LeoWatti99/CANTram-Framework/Doxygen/latex/d3/db6/_c_a_n_tram_framework_8h_source.tex

\doxysection{CANTram\+Framework.\+h}
\hypertarget{_c_a_n_tram_framework_8h_source}{}\label{_c_a_n_tram_framework_8h_source}\index{C:/Users/leowa/Documents/PlatformIO/Projects/CANTramFrameworkUsage/lib/CANTramFramework/include/CANTramFramework.h@{C:/Users/leowa/Documents/PlatformIO/Projects/CANTramFrameworkUsage/lib/CANTramFramework/include/CANTramFramework.h}}

\begin{DoxyCode}{0}
\DoxyCodeLine{00001\ \textcolor{preprocessor}{\#ifndef\ CAN\_TRAM\_FRAMEWORK\_H}}
\DoxyCodeLine{00002\ \textcolor{preprocessor}{\#define\ CAN\_TRAM\_FRAMEWORK\_H}}
\DoxyCodeLine{00003\ }
\DoxyCodeLine{00004\ \textcolor{preprocessor}{\#include\ <\mbox{\hyperlink{_c_a_n_core_8h}{CANCore.h}}>}}
\DoxyCodeLine{00005\ \textcolor{preprocessor}{\#include\ <\mbox{\hyperlink{_c_a_n_tram_core_8h}{CANTramCore.h}}>}}
\DoxyCodeLine{00006\ \textcolor{preprocessor}{\#include\ <\mbox{\hyperlink{_c_a_n_tram_module_8h}{CANTramModule.h}}>}}
\DoxyCodeLine{00007\ \textcolor{preprocessor}{\#include\ <\mbox{\hyperlink{_hardware_resource_8h}{HardwareResource.h}}>}}
\DoxyCodeLine{00008\ \textcolor{preprocessor}{\#include\ <I2CCore.h>}}
\DoxyCodeLine{00009\ \textcolor{preprocessor}{\#include\ <Interface.h>}}
\DoxyCodeLine{00010\ \textcolor{preprocessor}{\#include\ <\mbox{\hyperlink{_output_definition_8h}{OutputDefinition.h}}>}}
\DoxyCodeLine{00011\ \textcolor{preprocessor}{\#include\ <\mbox{\hyperlink{_p_w_m_core_8h}{PWMCore.h}}>}}
\DoxyCodeLine{00012\ \textcolor{preprocessor}{\#include\ <SPIChip.h>}}
\DoxyCodeLine{00013\ \textcolor{preprocessor}{\#include\ <\mbox{\hyperlink{_u_a_r_t_core_8h}{UARTCore.h}}>}}
\DoxyCodeLine{00014\ \textcolor{preprocessor}{\#include\ <ISO1H816G.h>}}
\DoxyCodeLine{00015\ \textcolor{preprocessor}{\#include\ <ISO1I813T.h>}}
\DoxyCodeLine{00016\ \textcolor{preprocessor}{\#include\ <ISO1I813T\_registers.h>}}
\DoxyCodeLine{00017\ \textcolor{preprocessor}{\#include\ <\mbox{\hyperlink{_m_a_x22531_8h}{MAX22531.h}}>}}
\DoxyCodeLine{00018\ \textcolor{preprocessor}{\#include\ <MAX22531\_registers.h>}}
\DoxyCodeLine{00019\ \textcolor{preprocessor}{\#include\ <\mbox{\hyperlink{_e_s_p32___c_a_n_core_8h}{ESP32\_CANCore.h}}>}}
\DoxyCodeLine{00020\ \textcolor{preprocessor}{\#include\ <ESP32\_I2CCore.h>}}
\DoxyCodeLine{00021\ \textcolor{preprocessor}{\#include\ <ESP32\_UART.h>}}
\DoxyCodeLine{00022\ \textcolor{preprocessor}{\#include\ <ESP32PWMCore.h>}}
\DoxyCodeLine{00023\ \textcolor{preprocessor}{\#include\ <AnalogInput.h>}}
\DoxyCodeLine{00024\ \textcolor{preprocessor}{\#include\ <AnalogOutput.h>}}
\DoxyCodeLine{00025\ \textcolor{preprocessor}{\#include\ <\mbox{\hyperlink{_c_a_n_interface_8h}{CANInterface.h}}>}}
\DoxyCodeLine{00026\ \textcolor{preprocessor}{\#include\ <DigitalInput.h>}}
\DoxyCodeLine{00027\ \textcolor{preprocessor}{\#include\ <DigitalOutput.h>}}
\DoxyCodeLine{00028\ \textcolor{preprocessor}{\#include\ <I2CInterface.h>}}
\DoxyCodeLine{00029\ \textcolor{preprocessor}{\#include\ <RelaisInterface.h>}}
\DoxyCodeLine{00030\ \textcolor{preprocessor}{\#include\ <UARTInterface.h>}}
\DoxyCodeLine{00031\ \textcolor{preprocessor}{\#include\ <\mbox{\hyperlink{_debug_8h}{Debug.h}}>}}
\DoxyCodeLine{00032\ \textcolor{preprocessor}{\#include\ <AnalogModuleV1\_0.h>}}
\DoxyCodeLine{00033\ \textcolor{preprocessor}{\#include\ <BusModule.h>}}
\DoxyCodeLine{00034\ \textcolor{preprocessor}{\#include\ <DigitalModuleV1\_0.h>}}
\DoxyCodeLine{00035\ \textcolor{preprocessor}{\#include\ <\mbox{\hyperlink{_main_module_v1__0_8h}{MainModuleV1\_0.h}}>}}
\DoxyCodeLine{00036\ \textcolor{preprocessor}{\#include\ <RelaisModuleV1\_0.h>}}
\DoxyCodeLine{00037\ }
\DoxyCodeLine{00038\ \textcolor{preprocessor}{\#endif}}

\end{DoxyCode}
