LeoWatti99/CANTram-Framework/Doxygen/latex/d3/dc5/_c_a_n_core_8h.tex

\doxysection{C\+:/\+Users/leowa/\+Documents/\+Platform\+IO/\+Projects/\+CANTram\+Framework\+Usage/lib/\+CANTram\+Framework/include/\+CANCore.h File Reference}
\hypertarget{_c_a_n_core_8h}{}\label{_c_a_n_core_8h}\index{C:/Users/leowa/Documents/PlatformIO/Projects/CANTramFrameworkUsage/lib/CANTramFramework/include/CANCore.h@{C:/Users/leowa/Documents/PlatformIO/Projects/CANTramFrameworkUsage/lib/CANTramFramework/include/CANCore.h}}

Declaration of the \doxylink{class_c_a_n_core}{CANCore} class.  

{\ttfamily \#include $<$Arduino.\+h$>$}\newline
{\ttfamily \#include "{}Hardware\+Resource.\+h"{}}\newline
{\ttfamily \#include "{}Debug.\+h"{}}\newline
Include dependency graph for CANCore.\+h\+:
\nopagebreak
\begin{figure}[H]
\begin{center}
\leavevmode
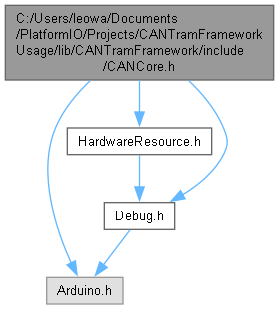
[picture p11: Doxygen/html/d0/d9a/_c_a_n_core_8h__incl.png]

\end{center}
\end{figure}
This graph shows which files directly or indirectly include this file\+:
\nopagebreak
\begin{figure}[H]
\begin{center}
\leavevmode
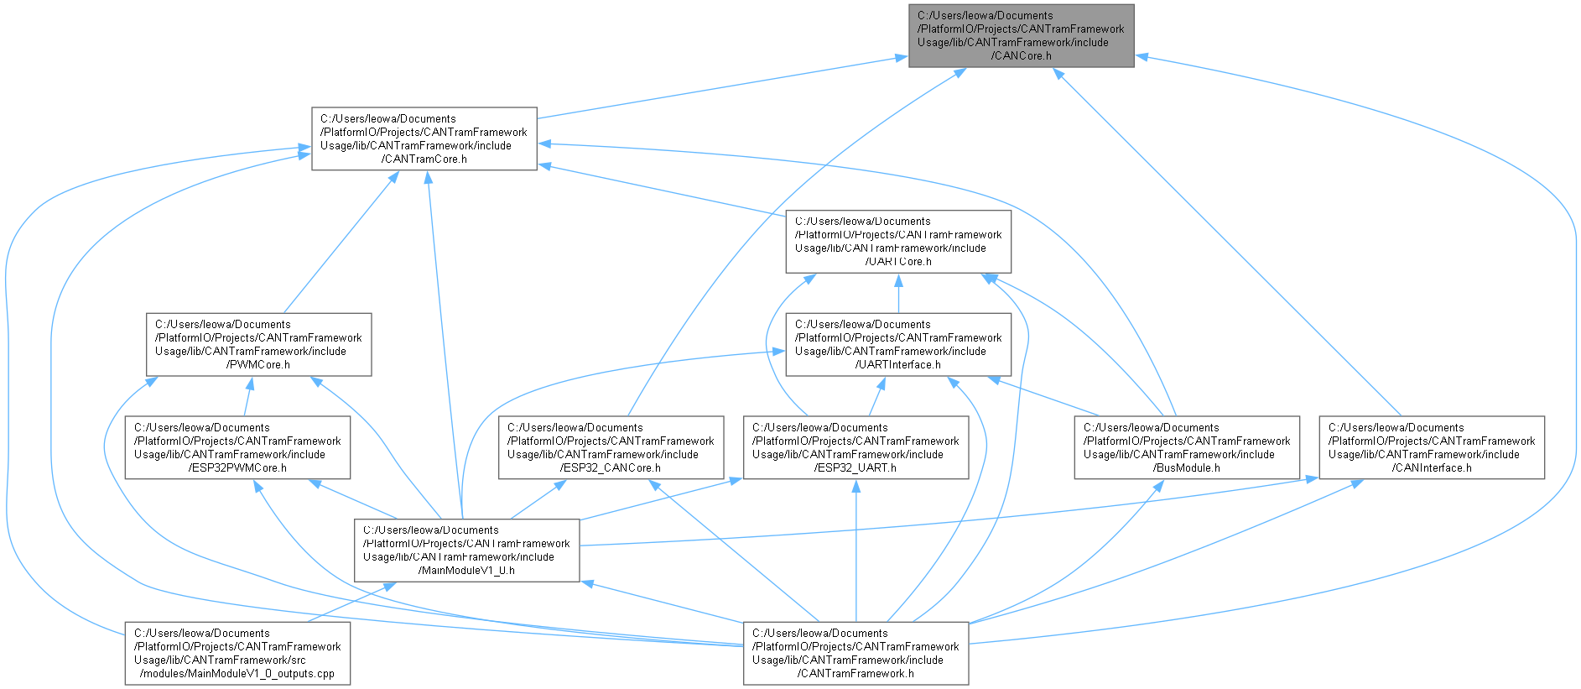
[picture p12: Doxygen/html/d0/ddd/_c_a_n_core_8h__dep__incl.png]

\end{center}
\end{figure}
\doxysubsubsection*{Classes}
\begin{DoxyCompactItemize}
\item 
class \mbox{\hyperlink{class_c_a_n_core}{CANCore}}
\item 
struct \mbox{\hyperlink{struct_c_a_n_core_1_1_c_a_n_message}{CANCore\+::\+CANMessage}}
\end{DoxyCompactItemize}

\doxysubsection{Detailed Description}
Declaration of the \doxylink{class_c_a_n_core}{CANCore} class. 

Defines the \doxylink{class_c_a_n_core}{CANCore} class which provides core functionalities for CAN bus operations in the CANTram system.
