LeoWatti99/CANTram-Framework/Doxygen/latex/d6/d86/_e_s_p32___c_a_n_core_8h.tex

\doxysection{C\+:/\+Users/leowa/\+Documents/\+Platform\+IO/\+Projects/\+CANTram\+Framework\+Usage/lib/\+CANTram\+Framework/include/\+ESP32\+\_\+\+CANCore.h File Reference}
\hypertarget{_e_s_p32___c_a_n_core_8h}{}\label{_e_s_p32___c_a_n_core_8h}\index{C:/Users/leowa/Documents/PlatformIO/Projects/CANTramFrameworkUsage/lib/CANTramFramework/include/ESP32\_CANCore.h@{C:/Users/leowa/Documents/PlatformIO/Projects/CANTramFrameworkUsage/lib/CANTramFramework/include/ESP32\_CANCore.h}}

Declaration of the \doxylink{class_e_s_p32___c_a_n_core}{ESP32\+\_\+\+CANCore} class.  

{\ttfamily \#include "{}CANCore.\+h"{}}\newline
Include dependency graph for ESP32\+\_\+\+CANCore.\+h\+:
\nopagebreak
\begin{figure}[H]
\begin{center}
\leavevmode
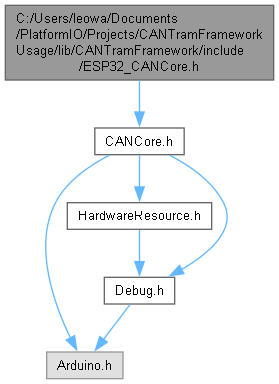
[picture p17: Doxygen/html/d8/d5a/_e_s_p32___c_a_n_core_8h__incl.png]

\end{center}
\end{figure}
This graph shows which files directly or indirectly include this file\+:
\nopagebreak
\begin{figure}[H]
\begin{center}
\leavevmode
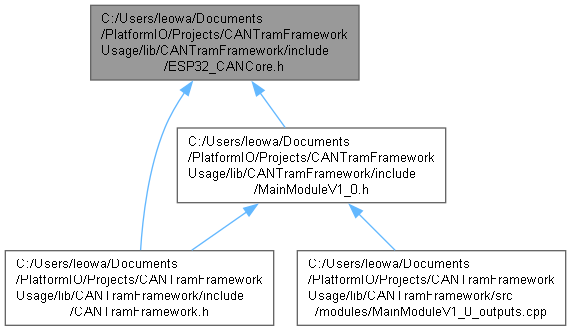
[picture p18: Doxygen/html/d0/d6d/_e_s_p32___c_a_n_core_8h__dep__incl.png]

\end{center}
\end{figure}
\doxysubsubsection*{Classes}
\begin{DoxyCompactItemize}
\item 
class \mbox{\hyperlink{class_e_s_p32___c_a_n_core}{ESP32\+\_\+\+CANCore}}
\end{DoxyCompactItemize}

\doxysubsection{Detailed Description}
Declaration of the \doxylink{class_e_s_p32___c_a_n_core}{ESP32\+\_\+\+CANCore} class. 

Defines the \doxylink{class_e_s_p32___c_a_n_core}{ESP32\+\_\+\+CANCore} class which implements \doxylink{class_c_a_n_core}{CANCore} functionalities for the ESP32 platform using the TWAI driver.
