LeoWatti99/CANTram-Framework/Doxygen/latex/d7/d6e/class_i_s_o1_i813_t.tex

\doxysection{ISO1\+I813T Class Reference}
\hypertarget{class_i_s_o1_i813_t}{}\label{class_i_s_o1_i813_t}\index{ISO1I813T@{ISO1I813T}}

Inheritance diagram for ISO1\+I813T\+:
\nopagebreak
\begin{figure}[H]
\begin{center}
\leavevmode

\end{center}
\end{figure}

Collaboration diagram for ISO1\+I813T\+:
\nopagebreak
\begin{figure}[H]
\begin{center}
\leavevmode

\end{center}
\end{figure}
\doxysubsubsection*{Classes}
\begin{DoxyCompactItemize}
\item 
struct \mbox{\hyperlink{struct_i_s_o1_i813_t_1_1_data}{Data}}
\item 
struct \mbox{\hyperlink{struct_i_s_o1_i813_t_1_1_diag}{Diag}}
\end{DoxyCompactItemize}
\doxysubsubsection*{Public Types}
\begin{DoxyCompactItemize}
\item 
\Hypertarget{class_i_s_o1_i813_t_a42aab5b82c6fc3c49c0b7afa2e7dd207}\label{class_i_s_o1_i813_t_a42aab5b82c6fc3c49c0b7afa2e7dd207} 
enum {\bfseries ISO1\+I813\+T\+\_\+\+Filter} \{ \newline
{\bfseries US\+\_\+50}
, {\bfseries US\+\_\+100}
, {\bfseries US\+\_\+400}
, {\bfseries US\+\_\+800}
, \newline
{\bfseries US\+\_\+1600}
, {\bfseries US\+\_\+3200}
, {\bfseries US\+\_\+10000}
, {\bfseries US\+\_\+20000}
, \newline
{\bfseries FILTER\+\_\+\+OFF}
 \}
\item 
\Hypertarget{class_i_s_o1_i813_t_a82c741cb96c0a4d718da24f12c4746e2}\label{class_i_s_o1_i813_t_a82c741cb96c0a4d718da24f12c4746e2} 
enum {\bfseries ERROR\+\_\+\+CODES} \{ {\bfseries STATUS\+\_\+\+OK} = 0
, {\bfseries INVALID\+\_\+\+CHANNEL} = 10
, {\bfseries INVALID\+\_\+\+FILTER} = 11
, {\bfseries WIRE\+\_\+\+BREAK\+\_\+\+SETTING\+\_\+\+ERROR} = 30
 \}
\end{DoxyCompactItemize}
\doxysubsubsection*{Public Member Functions}
\begin{DoxyCompactItemize}
\item 
\Hypertarget{class_i_s_o1_i813_t_a4baa38cefab23792cde1ddf46cff37d1}\label{class_i_s_o1_i813_t_a4baa38cefab23792cde1ddf46cff37d1} 
{\bfseries ISO1\+I813T} (uint8\+\_\+t cs\+Pin, uint8\+\_\+t sync\+Pin)
\item 
\Hypertarget{class_i_s_o1_i813_t_abe3138513af0bc02e8f47bed0406683e}\label{class_i_s_o1_i813_t_abe3138513af0bc02e8f47bed0406683e} 
void {\bfseries write\+Register} (uint8\+\_\+t address, uint8\+\_\+t data)
\item 
\Hypertarget{class_i_s_o1_i813_t_ab50782d8c2683061052170cc237ac49b}\label{class_i_s_o1_i813_t_ab50782d8c2683061052170cc237ac49b} 
uint8\+\_\+t {\bfseries read\+Register} (uint8\+\_\+t address)
\item 
\Hypertarget{class_i_s_o1_i813_t_af2d28f0eb8b07fd7517ff81d8e09367a}\label{class_i_s_o1_i813_t_af2d28f0eb8b07fd7517ff81d8e09367a} 
void {\bfseries set\+Pins} (uint8\+\_\+t cs\+Pin, uint8\+\_\+t sync\+Pin=-\/1)
\item 
\Hypertarget{class_i_s_o1_i813_t_a23c8c99117d962e3b51f4efae813aec4}\label{class_i_s_o1_i813_t_a23c8c99117d962e3b51f4efae813aec4} 
void {\bfseries begin} ()
\item 
\Hypertarget{class_i_s_o1_i813_t_a7325ff458c752f26bf27cabcd8d4d6ff}\label{class_i_s_o1_i813_t_a7325ff458c752f26bf27cabcd8d4d6ff} 
uint8\+\_\+t {\bfseries get\+Inputs} ()
\item 
\Hypertarget{class_i_s_o1_i813_t_aee537c3332f95e61ade023d4acf195e2}\label{class_i_s_o1_i813_t_aee537c3332f95e61ade023d4acf195e2} 
bool {\bfseries get\+Input} (uint8\+\_\+t input)
\item 
\Hypertarget{class_i_s_o1_i813_t_afcc9b3376d2c442042a8f36f9fd4d59f}\label{class_i_s_o1_i813_t_afcc9b3376d2c442042a8f36f9fd4d59f} 
\mbox{\hyperlink{struct_i_s_o1_i813_t_1_1_data}{Data}} {\bfseries fetch\+Data} ()
\item 
\Hypertarget{class_i_s_o1_i813_t_a2181a4c737b8f0cec97212acc306c83f}\label{class_i_s_o1_i813_t_a2181a4c737b8f0cec97212acc306c83f} 
\mbox{\hyperlink{struct_i_s_o1_i813_t_1_1_diag}{Diag}} {\bfseries fetch\+Diagnose} ()
\item 
\Hypertarget{class_i_s_o1_i813_t_a9680f671fad5368a4dfbb839700f3ed9}\label{class_i_s_o1_i813_t_a9680f671fad5368a4dfbb839700f3ed9} 
uint8\+\_\+t {\bfseries get\+Wire\+Breaks} ()
\item 
\Hypertarget{class_i_s_o1_i813_t_a492202752ef7087ae91dc99e281cd949}\label{class_i_s_o1_i813_t_a492202752ef7087ae91dc99e281cd949} 
bool {\bfseries get\+Wire\+Break} (uint8\+\_\+t wire\+Break)
\item 
\Hypertarget{class_i_s_o1_i813_t_a8fd46c416d5030966d563f9b947dea76}\label{class_i_s_o1_i813_t_a8fd46c416d5030966d563f9b947dea76} 
uint8\+\_\+t {\bfseries set\+Filter} (uint8\+\_\+t channel, ISO1\+I813\+T\+\_\+\+Filter filter)
\item 
\Hypertarget{class_i_s_o1_i813_t_af984ac04ddbef183cb829c80e3815a64}\label{class_i_s_o1_i813_t_af984ac04ddbef183cb829c80e3815a64} 
uint8\+\_\+t {\bfseries set\+Wire\+Break\+Mask} (uint8\+\_\+t channel, bool enable)
\item 
\Hypertarget{class_i_s_o1_i813_t_aa368e087610499e5ae2642f13d96b8a2}\label{class_i_s_o1_i813_t_aa368e087610499e5ae2642f13d96b8a2} 
void {\bfseries freeze} (bool status)
\end{DoxyCompactItemize}
\doxysubsection*{Public Member Functions inherited from \mbox{\hyperlink{class_s_p_i_chip}{SPIChip}}}
\begin{DoxyCompactItemize}
\item 
void {\bfseries activate\+External\+Chip\+Select} ()
\item 
void {\bfseries set\+CSControl\+Callback} (std\+::function$<$ void(bool)$>$ callback)
\item 
void {\bfseries set\+CSPin} (int cs\+Pin)
\end{DoxyCompactItemize}
\doxysubsubsection*{Public Attributes}
\begin{DoxyCompactItemize}
\item 
\Hypertarget{class_i_s_o1_i813_t_a39b30922d58a05b78316fbc46ef48615}\label{class_i_s_o1_i813_t_a39b30922d58a05b78316fbc46ef48615} 
uint8\+\_\+t {\bfseries daisy\+Chain} = 1
\end{DoxyCompactItemize}
\doxysubsubsection*{Additional Inherited Members}
\doxysubsection*{Protected Member Functions inherited from \mbox{\hyperlink{class_s_p_i_chip}{SPIChip}}}
\begin{DoxyCompactItemize}
\item 
{\bfseries SPIChip} (uint8\+\_\+t cs\+Pin)
\item 
void {\bfseries select\+Chip} ()
\item 
void {\bfseries deselect\+Chip} ()
\end{DoxyCompactItemize}
\doxysubsection*{Protected Attributes inherited from \mbox{\hyperlink{class_s_p_i_chip}{SPIChip}}}
\begin{DoxyCompactItemize}
\item 
int {\bfseries \+\_\+cs\+Pin}
\item 
bool {\bfseries use\+External\+Chip\+Select} = false
\item 
std\+::function$<$ void(bool)$>$ {\bfseries cs\+Control} = nullptr
\end{DoxyCompactItemize}

The documentation for this class was generated from the following files\+:\begin{DoxyCompactItemize}
\item 
C\+:/\+Users/leowa/\+Documents/\+Platform\+IO/\+Projects/\+CANTram\+Framework\+Usage/lib/\+CANTram\+Framework/include/ISO1\+I813\+T.\+h\item 
C\+:/\+Users/leowa/\+Documents/\+Platform\+IO/\+Projects/\+CANTram\+Framework\+Usage/lib/\+CANTram\+Framework/src/chips/\+ISO1\+I813\+T/ISO1\+I813\+T.\+cpp\end{DoxyCompactItemize}
