LeoWatti99/CANTram-Framework/Doxygen/latex/d8/d12/_u_a_r_t_core_8h.tex

\doxysection{C\+:/\+Users/leowa/\+Documents/\+Platform\+IO/\+Projects/\+CANTram\+Framework\+Usage/lib/\+CANTram\+Framework/include/\+UARTCore.h File Reference}
\hypertarget{_u_a_r_t_core_8h}{}\label{_u_a_r_t_core_8h}\index{C:/Users/leowa/Documents/PlatformIO/Projects/CANTramFrameworkUsage/lib/CANTramFramework/include/UARTCore.h@{C:/Users/leowa/Documents/PlatformIO/Projects/CANTramFrameworkUsage/lib/CANTramFramework/include/UARTCore.h}}

Abstract base for UART hardware cores and provider interface.  

{\ttfamily \#include "{}CANTram\+Core.\+h"{}}\newline
{\ttfamily \#include "{}Hardware\+Resource.\+h"{}}\newline
Include dependency graph for UARTCore.\+h\+:
\nopagebreak
\begin{figure}[H]
\begin{center}
\leavevmode
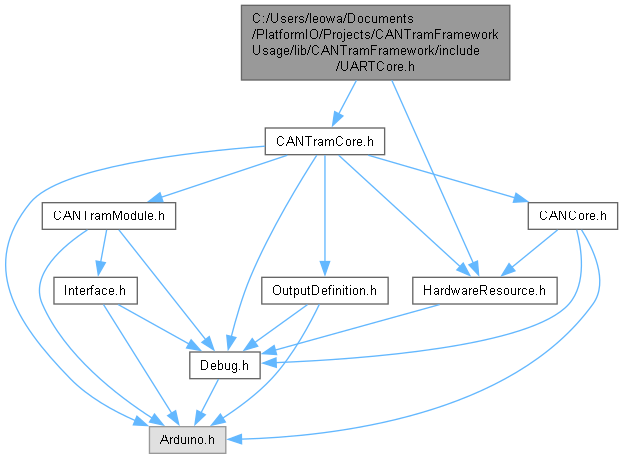
[picture p19: Doxygen/html/d1/db5/_u_a_r_t_core_8h__incl.png]

\end{center}
\end{figure}
This graph shows which files directly or indirectly include this file\+:
\nopagebreak
\begin{figure}[H]
\begin{center}
\leavevmode
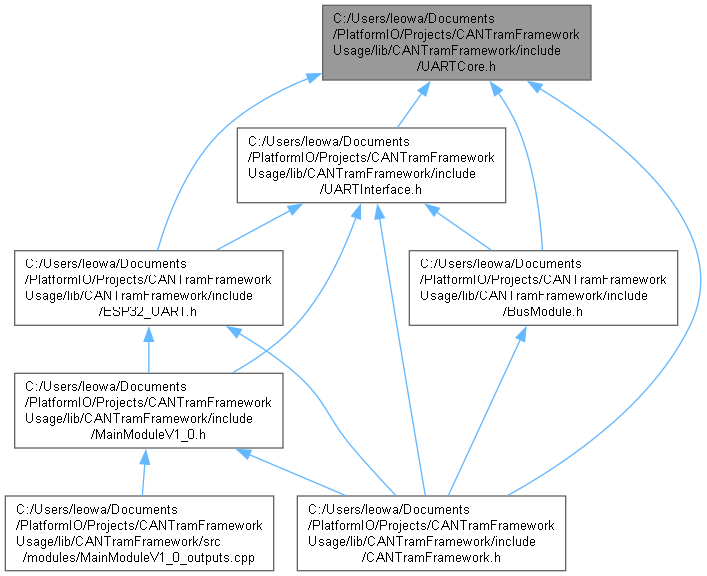
[picture p20: Doxygen/html/d3/d5a/_u_a_r_t_core_8h__dep__incl.png]

\end{center}
\end{figure}
\doxysubsubsection*{Classes}
\begin{DoxyCompactItemize}
\item 
class \mbox{\hyperlink{class_u_a_r_t_core}{UARTCore}}
\begin{DoxyCompactList}\small\item\em Base class for platform-\/specific UART implementations. \end{DoxyCompactList}\item 
class \mbox{\hyperlink{class_u_a_r_t_provider}{UARTProvider}}
\begin{DoxyCompactList}\small\item\em Abstract interface for objects that supply a \doxylink{class_u_a_r_t_core}{UARTCore} instance. \end{DoxyCompactList}\end{DoxyCompactItemize}

\doxysubsection{Detailed Description}
Abstract base for UART hardware cores and provider interface. 

Define the abstract \doxylink{class_u_a_r_t_core}{UARTCore} class which concrete platform implementations must inherit. Provides methods for installation, configuration, pin setup and data IO. Also defines the \doxylink{class_u_a_r_t_provider}{UARTProvider} interface used to obtain \doxylink{class_u_a_r_t_core}{UARTCore} instances.
