LeoWatti99/CANTram-Framework/Doxygen/latex/d8/d9a/class_i_s_o1_h816_g.tex

\doxysection{ISO1\+H816G Class Reference}
\hypertarget{class_i_s_o1_h816_g}{}\label{class_i_s_o1_h816_g}\index{ISO1H816G@{ISO1H816G}}

Inheritance diagram for ISO1\+H816G\+:
\nopagebreak
\begin{figure}[H]
\begin{center}
\leavevmode

\end{center}
\end{figure}

Collaboration diagram for ISO1\+H816G\+:
\nopagebreak
\begin{figure}[H]
\begin{center}
\leavevmode

\end{center}
\end{figure}
\doxysubsubsection*{Public Types}
\begin{DoxyCompactItemize}
\item 
\Hypertarget{class_i_s_o1_h816_g_af6eed698acab2a5f10210b2eef321121}\label{class_i_s_o1_h816_g_af6eed698acab2a5f10210b2eef321121} 
enum {\bfseries ERROR\+\_\+\+CODES} \{ \newline
{\bfseries STATUS\+\_\+\+OK} = 0
, {\bfseries NOT\+\_\+\+INITIALIZED} = 5
, {\bfseries INVALID\+\_\+\+CHANNEL} = 10
, {\bfseries SPI\+\_\+\+FAULT} = 20
, \newline
{\bfseries DISABLE\+\_\+\+PIN\+\_\+\+NOT\+\_\+\+SET} = 30
, {\bfseries DIAG\+\_\+\+PIN\+\_\+\+NOT\+\_\+\+SET} = 40
 \}
\end{DoxyCompactItemize}
\doxysubsubsection*{Public Member Functions}
\begin{DoxyCompactItemize}
\item 
\Hypertarget{class_i_s_o1_h816_g_a287216b98d403aed82645e2dac912a15}\label{class_i_s_o1_h816_g_a287216b98d403aed82645e2dac912a15} 
{\bfseries ISO1\+H816G} (uint8\+\_\+t cs\+Pin, uint8\+\_\+t dis\+Pin, uint8\+\_\+t diag\+Pin)
\item 
\Hypertarget{class_i_s_o1_h816_g_a6be2ce89318f55909b8fb2b3a2eb3ab9}\label{class_i_s_o1_h816_g_a6be2ce89318f55909b8fb2b3a2eb3ab9} 
uint8\+\_\+t {\bfseries begin} ()
\item 
\Hypertarget{class_i_s_o1_h816_g_a6862f2bd9ec8d1830cd48733bd7ebd14}\label{class_i_s_o1_h816_g_a6862f2bd9ec8d1830cd48733bd7ebd14} 
uint8\+\_\+t {\bfseries enable} ()
\item 
\Hypertarget{class_i_s_o1_h816_g_aa518c307897e8098639198e34141f40d}\label{class_i_s_o1_h816_g_aa518c307897e8098639198e34141f40d} 
void {\bfseries disable} ()
\item 
\Hypertarget{class_i_s_o1_h816_g_a803dedb704558920da8fc78956206d85}\label{class_i_s_o1_h816_g_a803dedb704558920da8fc78956206d85} 
bool {\bfseries is\+Enabled} ()
\item 
\Hypertarget{class_i_s_o1_h816_g_a3d545570da0dd21fda6b7d187ccd3b24}\label{class_i_s_o1_h816_g_a3d545570da0dd21fda6b7d187ccd3b24} 
uint8\+\_\+t {\bfseries set\+Outputs} (uint8\+\_\+t outputs)
\item 
\Hypertarget{class_i_s_o1_h816_g_a630682008a651306e4255107a6b2e5fd}\label{class_i_s_o1_h816_g_a630682008a651306e4255107a6b2e5fd} 
uint8\+\_\+t {\bfseries set\+Output} (uint8\+\_\+t output, bool state)
\item 
\Hypertarget{class_i_s_o1_h816_g_ae2383a99d0c07a78625308c2fd7bb1b4}\label{class_i_s_o1_h816_g_ae2383a99d0c07a78625308c2fd7bb1b4} 
uint8\+\_\+t {\bfseries get\+Outputs} ()
\item 
\Hypertarget{class_i_s_o1_h816_g_aa43319850e8a185467ca2f6811e48373}\label{class_i_s_o1_h816_g_aa43319850e8a185467ca2f6811e48373} 
bool {\bfseries get\+Output} (uint8\+\_\+t output)
\item 
\Hypertarget{class_i_s_o1_h816_g_a2dd3c3dd83b7898c980666cba3d495a4}\label{class_i_s_o1_h816_g_a2dd3c3dd83b7898c980666cba3d495a4} 
void {\bfseries set\+SPISettings} (uint32\+\_\+t speed, uint8\+\_\+t bit\+Order, uint8\+\_\+t data\+Mode)
\item 
\Hypertarget{class_i_s_o1_h816_g_aca09498a306a0f11e4bddd8caabd8dc8}\label{class_i_s_o1_h816_g_aca09498a306a0f11e4bddd8caabd8dc8} 
void {\bfseries On\+Fault} (void(\texorpdfstring{$\ast$}{*}callback)(void))
\item 
\Hypertarget{class_i_s_o1_h816_g_a43404bb395036e952a2c7e238e063315}\label{class_i_s_o1_h816_g_a43404bb395036e952a2c7e238e063315} 
void {\bfseries set\+Pins} (uint8\+\_\+t cs\+Pin, uint8\+\_\+t dis\+Pin=-\/1, uint8\+\_\+t diag\+Pin=-\/1)
\end{DoxyCompactItemize}
\doxysubsection*{Public Member Functions inherited from \mbox{\hyperlink{class_s_p_i_chip}{SPIChip}}}
\begin{DoxyCompactItemize}
\item 
void {\bfseries activate\+External\+Chip\+Select} ()
\item 
void {\bfseries set\+CSControl\+Callback} (std\+::function$<$ void(bool)$>$ callback)
\item 
void {\bfseries set\+CSPin} (int cs\+Pin)
\end{DoxyCompactItemize}
\doxysubsubsection*{Additional Inherited Members}
\doxysubsection*{Protected Member Functions inherited from \mbox{\hyperlink{class_s_p_i_chip}{SPIChip}}}
\begin{DoxyCompactItemize}
\item 
{\bfseries SPIChip} (uint8\+\_\+t cs\+Pin)
\item 
void {\bfseries select\+Chip} ()
\item 
void {\bfseries deselect\+Chip} ()
\end{DoxyCompactItemize}
\doxysubsection*{Protected Attributes inherited from \mbox{\hyperlink{class_s_p_i_chip}{SPIChip}}}
\begin{DoxyCompactItemize}
\item 
int {\bfseries \+\_\+cs\+Pin}
\item 
bool {\bfseries use\+External\+Chip\+Select} = false
\item 
std\+::function$<$ void(bool)$>$ {\bfseries cs\+Control} = nullptr
\end{DoxyCompactItemize}

The documentation for this class was generated from the following files\+:\begin{DoxyCompactItemize}
\item 
C\+:/\+Users/leowa/\+Documents/\+Platform\+IO/\+Projects/\+CANTram\+Framework\+Usage/lib/\+CANTram\+Framework/include/ISO1\+H816\+G.\+h\item 
C\+:/\+Users/leowa/\+Documents/\+Platform\+IO/\+Projects/\+CANTram\+Framework\+Usage/lib/\+CANTram\+Framework/src/chips/\+ISO1\+H816\+G/ISO1\+H816\+G.\+cpp\end{DoxyCompactItemize}
