LeoWatti99/CANTram-Framework/Doxygen/latex/d9/d06/class_c_a_n_core.tex

\doxysection{CANCore Class Reference}
\hypertarget{class_c_a_n_core}{}\label{class_c_a_n_core}\index{CANCore@{CANCore}}

Inheritance diagram for CANCore\+:
\nopagebreak
\begin{figure}[H]
\begin{center}
\leavevmode
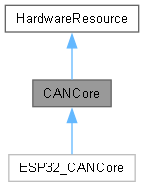
[picture p21: Doxygen/html/d1/d0d/class_c_a_n_core__inherit__graph.png]

\end{center}
\end{figure}

Collaboration diagram for CANCore\+:
\nopagebreak
\begin{figure}[H]
\begin{center}
\leavevmode

\end{center}
\end{figure}
\doxysubsubsection*{Classes}
\begin{DoxyCompactItemize}
\item 
struct \mbox{\hyperlink{struct_c_a_n_core_1_1_c_a_n_message}{CANMessage}}
\end{DoxyCompactItemize}
\doxysubsubsection*{Public Types}
\begin{DoxyCompactItemize}
\item 
\Hypertarget{class_c_a_n_core_a5766804a2230f83a13111a6a9b465e87}\label{class_c_a_n_core_a5766804a2230f83a13111a6a9b465e87} 
enum {\bfseries Baudrate} \{ \newline
{\bfseries BR\+\_\+\+NOT\+\_\+\+SET} = 0
, {\bfseries BR\+\_\+125K} = 125000
, {\bfseries BR\+\_\+250K} = 250000
, {\bfseries BR\+\_\+500K} = 500000
, \newline
{\bfseries BR\+\_\+1M} = 1000000
 \}
\item 
\Hypertarget{class_c_a_n_core_afa2d8dcf4f9255c223f5819e0167cc83}\label{class_c_a_n_core_afa2d8dcf4f9255c223f5819e0167cc83} 
enum {\bfseries Status} \{ {\bfseries STATUS\+\_\+\+OK}
, {\bfseries STATUS\+\_\+\+ERROR\+\_\+\+ACTIVE}
, {\bfseries STATUS\+\_\+\+BUS\+\_\+\+OFF}
, {\bfseries STATUS\+\_\+\+ERROR\+\_\+\+PASSIVE}
 \}
\item 
\Hypertarget{class_c_a_n_core_a78a0c4b32f1455438d9f379c3e659d21}\label{class_c_a_n_core_a78a0c4b32f1455438d9f379c3e659d21} 
enum {\bfseries Filter\+Type} \{ {\bfseries FILTER\+\_\+\+ACCEPT\+\_\+\+ALL}
, {\bfseries FILTER\+\_\+\+MATCH\+\_\+\+ID}
, {\bfseries FILTER\+\_\+\+MASKED}
 \}
\end{DoxyCompactItemize}
\doxysubsection*{Public Types inherited from \mbox{\hyperlink{class_hardware_resource}{Hardware\+Resource}}}
\begin{DoxyCompactItemize}
\item 
enum \mbox{\hyperlink{class_hardware_resource_adead6978be3d7b86c18e3d3e051381e6}{Type}} \{ \newline
\mbox{\hyperlink{class_hardware_resource_adead6978be3d7b86c18e3d3e051381e6ac6f39e4a2dbc764df53048f26209f0a1}{UART}}
, \mbox{\hyperlink{class_hardware_resource_adead6978be3d7b86c18e3d3e051381e6a63a2eead0d2771007afa8c8af281c50d}{SPI}}
, \mbox{\hyperlink{class_hardware_resource_adead6978be3d7b86c18e3d3e051381e6ac77292ec986f613995babba396598dbc}{I2C}}
, \mbox{\hyperlink{class_hardware_resource_adead6978be3d7b86c18e3d3e051381e6ac2fe3e8cc9a9a8fcb39c32be2da214c5}{PWM}}
, \newline
\mbox{\hyperlink{class_hardware_resource_adead6978be3d7b86c18e3d3e051381e6a0ae946256af51077cacc3c0a11575635}{CAN}}
 \}
\begin{DoxyCompactList}\small\item\em Enumeration of hardware resource types. \end{DoxyCompactList}\end{DoxyCompactItemize}
\doxysubsubsection*{Public Member Functions}
\begin{DoxyCompactItemize}
\item 
virtual bool \mbox{\hyperlink{class_c_a_n_core_a26d8d09992a12b0c0f20199dc0e32415}{begin}} ()=0
\item 
virtual bool \mbox{\hyperlink{class_c_a_n_core_a24c2f2e9638aff19ddae3d206e676803}{set\+Baudrate}} (Baudrate baudrate)=0
\item 
virtual bool \mbox{\hyperlink{class_c_a_n_core_ae3b3788f31a71d43bf27116a117a528c}{set\+Pins}} (int8\+\_\+t tx\+Pin, int8\+\_\+t rx\+Pin)=0
\item 
\Hypertarget{class_c_a_n_core_a7a7b37e7eaaee5e9e6445eea8bf2caf9}\label{class_c_a_n_core_a7a7b37e7eaaee5e9e6445eea8bf2caf9} 
virtual bool {\bfseries end} ()=0
\item 
\Hypertarget{class_c_a_n_core_afe4467274cca5fe65f5eb11b5b3e3857}\label{class_c_a_n_core_afe4467274cca5fe65f5eb11b5b3e3857} 
virtual bool {\bfseries send\+Message} (const \mbox{\hyperlink{struct_c_a_n_core_1_1_c_a_n_message}{CANMessage}} \&message)=0
\item 
virtual bool \mbox{\hyperlink{class_c_a_n_core_a615de6f6b06944c4023dc93573bf0c93}{read\+Message}} (\mbox{\hyperlink{struct_c_a_n_core_1_1_c_a_n_message}{CANMessage}} \&message)=0
\item 
virtual uint8\+\_\+t \mbox{\hyperlink{class_c_a_n_core_a0c7c384c24e951410f0ea406f222a889}{available}} ()=0
\item 
\Hypertarget{class_c_a_n_core_a03de55e8a4839a511a65a06f1aeee8b0}\label{class_c_a_n_core_a03de55e8a4839a511a65a06f1aeee8b0} 
virtual bool {\bfseries setup\+Filter} (uint32\+\_\+t id, uint32\+\_\+t mask)=0
\item 
\Hypertarget{class_c_a_n_core_ac71288be80fa6390a5d308fa9a0c5a0f}\label{class_c_a_n_core_ac71288be80fa6390a5d308fa9a0c5a0f} 
Baudrate {\bfseries get\+Baudrate} () const
\item 
\Hypertarget{class_c_a_n_core_a6e3abe29be1ba1a343dc68296787b72e}\label{class_c_a_n_core_a6e3abe29be1ba1a343dc68296787b72e} 
uint8\+\_\+t {\bfseries get\+Tx\+Pin} () const
\item 
\Hypertarget{class_c_a_n_core_a353e8c89313321d1692dcda7fc1bad78}\label{class_c_a_n_core_a353e8c89313321d1692dcda7fc1bad78} 
uint8\+\_\+t {\bfseries get\+Rx\+Pin} () const
\item 
virtual bool \mbox{\hyperlink{class_c_a_n_core_a611efb48b44ea62f1a7b6428671863ca}{reset}} () override
\begin{DoxyCompactList}\small\item\em Reset the hardware resource to a known default state. \end{DoxyCompactList}\end{DoxyCompactItemize}
\doxysubsection*{Public Member Functions inherited from \mbox{\hyperlink{class_hardware_resource}{Hardware\+Resource}}}
\begin{DoxyCompactItemize}
\item 
virtual \mbox{\hyperlink{class_hardware_resource_adead6978be3d7b86c18e3d3e051381e6}{Type}} \mbox{\hyperlink{class_hardware_resource_ad1058e4c12406f756755fad5db55dc77}{get\+Type}} ()=0
\begin{DoxyCompactList}\small\item\em Get the hardware resource type. \end{DoxyCompactList}\item 
bool \mbox{\hyperlink{class_hardware_resource_a26f48b38e5bb1d9bdd47ea2e6de87fdb}{request\+Usage}} ()
\begin{DoxyCompactList}\small\item\em Request a usage slot for this resource. \end{DoxyCompactList}\item 
uint8\+\_\+t \mbox{\hyperlink{class_hardware_resource_a07205354c25627a3bb10ad417e335ff9}{get\+Usages}} ()
\begin{DoxyCompactList}\small\item\em Get the current number of usages of this resource. \end{DoxyCompactList}\item 
bool \mbox{\hyperlink{class_hardware_resource_a569821aa9a34d96ed143488a72e6872b}{is\+Used}} ()
\begin{DoxyCompactList}\small\item\em Check if the resource is currently used. \end{DoxyCompactList}\item 
virtual uint8\+\_\+t \mbox{\hyperlink{class_hardware_resource_a470679cae7880c9ca436755a50f68db4}{get\+Remaining\+Usages}} ()
\begin{DoxyCompactList}\small\item\em Get remaining usage capacity for this resource. \end{DoxyCompactList}\end{DoxyCompactItemize}
\doxysubsubsection*{Protected Attributes}
\begin{DoxyCompactItemize}
\item 
\Hypertarget{class_c_a_n_core_ab745146beb2e090874cd588db806958c}\label{class_c_a_n_core_ab745146beb2e090874cd588db806958c} 
Baudrate {\bfseries \+\_\+baudrate} = BR\+\_\+\+NOT\+\_\+\+SET
\item 
\Hypertarget{class_c_a_n_core_a442ab1c8c57df71c23f4d528ae552cd3}\label{class_c_a_n_core_a442ab1c8c57df71c23f4d528ae552cd3} 
Filter\+Type {\bfseries \+\_\+filter\+Type} = FILTER\+\_\+\+ACCEPT\+\_\+\+ALL
\item 
\Hypertarget{class_c_a_n_core_ac4eba3a674e0020f9984f3fda7f86dcf}\label{class_c_a_n_core_ac4eba3a674e0020f9984f3fda7f86dcf} 
int8\+\_\+t {\bfseries \+\_\+tx\+Pin} = -\/1
\item 
\Hypertarget{class_c_a_n_core_a37aff338c8603e11c0a5f6b14e43cecc}\label{class_c_a_n_core_a37aff338c8603e11c0a5f6b14e43cecc} 
int8\+\_\+t {\bfseries \+\_\+rx\+Pin} = -\/1
\item 
\Hypertarget{class_c_a_n_core_a205154176ea9430d37ca257d826dcef5}\label{class_c_a_n_core_a205154176ea9430d37ca257d826dcef5} 
Status {\bfseries \+\_\+status} = STATUS\+\_\+\+OK
\item 
\Hypertarget{class_c_a_n_core_a77eefc90ada4e08efc0ec6a2f8a688c1}\label{class_c_a_n_core_a77eefc90ada4e08efc0ec6a2f8a688c1} 
bool {\bfseries \+\_\+is\+Initialized} = false
\item 
\Hypertarget{class_c_a_n_core_a230e571fdd8463a3665bfeb00d5aae7f}\label{class_c_a_n_core_a230e571fdd8463a3665bfeb00d5aae7f} 
uint32\+\_\+t {\bfseries \+\_\+filter\+Id} = 0
\item 
\Hypertarget{class_c_a_n_core_ab81d35c60f94ba2dbb5467127e244594}\label{class_c_a_n_core_ab81d35c60f94ba2dbb5467127e244594} 
uint32\+\_\+t {\bfseries \+\_\+filter\+Mask} = 0
\end{DoxyCompactItemize}
\doxysubsection*{Protected Attributes inherited from \mbox{\hyperlink{class_hardware_resource}{Hardware\+Resource}}}
\begin{DoxyCompactItemize}
\item 
uint8\+\_\+t \mbox{\hyperlink{class_hardware_resource_a78845b363f906c0383e91ea912bbddbc}{usages}} =0
\begin{DoxyCompactList}\small\item\em Current usage counter. \end{DoxyCompactList}\end{DoxyCompactItemize}
\doxysubsubsection*{Additional Inherited Members}
\doxysubsection*{Protected Member Functions inherited from \mbox{\hyperlink{class_hardware_resource}{Hardware\+Resource}}}
\begin{DoxyCompactItemize}
\item 
\mbox{\hyperlink{class_hardware_resource_a7ddffb890a743f2df28128d9afd5bfa5}{Hardware\+Resource}} ()=default
\begin{DoxyCompactList}\small\item\em Default constructor. \end{DoxyCompactList}\item 
virtual uint8\+\_\+t \mbox{\hyperlink{class_hardware_resource_a6b7a709561faf5d344b7c3e14bf37558}{get\+Max\+Usages}} ()
\begin{DoxyCompactList}\small\item\em Get the maximum simultaneous usages allowed for this resource. \end{DoxyCompactList}\end{DoxyCompactItemize}

\label{doc-func-members}
\Hypertarget{class_c_a_n_core_doc-func-members}
\doxysubsection{Member Function Documentation}
\Hypertarget{class_c_a_n_core_a0c7c384c24e951410f0ea406f222a889}\index{CANCore@{CANCore}!available@{available}}
\index{available@{available}!CANCore@{CANCore}}
\doxysubsubsection{\texorpdfstring{available()}{available()}}
{\footnotesize\ttfamily \label{class_c_a_n_core_a0c7c384c24e951410f0ea406f222a889} 
virtual uint8\+\_\+t CANCore\+::available (\begin{DoxyParamCaption}{}{}\end{DoxyParamCaption})\hspace{0.3cm}{\ttfamily [pure virtual]}}

Implemented in \mbox{\hyperlink{class_e_s_p32___c_a_n_core_a82b0d9ba535b47648ac951338794509e}{ESP32\+\_\+\+CANCore}}.

\Hypertarget{class_c_a_n_core_a26d8d09992a12b0c0f20199dc0e32415}\index{CANCore@{CANCore}!begin@{begin}}
\index{begin@{begin}!CANCore@{CANCore}}
\doxysubsubsection{\texorpdfstring{begin()}{begin()}}
{\footnotesize\ttfamily \label{class_c_a_n_core_a26d8d09992a12b0c0f20199dc0e32415} 
virtual bool CANCore\+::begin (\begin{DoxyParamCaption}{}{}\end{DoxyParamCaption})\hspace{0.3cm}{\ttfamily [pure virtual]}}

Implemented in \mbox{\hyperlink{class_e_s_p32___c_a_n_core_acf383daa8d43b01883d8008dbbb8fc06}{ESP32\+\_\+\+CANCore}}.

\Hypertarget{class_c_a_n_core_a615de6f6b06944c4023dc93573bf0c93}\index{CANCore@{CANCore}!readMessage@{readMessage}}
\index{readMessage@{readMessage}!CANCore@{CANCore}}
\doxysubsubsection{\texorpdfstring{readMessage()}{readMessage()}}
{\footnotesize\ttfamily \label{class_c_a_n_core_a615de6f6b06944c4023dc93573bf0c93} 
virtual bool CANCore\+::read\+Message (\begin{DoxyParamCaption}\item[{\mbox{\hyperlink{struct_c_a_n_core_1_1_c_a_n_message}{CANMessage}} \&}]{message}{}\end{DoxyParamCaption})\hspace{0.3cm}{\ttfamily [pure virtual]}}

Implemented in \mbox{\hyperlink{class_e_s_p32___c_a_n_core_adbab7ae89e53ad752bc06e789381c4d5}{ESP32\+\_\+\+CANCore}}.

\Hypertarget{class_c_a_n_core_a611efb48b44ea62f1a7b6428671863ca}\index{CANCore@{CANCore}!reset@{reset}}
\index{reset@{reset}!CANCore@{CANCore}}
\doxysubsubsection{\texorpdfstring{reset()}{reset()}}
{\footnotesize\ttfamily \label{class_c_a_n_core_a611efb48b44ea62f1a7b6428671863ca} 
virtual bool CANCore\+::reset (\begin{DoxyParamCaption}{}{}\end{DoxyParamCaption})\hspace{0.3cm}{\ttfamily [inline]}, {\ttfamily [override]}, {\ttfamily [virtual]}}

Reset the hardware resource to a known default state. 

Default implementation clears the usage counter and logs the reset. Derived classes should call the base implementation and perform any additional hardware-\/specific reset steps. \begin{DoxyReturn}{Returns}
true if the reset succeeded, false otherwise. 
\end{DoxyReturn}

Reimplemented from \mbox{\hyperlink{class_hardware_resource_a7372684f2afb5139ef8464194a087649}{Hardware\+Resource}}.

Reimplemented in \mbox{\hyperlink{class_e_s_p32___c_a_n_core_a85a0e3c4965503c96d865bbcc200cd2a}{ESP32\+\_\+\+CANCore}}.

Here is the call graph for this function\+:
\nopagebreak
\begin{figure}[H]
\begin{center}
\leavevmode

\end{center}
\end{figure}
Here is the caller graph for this function\+:
\nopagebreak
\begin{figure}[H]
\begin{center}
\leavevmode

\end{center}
\end{figure}
\Hypertarget{class_c_a_n_core_a24c2f2e9638aff19ddae3d206e676803}\index{CANCore@{CANCore}!setBaudrate@{setBaudrate}}
\index{setBaudrate@{setBaudrate}!CANCore@{CANCore}}
\doxysubsubsection{\texorpdfstring{setBaudrate()}{setBaudrate()}}
{\footnotesize\ttfamily \label{class_c_a_n_core_a24c2f2e9638aff19ddae3d206e676803} 
virtual bool CANCore\+::set\+Baudrate (\begin{DoxyParamCaption}\item[{Baudrate}]{baudrate}{}\end{DoxyParamCaption})\hspace{0.3cm}{\ttfamily [pure virtual]}}

Implemented in \mbox{\hyperlink{class_e_s_p32___c_a_n_core_ad668c0ff123ec46700546e952dad39d5}{ESP32\+\_\+\+CANCore}}.

\Hypertarget{class_c_a_n_core_ae3b3788f31a71d43bf27116a117a528c}\index{CANCore@{CANCore}!setPins@{setPins}}
\index{setPins@{setPins}!CANCore@{CANCore}}
\doxysubsubsection{\texorpdfstring{setPins()}{setPins()}}
{\footnotesize\ttfamily \label{class_c_a_n_core_ae3b3788f31a71d43bf27116a117a528c} 
virtual bool CANCore\+::set\+Pins (\begin{DoxyParamCaption}\item[{int8\+\_\+t}]{tx\+Pin}{, }\item[{int8\+\_\+t}]{rx\+Pin}{}\end{DoxyParamCaption})\hspace{0.3cm}{\ttfamily [pure virtual]}}

Implemented in \mbox{\hyperlink{class_e_s_p32___c_a_n_core_ac11700a4723c67a486fe48ac6d6d66a1}{ESP32\+\_\+\+CANCore}}.

The documentation for this class was generated from the following file\+:\begin{DoxyCompactItemize}
\item 
C\+:/\+Users/leowa/\+Documents/\+Platform\+IO/\+Projects/\+CANTram\+Framework\+Usage/lib/\+CANTram\+Framework/include/\mbox{\hyperlink{_c_a_n_core_8h}{CANCore.\+h}}\end{DoxyCompactItemize}
