LeoWatti99/CANTram-Framework/Doxygen/latex/d9/d4b/class_c_a_n_tram_core.tex

\doxysection{CANTram\+Core Class Reference}
\hypertarget{class_c_a_n_tram_core}{}\label{class_c_a_n_tram_core}\index{CANTramCore@{CANTramCore}}

This static class serves as the core manager for the CANTram modular system. It handles module attachment, GPIO management, hardware resource allocation and cyclic updates of the modules.  

{\ttfamily \#include $<$CANTram\+Core.\+h$>$}

\doxysubsubsection*{Static Public Member Functions}
\begin{DoxyCompactItemize}
\item 
\Hypertarget{class_c_a_n_tram_core_a10c6e60dc0e4cca3ec798a2cbbec5b30}\label{class_c_a_n_tram_core_a10c6e60dc0e4cca3ec798a2cbbec5b30} 
static void {\bfseries set\+Output} (uint8\+\_\+t nr, bool state)
\item 
static bool \mbox{\hyperlink{class_c_a_n_tram_core_ae27c247816847e4df4945bae63f4fadd}{attach\+Module}} (\mbox{\hyperlink{class_c_a_n_tram_module}{CANTram\+Module}} \texorpdfstring{$\ast$}{*}module, int8\+\_\+t index, int8\+\_\+t gpio\+Start)
\begin{DoxyCompactList}\small\item\em Call this function to attach a module to the core. \end{DoxyCompactList}\item 
static bool \mbox{\hyperlink{class_c_a_n_tram_core_aa9da4e441ecc2972d6e565edfa2249f5}{attach\+Module}} (\mbox{\hyperlink{class_c_a_n_tram_module}{CANTram\+Module}} \texorpdfstring{$\ast$}{*}module)
\begin{DoxyCompactList}\small\item\em Call this function to attach a module to next available slot of the core. \end{DoxyCompactList}\item 
\Hypertarget{class_c_a_n_tram_core_aeb91f8e0dc4e7b0301bc09112368079e}\label{class_c_a_n_tram_core_aeb91f8e0dc4e7b0301bc09112368079e} 
static \mbox{\hyperlink{class_c_a_n_tram_module}{CANTram\+Module}} \texorpdfstring{$\ast$}{*} {\bfseries get\+Module} (uint8\+\_\+t index)
\item 
static CANTram\+Core\+Error \mbox{\hyperlink{class_c_a_n_tram_core_a4fe1f36c52a9ff3561351c2390893bc4}{add\+Output\+Definition\+Pointers}} (\mbox{\hyperlink{class_output_definition}{Output\+Definition}} \texorpdfstring{$\ast$}{*}def\mbox{[}$\,$\mbox{]}, uint8\+\_\+t size)
\begin{DoxyCompactList}\small\item\em Call this function to add multiple output definitions to the core. \end{DoxyCompactList}\item 
static CANTram\+Core\+Error \mbox{\hyperlink{class_c_a_n_tram_core_a96f8c5553711f030ffb740a2578e3d5c}{add\+Output\+Definitions}} (\mbox{\hyperlink{class_output_definition}{Output\+Definition}} def\mbox{[}$\,$\mbox{]}, uint8\+\_\+t size)
\begin{DoxyCompactList}\small\item\em Call this function to add multiple output definitions by using their instances to the core. \end{DoxyCompactList}\item 
static CANTram\+Core\+Error \mbox{\hyperlink{class_c_a_n_tram_core_a3bd45401c1ff106db1a07cd6a35bc8b4}{add\+Output\+Definition}} (\mbox{\hyperlink{class_output_definition}{Output\+Definition}} \texorpdfstring{$\ast$}{*}def, uint8\+\_\+t index, bool overwrite=true)
\begin{DoxyCompactList}\small\item\em Call this function to add a single output definition to the core. \end{DoxyCompactList}\item 
static CANTram\+Core\+Error \mbox{\hyperlink{class_c_a_n_tram_core_a0de4045f26bdf25e2eeb3b0b5f34c203}{add\+Output\+Definition}} (\mbox{\hyperlink{class_output_definition}{Output\+Definition}} \texorpdfstring{$\ast$}{*}def)
\begin{DoxyCompactList}\small\item\em Call this function to add a single output definition to the core. \end{DoxyCompactList}\item 
static \mbox{\hyperlink{class_output_definition}{Output\+Definition}} \texorpdfstring{$\ast$}{*} \mbox{\hyperlink{class_c_a_n_tram_core_a327fbf9847ec97e69a1dcfa554650a8d}{get\+Output\+Definition}} (uint8\+\_\+t index)
\begin{DoxyCompactList}\small\item\em Call this function to retrieve a specific output definition without affecting the used count. \end{DoxyCompactList}\item 
static \mbox{\hyperlink{class_output_definition}{Output\+Definition}} \texorpdfstring{$\ast$}{*} \mbox{\hyperlink{class_c_a_n_tram_core_a671c48002cdb950965c9a00395baf0d5}{use\+Output\+Definition}} (uint8\+\_\+t index)
\begin{DoxyCompactList}\small\item\em Call this function to retrieve a specific output definition and raise the count of used output definitions. \end{DoxyCompactList}\item 
static bool \mbox{\hyperlink{class_c_a_n_tram_core_a4c8bf1d786691f0b81228738d8e700d2}{reset}} ()
\begin{DoxyCompactList}\small\item\em Call this function to reset the CANTram core and all attached modules. \end{DoxyCompactList}\item 
static bool \mbox{\hyperlink{class_c_a_n_tram_core_a7ea7863ef4164f0bedf74af378528105}{initialize}} ()
\begin{DoxyCompactList}\small\item\em Call this function to initialize the CANTram core and therefore the controller. \end{DoxyCompactList}\item 
static bool \mbox{\hyperlink{class_c_a_n_tram_core_a75d1f964d2ed65cca8f3eab0dc6bf878}{attach\+Hardware\+Resource}} (\mbox{\hyperlink{class_hardware_resource}{Hardware\+Resource}} \texorpdfstring{$\ast$}{*}resource)
\begin{DoxyCompactList}\small\item\em Call this function to attach a hardware resource to the core. E.\+g., I2C, SPI, UART, PWM. \end{DoxyCompactList}\item 
\Hypertarget{class_c_a_n_tram_core_a29b4c3dd06506fe082473b04acebd977}\label{class_c_a_n_tram_core_a29b4c3dd06506fe082473b04acebd977} 
static \mbox{\hyperlink{class_hardware_resource}{Hardware\+Resource}} \texorpdfstring{$\ast$}{*} {\bfseries use\+Hardware\+Resource} (\mbox{\hyperlink{class_hardware_resource_adead6978be3d7b86c18e3d3e051381e6}{Hardware\+Resource\+::\+Type}} type)
\item 
\Hypertarget{class_c_a_n_tram_core_a6f061feff4408c587e15324add3f4680}\label{class_c_a_n_tram_core_a6f061feff4408c587e15324add3f4680} 
static uint8\+\_\+t {\bfseries get\+Used\+GPIOs} ()
\item 
\Hypertarget{class_c_a_n_tram_core_a61a2dcf82ad609781c749ce7763297a8}\label{class_c_a_n_tram_core_a61a2dcf82ad609781c749ce7763297a8} 
static uint8\+\_\+t {\bfseries get\+Provided\+GPIOs} ()
\item 
\Hypertarget{class_c_a_n_tram_core_ac33ef5f9df997ac61dae042eb2ea7761}\label{class_c_a_n_tram_core_ac33ef5f9df997ac61dae042eb2ea7761} 
static bool {\bfseries add\+Interface} (\mbox{\hyperlink{class_interface}{Interface}} \texorpdfstring{$\ast$}{*}interface)
\item 
\Hypertarget{class_c_a_n_tram_core_a8cd9bf54061e7a81ab81986c8dfb1da5}\label{class_c_a_n_tram_core_a8cd9bf54061e7a81ab81986c8dfb1da5} 
static bool {\bfseries add\+Interfaces} (\mbox{\hyperlink{class_interface}{Interface}} \texorpdfstring{$\ast$}{*}interface\+Array\mbox{[}$\,$\mbox{]}, uint8\+\_\+t size)
\item 
static uint8\+\_\+t \mbox{\hyperlink{class_c_a_n_tram_core_ad90c889bd94797175e8cd9d4079c8b2e}{loop}} ()
\begin{DoxyCompactList}\small\item\em Call this function periodically to allow modules to perform cyclic tasks. \end{DoxyCompactList}\item 
\Hypertarget{class_c_a_n_tram_core_a15af492dc75dd96611a6a7b218cf8023}\label{class_c_a_n_tram_core_a15af492dc75dd96611a6a7b218cf8023} 
static void {\bfseries summary\+Report} ()
\end{DoxyCompactItemize}
\doxysubsubsection*{Static Public Attributes}
\begin{DoxyCompactItemize}
\item 
\Hypertarget{class_c_a_n_tram_core_a8ec4aa314763c77e2be73e2447056269}\label{class_c_a_n_tram_core_a8ec4aa314763c77e2be73e2447056269} 
static CANCore\+::\+Baudrate {\bfseries DEFAULT\+\_\+\+CAN\+\_\+\+BAUDRATE} = CANCore\+::\+BR\+\_\+500K
\end{DoxyCompactItemize}

\doxysubsection{Detailed Description}
This static class serves as the core manager for the CANTram modular system. It handles module attachment, GPIO management, hardware resource allocation and cyclic updates of the modules. 

\label{doc-func-members}
\Hypertarget{class_c_a_n_tram_core_doc-func-members}
\doxysubsection{Member Function Documentation}
\Hypertarget{class_c_a_n_tram_core_a0de4045f26bdf25e2eeb3b0b5f34c203}\index{CANTramCore@{CANTramCore}!addOutputDefinition@{addOutputDefinition}}
\index{addOutputDefinition@{addOutputDefinition}!CANTramCore@{CANTramCore}}
\doxysubsubsection{\texorpdfstring{addOutputDefinition()}{addOutputDefinition()}\hspace{0.1cm}{\footnotesize\ttfamily [1/2]}}
{\footnotesize\ttfamily \label{class_c_a_n_tram_core_a0de4045f26bdf25e2eeb3b0b5f34c203} 
CANTram\+Core\+Error CANTram\+Core\+::add\+Output\+Definition (\begin{DoxyParamCaption}\item[{\mbox{\hyperlink{class_output_definition}{Output\+Definition}} \texorpdfstring{$\ast$}{*}}]{def}{}\end{DoxyParamCaption})\hspace{0.3cm}{\ttfamily [static]}}

Call this function to add a single output definition to the core. 

This function searches for the first available slot in the output definition table and adds the provided definition there. If no slots are available, it returns an error.

\begin{DoxyParams}{Parameters}
{\em def} & Pointer to the output definition to add \\
\hline
\end{DoxyParams}
\begin{DoxyReturn}{Returns}
CANTram\+Core\+Error Error code indicating success or failure 
\end{DoxyReturn}
Here is the call graph for this function\+:
\nopagebreak
\begin{figure}[H]
\begin{center}
\leavevmode

\end{center}
\end{figure}
\Hypertarget{class_c_a_n_tram_core_a3bd45401c1ff106db1a07cd6a35bc8b4}\index{CANTramCore@{CANTramCore}!addOutputDefinition@{addOutputDefinition}}
\index{addOutputDefinition@{addOutputDefinition}!CANTramCore@{CANTramCore}}
\doxysubsubsection{\texorpdfstring{addOutputDefinition()}{addOutputDefinition()}\hspace{0.1cm}{\footnotesize\ttfamily [2/2]}}
{\footnotesize\ttfamily \label{class_c_a_n_tram_core_a3bd45401c1ff106db1a07cd6a35bc8b4} 
CANTram\+Core\+Error CANTram\+Core\+::add\+Output\+Definition (\begin{DoxyParamCaption}\item[{\mbox{\hyperlink{class_output_definition}{Output\+Definition}} \texorpdfstring{$\ast$}{*}}]{def}{, }\item[{uint8\+\_\+t}]{index}{, }\item[{bool}]{overwrite}{ = {\ttfamily true}}\end{DoxyParamCaption})\hspace{0.3cm}{\ttfamily [static]}}

Call this function to add a single output definition to the core. 

\begin{DoxyParams}{Parameters}
{\em def} & Pointer to the output definition to add \\
\hline
{\em index} & Index at which to add the output definition \\
\hline
{\em overwrite} & Flag indicating whether to overwrite an existing definition \\
\hline
\end{DoxyParams}
\begin{DoxyReturn}{Returns}
CANTram\+Core\+Error Error code indicating success or failure 
\end{DoxyReturn}
Here is the call graph for this function\+:
\nopagebreak
\begin{figure}[H]
\begin{center}
\leavevmode

\end{center}
\end{figure}
Here is the caller graph for this function\+:
\nopagebreak
\begin{figure}[H]
\begin{center}
\leavevmode

\end{center}
\end{figure}
\Hypertarget{class_c_a_n_tram_core_a4fe1f36c52a9ff3561351c2390893bc4}\index{CANTramCore@{CANTramCore}!addOutputDefinitionPointers@{addOutputDefinitionPointers}}
\index{addOutputDefinitionPointers@{addOutputDefinitionPointers}!CANTramCore@{CANTramCore}}
\doxysubsubsection{\texorpdfstring{addOutputDefinitionPointers()}{addOutputDefinitionPointers()}}
{\footnotesize\ttfamily \label{class_c_a_n_tram_core_a4fe1f36c52a9ff3561351c2390893bc4} 
CANTram\+Core\+Error CANTram\+Core\+::add\+Output\+Definition\+Pointers (\begin{DoxyParamCaption}\item[{\mbox{\hyperlink{class_output_definition}{Output\+Definition}} \texorpdfstring{$\ast$}{*}}]{def}{\mbox{[}$\,$\mbox{]}, }\item[{uint8\+\_\+t}]{size}{}\end{DoxyParamCaption})\hspace{0.3cm}{\ttfamily [static]}}

Call this function to add multiple output definitions to the core. 

\begin{DoxyParams}{Parameters}
{\em def} & Pointer to the array of output definition pointers \\
\hline
{\em size} & Number of output definitions to add \\
\hline
\end{DoxyParams}
\begin{DoxyReturn}{Returns}
CANTram\+Core\+Error Error code indicating success or failure 
\end{DoxyReturn}
Here is the call graph for this function\+:
\nopagebreak
\begin{figure}[H]
\begin{center}
\leavevmode

\end{center}
\end{figure}
\Hypertarget{class_c_a_n_tram_core_a96f8c5553711f030ffb740a2578e3d5c}\index{CANTramCore@{CANTramCore}!addOutputDefinitions@{addOutputDefinitions}}
\index{addOutputDefinitions@{addOutputDefinitions}!CANTramCore@{CANTramCore}}
\doxysubsubsection{\texorpdfstring{addOutputDefinitions()}{addOutputDefinitions()}}
{\footnotesize\ttfamily \label{class_c_a_n_tram_core_a96f8c5553711f030ffb740a2578e3d5c} 
CANTram\+Core\+Error CANTram\+Core\+::add\+Output\+Definitions (\begin{DoxyParamCaption}\item[{\mbox{\hyperlink{class_output_definition}{Output\+Definition}}}]{def}{\mbox{[}$\,$\mbox{]}, }\item[{uint8\+\_\+t}]{size}{}\end{DoxyParamCaption})\hspace{0.3cm}{\ttfamily [static]}}

Call this function to add multiple output definitions by using their instances to the core. 

\begin{DoxyParams}{Parameters}
{\em def} & Pointer to the array of output definitions \\
\hline
{\em size} & Number of output definitions to add \\
\hline
\end{DoxyParams}
\begin{DoxyReturn}{Returns}
CANTram\+Core\+Error Error code indicating success or failure 
\end{DoxyReturn}
Here is the call graph for this function\+:
\nopagebreak
\begin{figure}[H]
\begin{center}
\leavevmode

\end{center}
\end{figure}
Here is the caller graph for this function\+:
\nopagebreak
\begin{figure}[H]
\begin{center}
\leavevmode

\end{center}
\end{figure}
\Hypertarget{class_c_a_n_tram_core_a75d1f964d2ed65cca8f3eab0dc6bf878}\index{CANTramCore@{CANTramCore}!attachHardwareResource@{attachHardwareResource}}
\index{attachHardwareResource@{attachHardwareResource}!CANTramCore@{CANTramCore}}
\doxysubsubsection{\texorpdfstring{attachHardwareResource()}{attachHardwareResource()}}
{\footnotesize\ttfamily \label{class_c_a_n_tram_core_a75d1f964d2ed65cca8f3eab0dc6bf878} 
bool CANTram\+Core\+::attach\+Hardware\+Resource (\begin{DoxyParamCaption}\item[{\mbox{\hyperlink{class_hardware_resource}{Hardware\+Resource}} \texorpdfstring{$\ast$}{*}}]{resource}{}\end{DoxyParamCaption})\hspace{0.3cm}{\ttfamily [static]}}

Call this function to attach a hardware resource to the core. E.\+g., I2C, SPI, UART, PWM. 

\begin{DoxyParams}{Parameters}
{\em resource} & Pointer to the hardware resource to attach \\
\hline
\end{DoxyParams}
\begin{DoxyReturn}{Returns}
true if the resource was attached successfully, false otherwise 
\end{DoxyReturn}
Here is the call graph for this function\+:
\nopagebreak
\begin{figure}[H]
\begin{center}
\leavevmode

\end{center}
\end{figure}
Here is the caller graph for this function\+:
\nopagebreak
\begin{figure}[H]
\begin{center}
\leavevmode

\end{center}
\end{figure}
\Hypertarget{class_c_a_n_tram_core_aa9da4e441ecc2972d6e565edfa2249f5}\index{CANTramCore@{CANTramCore}!attachModule@{attachModule}}
\index{attachModule@{attachModule}!CANTramCore@{CANTramCore}}
\doxysubsubsection{\texorpdfstring{attachModule()}{attachModule()}\hspace{0.1cm}{\footnotesize\ttfamily [1/2]}}
{\footnotesize\ttfamily \label{class_c_a_n_tram_core_aa9da4e441ecc2972d6e565edfa2249f5} 
bool CANTram\+Core\+::attach\+Module (\begin{DoxyParamCaption}\item[{\mbox{\hyperlink{class_c_a_n_tram_module}{CANTram\+Module}} \texorpdfstring{$\ast$}{*}}]{module}{}\end{DoxyParamCaption})\hspace{0.3cm}{\ttfamily [static]}}

Call this function to attach a module to next available slot of the core. 

\begin{DoxyParams}{Parameters}
{\em module} & Pointer to the module to be attached \\
\hline
\end{DoxyParams}
\begin{DoxyReturn}{Returns}
true if the module was successfully attached, false otherwise 
\end{DoxyReturn}
Here is the call graph for this function\+:
\nopagebreak
\begin{figure}[H]
\begin{center}
\leavevmode

\end{center}
\end{figure}
\Hypertarget{class_c_a_n_tram_core_ae27c247816847e4df4945bae63f4fadd}\index{CANTramCore@{CANTramCore}!attachModule@{attachModule}}
\index{attachModule@{attachModule}!CANTramCore@{CANTramCore}}
\doxysubsubsection{\texorpdfstring{attachModule()}{attachModule()}\hspace{0.1cm}{\footnotesize\ttfamily [2/2]}}
{\footnotesize\ttfamily \label{class_c_a_n_tram_core_ae27c247816847e4df4945bae63f4fadd} 
bool CANTram\+Core\+::attach\+Module (\begin{DoxyParamCaption}\item[{\mbox{\hyperlink{class_c_a_n_tram_module}{CANTram\+Module}} \texorpdfstring{$\ast$}{*}}]{module}{, }\item[{int8\+\_\+t}]{index}{, }\item[{int8\+\_\+t}]{gpio\+Start}{}\end{DoxyParamCaption})\hspace{0.3cm}{\ttfamily [static]}}

Call this function to attach a module to the core. 

This function registers the module, assigns it a slot and GPIO start index, and registers its interfaces and hardware resources with the core. It also checks for maximum module limits and GPIO usage.

\begin{DoxyParams}{Parameters}
{\em module} & Pointer to the module to be attached \\
\hline
{\em index} & \mbox{[}Optional\mbox{]} Slot index for the module \\
\hline
{\em gpio\+Start} & \mbox{[}Optional\mbox{]} GPIO start index for the module \\
\hline
\end{DoxyParams}
\begin{DoxyReturn}{Returns}
true if the module was successfully attached, false otherwise 
\end{DoxyReturn}
Here is the call graph for this function\+:
\nopagebreak
\begin{figure}[H]
\begin{center}
\leavevmode
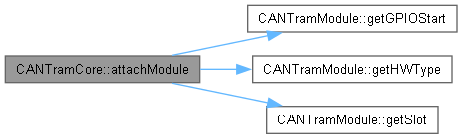
[picture p22: Doxygen/html/d9/d4b/class_c_a_n_tram_core_ae27c247816847e4df4945bae63f4fadd_cgraph.png]

\end{center}
\end{figure}
Here is the caller graph for this function\+:
\nopagebreak
\begin{figure}[H]
\begin{center}
\leavevmode

\end{center}
\end{figure}
\Hypertarget{class_c_a_n_tram_core_a327fbf9847ec97e69a1dcfa554650a8d}\index{CANTramCore@{CANTramCore}!getOutputDefinition@{getOutputDefinition}}
\index{getOutputDefinition@{getOutputDefinition}!CANTramCore@{CANTramCore}}
\doxysubsubsection{\texorpdfstring{getOutputDefinition()}{getOutputDefinition()}}
{\footnotesize\ttfamily \label{class_c_a_n_tram_core_a327fbf9847ec97e69a1dcfa554650a8d} 
\mbox{\hyperlink{class_output_definition}{Output\+Definition}} \texorpdfstring{$\ast$}{*} CANTram\+Core\+::get\+Output\+Definition (\begin{DoxyParamCaption}\item[{uint8\+\_\+t}]{nr}{}\end{DoxyParamCaption})\hspace{0.3cm}{\ttfamily [static]}}

Call this function to retrieve a specific output definition without affecting the used count. 

This function returns a pointer to the output definition at the specified index. If the index is out of bounds or if no definition exists at that index, it returns nullptr and logs an error. Use this command, if you just need information about this output definition but don\textquotesingle{}t want to asign a function to it. 
\begin{DoxyParams}{Parameters}
{\em nr} & Index of the output definition to retrieve \\
\hline
\end{DoxyParams}
\begin{DoxyReturn}{Returns}
Pointer to the requested output definition, or nullptr if not found 
\end{DoxyReturn}
Here is the caller graph for this function\+:
\nopagebreak
\begin{figure}[H]
\begin{center}
\leavevmode
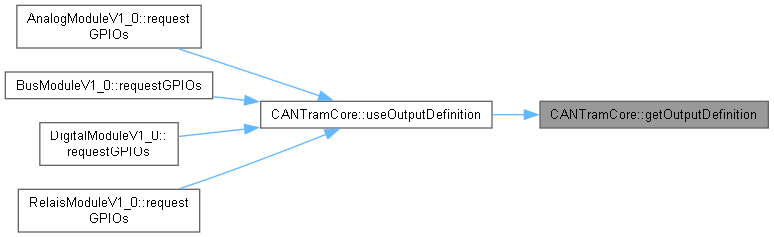
[picture p23: Doxygen/html/d9/d4b/class_c_a_n_tram_core_a327fbf9847ec97e69a1dcfa554650a8d_icgraph.png]

\end{center}
\end{figure}
\Hypertarget{class_c_a_n_tram_core_a7ea7863ef4164f0bedf74af378528105}\index{CANTramCore@{CANTramCore}!initialize@{initialize}}
\index{initialize@{initialize}!CANTramCore@{CANTramCore}}
\doxysubsubsection{\texorpdfstring{initialize()}{initialize()}}
{\footnotesize\ttfamily \label{class_c_a_n_tram_core_a7ea7863ef4164f0bedf74af378528105} 
bool CANTram\+Core\+::initialize (\begin{DoxyParamCaption}{}{}\end{DoxyParamCaption})\hspace{0.3cm}{\ttfamily [static]}}

Call this function to initialize the CANTram core and therefore the controller. 

This function initializes all attached modules and sets initial GPIO values as defined in their output definitions. It should be called after all modules have been attached and configured.

\begin{DoxyReturn}{Returns}
true if initialization was successful, false otherwise 
\end{DoxyReturn}
Here is the call graph for this function\+:
\nopagebreak
\begin{figure}[H]
\begin{center}
\leavevmode

\end{center}
\end{figure}
\Hypertarget{class_c_a_n_tram_core_ad90c889bd94797175e8cd9d4079c8b2e}\index{CANTramCore@{CANTramCore}!loop@{loop}}
\index{loop@{loop}!CANTramCore@{CANTramCore}}
\doxysubsubsection{\texorpdfstring{loop()}{loop()}}
{\footnotesize\ttfamily \label{class_c_a_n_tram_core_ad90c889bd94797175e8cd9d4079c8b2e} 
uint8\+\_\+t CANTram\+Core\+::loop (\begin{DoxyParamCaption}{}{}\end{DoxyParamCaption})\hspace{0.3cm}{\ttfamily [static]}}

Call this function periodically to allow modules to perform cyclic tasks. 

This function iterates through all attached modules and calls their cycle method. It is typically called in the main loop of the program.

\begin{DoxyReturn}{Returns}
uint8\+\_\+t Status code (0 for success) 
\end{DoxyReturn}
\Hypertarget{class_c_a_n_tram_core_a4c8bf1d786691f0b81228738d8e700d2}\index{CANTramCore@{CANTramCore}!reset@{reset}}
\index{reset@{reset}!CANTramCore@{CANTramCore}}
\doxysubsubsection{\texorpdfstring{reset()}{reset()}}
{\footnotesize\ttfamily \label{class_c_a_n_tram_core_a4c8bf1d786691f0b81228738d8e700d2} 
bool CANTram\+Core\+::reset (\begin{DoxyParamCaption}{}{}\end{DoxyParamCaption})\hspace{0.3cm}{\ttfamily [static]}}

Call this function to reset the CANTram core and all attached modules. 

This function performs a complete reset of all CANTram related functions. It resets the internal state of the core, clears the module and hardware resource lists, and resets all attached modules and hardware resources. It should be called to reinitialize the core to a clean state. Normally this function should only be used during testing, but not in production code.

\begin{DoxyReturn}{Returns}
true if the reset was successful, false otherwise 
\end{DoxyReturn}
\Hypertarget{class_c_a_n_tram_core_a671c48002cdb950965c9a00395baf0d5}\index{CANTramCore@{CANTramCore}!useOutputDefinition@{useOutputDefinition}}
\index{useOutputDefinition@{useOutputDefinition}!CANTramCore@{CANTramCore}}
\doxysubsubsection{\texorpdfstring{useOutputDefinition()}{useOutputDefinition()}}
{\footnotesize\ttfamily \label{class_c_a_n_tram_core_a671c48002cdb950965c9a00395baf0d5} 
\mbox{\hyperlink{class_output_definition}{Output\+Definition}} \texorpdfstring{$\ast$}{*} CANTram\+Core\+::use\+Output\+Definition (\begin{DoxyParamCaption}\item[{uint8\+\_\+t}]{nr}{}\end{DoxyParamCaption})\hspace{0.3cm}{\ttfamily [static]}}

Call this function to retrieve a specific output definition and raise the count of used output definitions. 

Use get\+Output\+Definition(...) instead, if you don\textquotesingle{}t want to assign the output to any module. 
\begin{DoxyParams}{Parameters}
{\em nr} & Index of the output definition to retrieve \\
\hline
\end{DoxyParams}
\begin{DoxyReturn}{Returns}
Pointer to the requested output definition, or nullptr if not found 
\end{DoxyReturn}
Here is the call graph for this function\+:
\nopagebreak
\begin{figure}[H]
\begin{center}
\leavevmode

\end{center}
\end{figure}
Here is the caller graph for this function\+:
\nopagebreak
\begin{figure}[H]
\begin{center}
\leavevmode
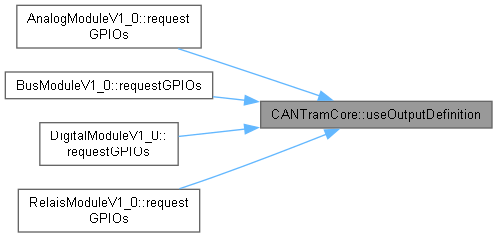
[picture p24: Doxygen/html/d9/d4b/class_c_a_n_tram_core_a671c48002cdb950965c9a00395baf0d5_icgraph.png]

\end{center}
\end{figure}

The documentation for this class was generated from the following files\+:\begin{DoxyCompactItemize}
\item 
C\+:/\+Users/leowa/\+Documents/\+Platform\+IO/\+Projects/\+CANTram\+Framework\+Usage/lib/\+CANTram\+Framework/include/\mbox{\hyperlink{_c_a_n_tram_core_8h}{CANTram\+Core.\+h}}\item 
C\+:/\+Users/leowa/\+Documents/\+Platform\+IO/\+Projects/\+CANTram\+Framework\+Usage/lib/\+CANTram\+Framework/src/abstract/CANTram\+Core.\+cpp\end{DoxyCompactItemize}
