LeoWatti99/CANTram-Framework/Doxygen/latex/d9/d70/struct_i_s_o1_i813_t_1_1_data.tex

\doxysection{ISO1\+I813T\+::Data Struct Reference}
\hypertarget{struct_i_s_o1_i813_t_1_1_data}{}\label{struct_i_s_o1_i813_t_1_1_data}\index{ISO1I813T::Data@{ISO1I813T::Data}}
\doxysubsubsection*{Public Attributes}
\begin{DoxyCompactItemize}
\item 
\Hypertarget{struct_i_s_o1_i813_t_1_1_data_addebb06f6d49208c3a1a735ad3fe7ab6}\label{struct_i_s_o1_i813_t_1_1_data_addebb06f6d49208c3a1a735ad3fe7ab6} 
uint8\+\_\+t {\bfseries inputs}\+: 8
\item 
\Hypertarget{struct_i_s_o1_i813_t_1_1_data_af799e90a21844f919d43dd854ed55de5}\label{struct_i_s_o1_i813_t_1_1_data_af799e90a21844f919d43dd854ed55de5} 
uint8\+\_\+t {\bfseries wire\+Breaks}\+: 8
\end{DoxyCompactItemize}

The documentation for this struct was generated from the following file\+:\begin{DoxyCompactItemize}
\item 
C\+:/\+Users/leowa/\+Documents/\+Platform\+IO/\+Projects/\+CANTram\+Framework\+Usage/lib/\+CANTram\+Framework/include/ISO1\+I813\+T.\+h\end{DoxyCompactItemize}
