LeoWatti99/CANTram-Framework/Doxygen/latex/d9/db1/_main_module_v1__0_8h.tex

\doxysection{C\+:/\+Users/leowa/\+Documents/\+Platform\+IO/\+Projects/\+CANTram\+Framework\+Usage/lib/\+CANTram\+Framework/include/\+Main\+Module\+V1\+\_\+0.h File Reference}
\hypertarget{_main_module_v1__0_8h}{}\label{_main_module_v1__0_8h}\index{C:/Users/leowa/Documents/PlatformIO/Projects/CANTramFrameworkUsage/lib/CANTramFramework/include/MainModuleV1\_0.h@{C:/Users/leowa/Documents/PlatformIO/Projects/CANTramFrameworkUsage/lib/CANTramFramework/include/MainModuleV1\_0.h}}
{\ttfamily \#include $<$Arduino.\+h$>$}\newline
{\ttfamily \#include "{}CANTram\+Module.\+h"{}}\newline
{\ttfamily \#include "{}CANTram\+Core.\+h"{}}\newline
{\ttfamily \#include $<$PWMCore.\+h$>$}\newline
{\ttfamily \#include "{}ESP32\+PWMCore.\+h"{}}\newline
{\ttfamily \#include "{}Output\+Definition.\+h"{}}\newline
{\ttfamily \#include "{}Debug.\+h"{}}\newline
{\ttfamily \#include "{}ESP32\+\_\+\+UART.\+h"{}}\newline
{\ttfamily \#include "{}UARTInterface.\+h"{}}\newline
{\ttfamily \#include "{}Hardware\+Resource.\+h"{}}\newline
{\ttfamily \#include "{}driver/adc.\+h"{}}\newline
{\ttfamily \#include "{}soc/adc\+\_\+channel.\+h"{}}\newline
{\ttfamily \#include "{}esp\+\_\+adc\+\_\+cal.\+h"{}}\newline
{\ttfamily \#include "{}Adafruit\+\_\+\+MCP23\+X17.\+h"{}}\newline
{\ttfamily \#include "{}ESP32\+\_\+\+CANCore.\+h"{}}\newline
{\ttfamily \#include "{}CANInterface.\+h"{}}\newline
{\ttfamily \#include "{}ESP32\+\_\+\+I2\+CCore.\+h"{}}\newline
Include dependency graph for Main\+Module\+V1\+\_\+0.\+h\+:
\nopagebreak
\begin{figure}[H]
\begin{center}
\leavevmode
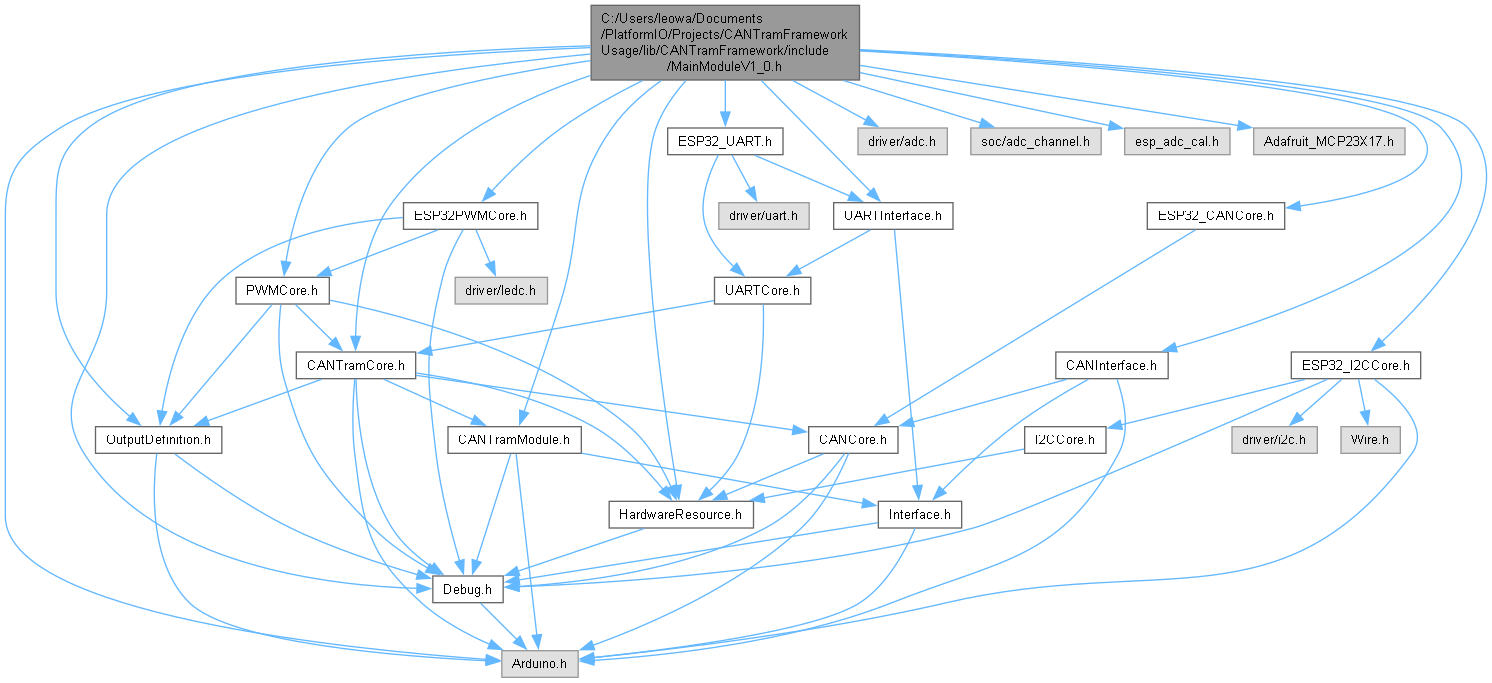
[picture p25: Doxygen/html/d7/d77/_main_module_v1__0_8h__incl.png]

\end{center}
\end{figure}
This graph shows which files directly or indirectly include this file\+:
\nopagebreak
\begin{figure}[H]
\begin{center}
\leavevmode
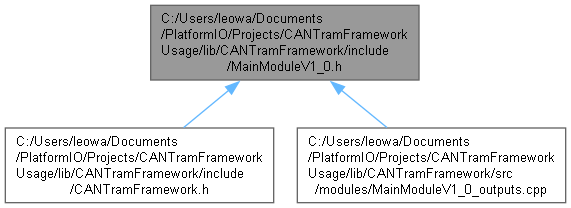
[picture p26: Doxygen/html/dd/dee/_main_module_v1__0_8h__dep__incl.png]

\end{center}
\end{figure}
\doxysubsubsection*{Classes}
\begin{DoxyCompactItemize}
\item 
class \mbox{\hyperlink{class_main_module_v1__0}{Main\+Module\+V1\+\_\+0}}
\end{DoxyCompactItemize}

\doxysubsection{Detailed Description}
\begin{DoxyAuthor}{Author}
your name 
\end{DoxyAuthor}
\begin{DoxyVersion}{Version}
0.\+1 
\end{DoxyVersion}
\begin{DoxyDate}{Date}
2025-\/10-\/09
\end{DoxyDate}
\begin{DoxyCopyright}{Copyright}
Copyright (c) 2025 
\end{DoxyCopyright}
