LeoWatti99/CANTram-Framework/Doxygen/latex/db/dc2/class_output_definition.tex

\doxysection{Output\+Definition Class Reference}
\hypertarget{class_output_definition}{}\label{class_output_definition}\index{OutputDefinition@{OutputDefinition}}

Describes an available output (GPIO or shift register bit).  

{\ttfamily \#include $<$Output\+Definition.\+h$>$}

Collaboration diagram for Output\+Definition\+:
\nopagebreak
\begin{figure}[H]
\begin{center}
\leavevmode
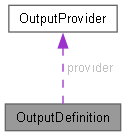
[picture p28: Doxygen/html/dc/dd5/class_output_definition__coll__graph.png]

\end{center}
\end{figure}
\doxysubsubsection*{Public Types}
\begin{DoxyCompactItemize}
\item 
\Hypertarget{class_output_definition_abc71b0eb9167e450639768daf234a764}\label{class_output_definition_abc71b0eb9167e450639768daf234a764} 
enum {\bfseries Configuration\+Mode} \{ \newline
{\bfseries MODE\+\_\+\+INPUT}
, {\bfseries MODE\+\_\+\+OUTPUT}
, {\bfseries MODE\+\_\+\+PWM}
, {\bfseries MODE\+\_\+\+INPUT\+\_\+\+PULLUP}
, \newline
{\bfseries MODE\+\_\+\+NONE}
 \}
\end{DoxyCompactItemize}
\doxysubsubsection*{Public Member Functions}
\begin{DoxyCompactItemize}
\item 
\mbox{\hyperlink{class_output_definition_ae4dfe2a4713871cfa51c8acfbf3d8806}{Output\+Definition}} (bool is\+Shift, uint8\+\_\+t pin\+Or\+Bit, bool adc, bool pwm, bool input\+Only, \mbox{\hyperlink{class_output_provider}{Output\+Provider}} \texorpdfstring{$\ast$}{*}provider)
\begin{DoxyCompactList}\small\item\em Construct a new \doxylink{class_output_definition}{Output\+Definition} instance. \end{DoxyCompactList}\item 
\Hypertarget{class_output_definition_a39ab90093f68518e4e6a72319dedd9b6}\label{class_output_definition_a39ab90093f68518e4e6a72319dedd9b6} 
const String {\bfseries Configuration\+Mode\+To\+String} (Configuration\+Mode mode)
\item 
String \mbox{\hyperlink{class_output_definition_a64751373cfe44aba6a60b2a2ad276710}{to\+String}} ()
\begin{DoxyCompactList}\small\item\em Create a human-\/readable string describing the \doxylink{class_output_definition}{Output\+Definition}. \end{DoxyCompactList}\end{DoxyCompactItemize}
\doxysubsubsection*{Public Attributes}
\begin{DoxyCompactItemize}
\item 
\Hypertarget{class_output_definition_a02cafd65fa7808e120ab1d1d88c5bc2e}\label{class_output_definition_a02cafd65fa7808e120ab1d1d88c5bc2e} 
const bool {\bfseries is\+Shift}
\item 
\Hypertarget{class_output_definition_a578f0b9e3d570129cf2180b0ab1c5bc5}\label{class_output_definition_a578f0b9e3d570129cf2180b0ab1c5bc5} 
const uint8\+\_\+t {\bfseries pin\+Or\+Bit}
\item 
\Hypertarget{class_output_definition_a739737e8f6bd5ca7b5d5366241e9fd80}\label{class_output_definition_a739737e8f6bd5ca7b5d5366241e9fd80} 
const bool {\bfseries adc}
\item 
\Hypertarget{class_output_definition_a4779b8ab3ef79fdbab3b4f2e978166d3}\label{class_output_definition_a4779b8ab3ef79fdbab3b4f2e978166d3} 
const bool {\bfseries pwm}
\item 
\Hypertarget{class_output_definition_a62c6e032bcfe1dbce458941fa566860b}\label{class_output_definition_a62c6e032bcfe1dbce458941fa566860b} 
const bool {\bfseries input\+Only}
\item 
\Hypertarget{class_output_definition_a6a164ff445c309f77b0aeb5986ce113f}\label{class_output_definition_a6a164ff445c309f77b0aeb5986ce113f} 
Configuration\+Mode {\bfseries mode} = MODE\+\_\+\+NONE
\item 
\Hypertarget{class_output_definition_a62303dbf019c726fbc051d8268757d4f}\label{class_output_definition_a62303dbf019c726fbc051d8268757d4f} 
\mbox{\hyperlink{class_output_provider}{Output\+Provider}} \texorpdfstring{$\ast$}{*} {\bfseries provider}
\item 
\Hypertarget{class_output_definition_ac3561e68505919b765e3c08392984ffe}\label{class_output_definition_ac3561e68505919b765e3c08392984ffe} 
bool {\bfseries initial\+Value} = LOW
\end{DoxyCompactItemize}

\doxysubsection{Detailed Description}
Describes an available output (GPIO or shift register bit). 

Holds metadata about an output such as whether it is on a shift register, the pin/bit identifier, and capabilities (ADC, PWM, input-\/only). Also stores a pointer to the \doxylink{class_output_provider}{Output\+Provider} responsible for configuring/controlling the physical output. 

\label{doc-constructors}
\Hypertarget{class_output_definition_doc-constructors}
\doxysubsection{Constructor \& Destructor Documentation}
\Hypertarget{class_output_definition_ae4dfe2a4713871cfa51c8acfbf3d8806}\index{OutputDefinition@{OutputDefinition}!OutputDefinition@{OutputDefinition}}
\index{OutputDefinition@{OutputDefinition}!OutputDefinition@{OutputDefinition}}
\doxysubsubsection{\texorpdfstring{OutputDefinition()}{OutputDefinition()}}
{\footnotesize\ttfamily \label{class_output_definition_ae4dfe2a4713871cfa51c8acfbf3d8806} 
Output\+Definition\+::\+Output\+Definition (\begin{DoxyParamCaption}\item[{bool}]{is\+Shift}{, }\item[{uint8\+\_\+t}]{pin\+Or\+Bit}{, }\item[{bool}]{adc}{, }\item[{bool}]{pwm}{, }\item[{bool}]{input\+Only}{, }\item[{\mbox{\hyperlink{class_output_provider}{Output\+Provider}} \texorpdfstring{$\ast$}{*}}]{provider}{}\end{DoxyParamCaption})\hspace{0.3cm}{\ttfamily [inline]}}

Construct a new \doxylink{class_output_definition}{Output\+Definition} instance. 

Initializes the definition fields describing the output and records the provider responsible for manipulating the physical pin/bit. 
\begin{DoxyParams}{Parameters}
{\em is\+Shift} & True if the output is implemented on a shift register rather than a MCU pin. \\
\hline
{\em pin\+Or\+Bit} & Pin number or bit index identifying the physical output. \\
\hline
{\em adc} & True if the output supports ADC (analog input) functionality. \\
\hline
{\em pwm} & True if the output supports PWM output. \\
\hline
{\em input\+Only} & True if the output is input-\/only (no output capability). \\
\hline
{\em provider} & Pointer to the \doxylink{class_output_provider}{Output\+Provider} that controls this output. \\
\hline
\end{DoxyParams}

\label{doc-func-members}
\Hypertarget{class_output_definition_doc-func-members}
\doxysubsection{Member Function Documentation}
\Hypertarget{class_output_definition_a64751373cfe44aba6a60b2a2ad276710}\index{OutputDefinition@{OutputDefinition}!toString@{toString}}
\index{toString@{toString}!OutputDefinition@{OutputDefinition}}
\doxysubsubsection{\texorpdfstring{toString()}{toString()}}
{\footnotesize\ttfamily \label{class_output_definition_a64751373cfe44aba6a60b2a2ad276710} 
String Output\+Definition\+::to\+String (\begin{DoxyParamCaption}{}{}\end{DoxyParamCaption})\hspace{0.3cm}{\ttfamily [inline]}}

Create a human-\/readable string describing the \doxylink{class_output_definition}{Output\+Definition}. 

Produces a textual representation suitable for logging that includes the is\+Shift flag, pin/bit identifier and capability flags. \begin{DoxyReturn}{Returns}
String A formatted description of this \doxylink{class_output_definition}{Output\+Definition}. 
\end{DoxyReturn}
Here is the caller graph for this function\+:
\nopagebreak
\begin{figure}[H]
\begin{center}
\leavevmode
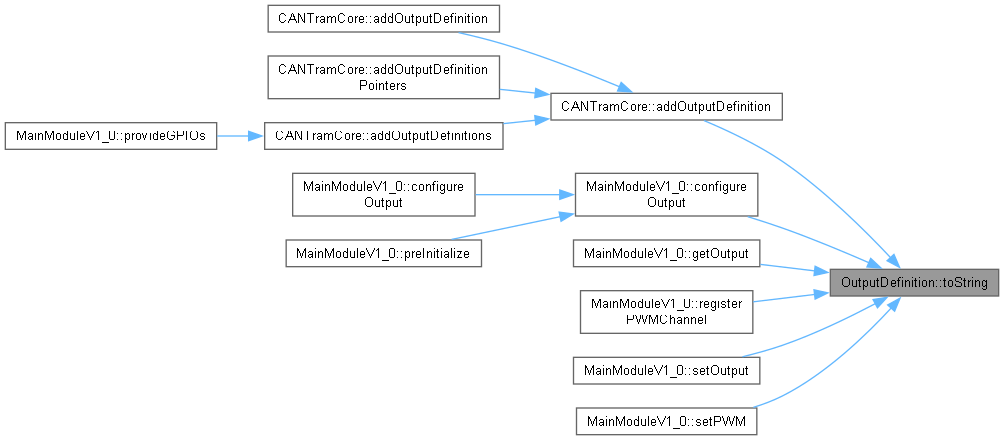
[picture p29: Doxygen/html/db/dc2/class_output_definition_a64751373cfe44aba6a60b2a2ad276710_icgraph.png]

\end{center}
\end{figure}

The documentation for this class was generated from the following file\+:\begin{DoxyCompactItemize}
\item 
C\+:/\+Users/leowa/\+Documents/\+Platform\+IO/\+Projects/\+CANTram\+Framework\+Usage/lib/\+CANTram\+Framework/include/\mbox{\hyperlink{_output_definition_8h}{Output\+Definition.\+h}}\end{DoxyCompactItemize}
