LeoWatti99/CANTram-Framework/Doxygen/latex/db/dc9/_output_definition_8h.tex

\doxysection{C\+:/\+Users/leowa/\+Documents/\+Platform\+IO/\+Projects/\+CANTram\+Framework\+Usage/lib/\+CANTram\+Framework/include/\+Output\+Definition.h File Reference}
\hypertarget{_output_definition_8h}{}\label{_output_definition_8h}\index{C:/Users/leowa/Documents/PlatformIO/Projects/CANTramFrameworkUsage/lib/CANTramFramework/include/OutputDefinition.h@{C:/Users/leowa/Documents/PlatformIO/Projects/CANTramFrameworkUsage/lib/CANTramFramework/include/OutputDefinition.h}}

Definitions for GPIO/output descriptors and provider interfaces.  

{\ttfamily \#include $<$Arduino.\+h$>$}\newline
{\ttfamily \#include "{}Debug.\+h"{}}\newline
Include dependency graph for Output\+Definition.\+h\+:
\nopagebreak
\begin{figure}[H]
\begin{center}
\leavevmode
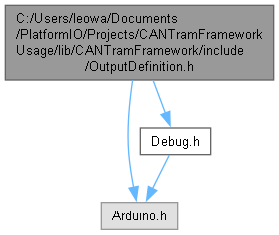
[picture p30: Doxygen/html/d6/d0e/_output_definition_8h__incl.png]

\end{center}
\end{figure}
This graph shows which files directly or indirectly include this file\+:
\nopagebreak
\begin{figure}[H]
\begin{center}
\leavevmode
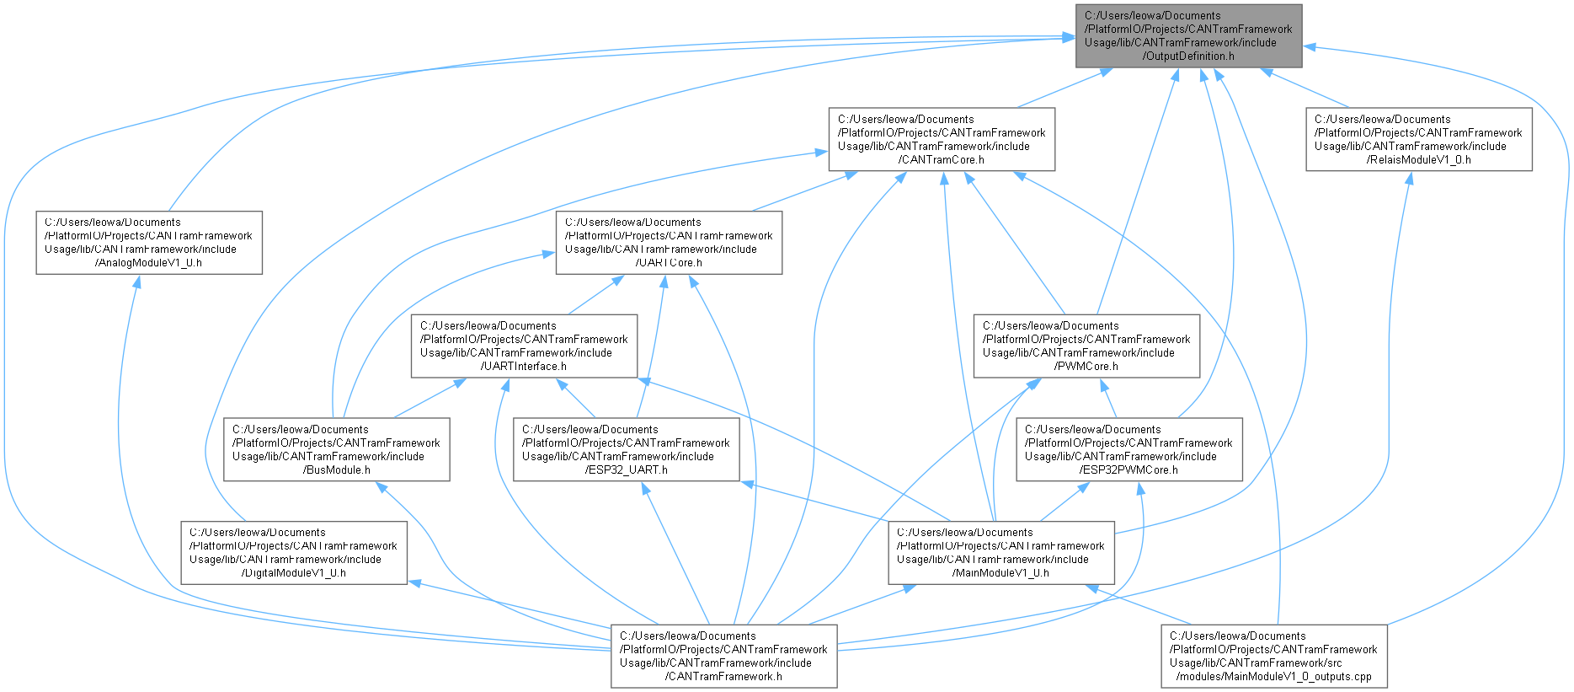
[picture p31: Doxygen/html/d4/d8c/_output_definition_8h__dep__incl.png]

\end{center}
\end{figure}
\doxysubsubsection*{Classes}
\begin{DoxyCompactItemize}
\item 
class \mbox{\hyperlink{class_output_definition}{Output\+Definition}}
\begin{DoxyCompactList}\small\item\em Describes an available output (GPIO or shift register bit). \end{DoxyCompactList}\item 
class \mbox{\hyperlink{class_output_provider}{Output\+Provider}}
\begin{DoxyCompactList}\small\item\em Abstract interface for providers that control outputs. \end{DoxyCompactList}\item 
class \mbox{\hyperlink{class_p_w_m_output_provider}{PWMOutput\+Provider}}
\begin{DoxyCompactList}\small\item\em Extended output provider interface for PWM-\/capable outputs. \end{DoxyCompactList}\end{DoxyCompactItemize}

\doxysubsection{Detailed Description}
Definitions for GPIO/output descriptors and provider interfaces. 

Declares \doxylink{class_output_definition}{Output\+Definition} which describes a single GPIO or shift-\/register bit and abstract Output\+Provider/\+PWMOutput\+Provider interfaces used by \doxylink{class_c_a_n_tram_core}{CANTram\+Core} to configure and control outputs.
