LeoWatti99/CANTram-Framework/Doxygen/latex/dc/d46/class_p_w_m_output_provider.tex

\doxysection{PWMOutput\+Provider Class Reference}
\hypertarget{class_p_w_m_output_provider}{}\label{class_p_w_m_output_provider}\index{PWMOutputProvider@{PWMOutputProvider}}

Extended output provider interface for PWM-\/capable outputs.  

{\ttfamily \#include $<$Output\+Definition.\+h$>$}

Inheritance diagram for PWMOutput\+Provider\+:
\nopagebreak
\begin{figure}[H]
\begin{center}
\leavevmode
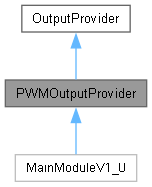
[picture p32: Doxygen/html/dd/d3b/class_p_w_m_output_provider__inherit__graph.png]

\end{center}
\end{figure}

Collaboration diagram for PWMOutput\+Provider\+:
\nopagebreak
\begin{figure}[H]
\begin{center}
\leavevmode

\end{center}
\end{figure}
\doxysubsubsection*{Public Member Functions}
\begin{DoxyCompactItemize}
\item 
virtual bool \mbox{\hyperlink{class_p_w_m_output_provider_a8bee55eeda0ec8908389443cb0b47ac4}{set\+PWM}} (\mbox{\hyperlink{class_output_definition}{Output\+Definition}} \texorpdfstring{$\ast$}{*}def, uint16\+\_\+t value)=0
\begin{DoxyCompactList}\small\item\em Set a PWM value on the specified output. \end{DoxyCompactList}\item 
virtual bool \mbox{\hyperlink{class_p_w_m_output_provider_a61998be15a228bbd6f0d6b179aca623b}{register\+PWMChannel}} (\mbox{\hyperlink{class_output_definition}{Output\+Definition}} \texorpdfstring{$\ast$}{*}def)=0
\begin{DoxyCompactList}\small\item\em Register/allocate a PWM channel for the given output. \end{DoxyCompactList}\end{DoxyCompactItemize}
\doxysubsection*{Public Member Functions inherited from \mbox{\hyperlink{class_output_provider}{Output\+Provider}}}
\begin{DoxyCompactItemize}
\item 
virtual bool \mbox{\hyperlink{class_output_provider_abcb5e82617e9b6aa348290ea77319936}{configure\+Output}} (\mbox{\hyperlink{class_output_definition}{Output\+Definition}} \texorpdfstring{$\ast$}{*}def, Output\+Definition\+::\+Configuration\+Mode mode)=0
\begin{DoxyCompactList}\small\item\em Configure an output\textquotesingle{}s direction/mode. \end{DoxyCompactList}\item 
virtual bool \mbox{\hyperlink{class_output_provider_aafd6e27985454618ea1b21a88f1b4ea3}{set\+Output}} (\mbox{\hyperlink{class_output_definition}{Output\+Definition}} \texorpdfstring{$\ast$}{*}def, bool state)=0
\begin{DoxyCompactList}\small\item\em Set the logical state of an output. \end{DoxyCompactList}\item 
virtual bool \mbox{\hyperlink{class_output_provider_aefcacb21da3e89066b57ae27690549bf}{get\+Output}} (\mbox{\hyperlink{class_output_definition}{Output\+Definition}} \texorpdfstring{$\ast$}{*}def)=0
\begin{DoxyCompactList}\small\item\em Read the current logical state of an output. \end{DoxyCompactList}\item 
virtual void \mbox{\hyperlink{class_output_provider_aa30505769d3096bf35c097c23b762ea2}{enable\+Outputs}} (bool state=true)
\begin{DoxyCompactList}\small\item\em Enable or disable all outputs managed by this provider. \end{DoxyCompactList}\item 
virtual void \mbox{\hyperlink{class_output_provider_ad7ca75c757ecd3411bb00e7631527051}{disable\+Outputs}} ()
\begin{DoxyCompactList}\small\item\em Disable all outputs managed by this provider. \end{DoxyCompactList}\end{DoxyCompactItemize}

\doxysubsection{Detailed Description}
Extended output provider interface for PWM-\/capable outputs. 

Adds PWM-\/specific operations on top of \doxylink{class_output_provider}{Output\+Provider} for setting PWM duty and registering channels. 

\label{doc-func-members}
\Hypertarget{class_p_w_m_output_provider_doc-func-members}
\doxysubsection{Member Function Documentation}
\Hypertarget{class_p_w_m_output_provider_a61998be15a228bbd6f0d6b179aca623b}\index{PWMOutputProvider@{PWMOutputProvider}!registerPWMChannel@{registerPWMChannel}}
\index{registerPWMChannel@{registerPWMChannel}!PWMOutputProvider@{PWMOutputProvider}}
\doxysubsubsection{\texorpdfstring{registerPWMChannel()}{registerPWMChannel()}}
{\footnotesize\ttfamily \label{class_p_w_m_output_provider_a61998be15a228bbd6f0d6b179aca623b} 
virtual bool PWMOutput\+Provider\+::register\+PWMChannel (\begin{DoxyParamCaption}\item[{\mbox{\hyperlink{class_output_definition}{Output\+Definition}} \texorpdfstring{$\ast$}{*}}]{def}{}\end{DoxyParamCaption})\hspace{0.3cm}{\ttfamily [pure virtual]}}

Register/allocate a PWM channel for the given output. 

Request any internal resources needed to drive PWM on the specified output (timer/channel allocation). 
\begin{DoxyParams}{Parameters}
{\em def} & Pointer to the \doxylink{class_output_definition}{Output\+Definition} to register for PWM. \\
\hline
\end{DoxyParams}
\begin{DoxyReturn}{Returns}
bool true if a PWM channel was successfully registered/allocated, false otherwise. 
\end{DoxyReturn}

Implemented in \mbox{\hyperlink{class_main_module_v1__0_a207a1463f359ca72de29492a6c844610}{Main\+Module\+V1\+\_\+0}}.

Here is the caller graph for this function\+:
\nopagebreak
\begin{figure}[H]
\begin{center}
\leavevmode

\end{center}
\end{figure}
\Hypertarget{class_p_w_m_output_provider_a8bee55eeda0ec8908389443cb0b47ac4}\index{PWMOutputProvider@{PWMOutputProvider}!setPWM@{setPWM}}
\index{setPWM@{setPWM}!PWMOutputProvider@{PWMOutputProvider}}
\doxysubsubsection{\texorpdfstring{setPWM()}{setPWM()}}
{\footnotesize\ttfamily \label{class_p_w_m_output_provider_a8bee55eeda0ec8908389443cb0b47ac4} 
virtual bool PWMOutput\+Provider\+::set\+PWM (\begin{DoxyParamCaption}\item[{\mbox{\hyperlink{class_output_definition}{Output\+Definition}} \texorpdfstring{$\ast$}{*}}]{def}{, }\item[{uint16\+\_\+t}]{value}{}\end{DoxyParamCaption})\hspace{0.3cm}{\ttfamily [pure virtual]}}

Set a PWM value on the specified output. 

Drive the output described by def with a PWM duty corresponding to value. Duty scale/units are implementation-\/specific (e.\+g., 0..4095 for 12-\/bit resolution). 
\begin{DoxyParams}{Parameters}
{\em def} & Pointer to the \doxylink{class_output_definition}{Output\+Definition} that supports PWM. \\
\hline
{\em value} & PWM duty value to apply. \\
\hline
\end{DoxyParams}
\begin{DoxyReturn}{Returns}
true if the PWM value was successfully applied, false otherwise. 
\end{DoxyReturn}

Implemented in \mbox{\hyperlink{class_main_module_v1__0_aa8524c0099c7dd70e7e448925c6cf7ee}{Main\+Module\+V1\+\_\+0}}.

Here is the caller graph for this function\+:
\nopagebreak
\begin{figure}[H]
\begin{center}
\leavevmode

\end{center}
\end{figure}

The documentation for this class was generated from the following file\+:\begin{DoxyCompactItemize}
\item 
C\+:/\+Users/leowa/\+Documents/\+Platform\+IO/\+Projects/\+CANTram\+Framework\+Usage/lib/\+CANTram\+Framework/include/\mbox{\hyperlink{_output_definition_8h}{Output\+Definition.\+h}}\end{DoxyCompactItemize}
