LeoWatti99/CANTram-Framework/Doxygen/latex/dd/d7a/_c_a_n_interface_8h.tex

\doxysection{C\+:/\+Users/leowa/\+Documents/\+Platform\+IO/\+Projects/\+CANTram\+Framework\+Usage/lib/\+CANTram\+Framework/include/\+CANInterface.h File Reference}
\hypertarget{_c_a_n_interface_8h}{}\label{_c_a_n_interface_8h}\index{C:/Users/leowa/Documents/PlatformIO/Projects/CANTramFrameworkUsage/lib/CANTramFramework/include/CANInterface.h@{C:/Users/leowa/Documents/PlatformIO/Projects/CANTramFrameworkUsage/lib/CANTramFramework/include/CANInterface.h}}

Declaration of the \doxylink{class_c_a_n_interface}{CANInterface} class.  

{\ttfamily \#include $<$Arduino.\+h$>$}\newline
{\ttfamily \#include "{}Interface.\+h"{}}\newline
{\ttfamily \#include "{}CANCore.\+h"{}}\newline
Include dependency graph for CANInterface.\+h\+:
\nopagebreak
\begin{figure}[H]
\begin{center}
\leavevmode
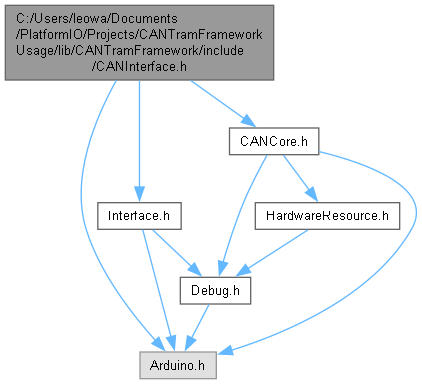
[picture p34: Doxygen/html/dc/d68/_c_a_n_interface_8h__incl.png]

\end{center}
\end{figure}
This graph shows which files directly or indirectly include this file\+:
\nopagebreak
\begin{figure}[H]
\begin{center}
\leavevmode
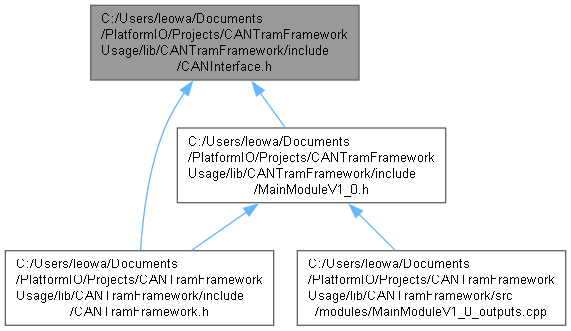
[picture p35: Doxygen/html/d8/dcc/_c_a_n_interface_8h__dep__incl.png]

\end{center}
\end{figure}
\doxysubsubsection*{Classes}
\begin{DoxyCompactItemize}
\item 
class \mbox{\hyperlink{class_c_a_n_interface}{CANInterface}}
\end{DoxyCompactItemize}

\doxysubsection{Detailed Description}
Declaration of the \doxylink{class_c_a_n_interface}{CANInterface} class. 

Defines the \doxylink{class_c_a_n_interface}{CANInterface} class which represents a CAN bus interface in the CANTram system.
