LeoWatti99/CANTram-Framework/Doxygen/latex/dd/dc4/class_u_a_r_t_interface.tex

\doxysection{UARTInterface Class Reference}
\hypertarget{class_u_a_r_t_interface}{}\label{class_u_a_r_t_interface}\index{UARTInterface@{UARTInterface}}

Inheritance diagram for UARTInterface\+:
\nopagebreak
\begin{figure}[H]
\begin{center}
\leavevmode

\end{center}
\end{figure}

Collaboration diagram for UARTInterface\+:
\nopagebreak
\begin{figure}[H]
\begin{center}
\leavevmode

\end{center}
\end{figure}
\doxysubsubsection*{Public Member Functions}
\begin{DoxyCompactItemize}
\item 
Interface\+::\+Type \mbox{\hyperlink{class_u_a_r_t_interface_a647b1a022c5527aed8a82ed95621c429}{get\+Type}} () const override
\item 
\Hypertarget{class_u_a_r_t_interface_a70e6be07080c377a8238e4ca2bc00b3b}\label{class_u_a_r_t_interface_a70e6be07080c377a8238e4ca2bc00b3b} 
void {\bfseries set\+Baudrate} (uint32\+\_\+t baudrate)
\item 
\Hypertarget{class_u_a_r_t_interface_a2bb1133fcd2ccdfcda46a5f0faec6bd1}\label{class_u_a_r_t_interface_a2bb1133fcd2ccdfcda46a5f0faec6bd1} 
void {\bfseries set\+Data\+Bits} (\mbox{\hyperlink{class_u_a_r_t_core_a1895842f7c33678bdf154e12cc617903}{UARTCore\+::\+Data\+Bits}} data\+Bits)
\item 
\Hypertarget{class_u_a_r_t_interface_a05f3560fdea0f8f821a862ad73d37324}\label{class_u_a_r_t_interface_a05f3560fdea0f8f821a862ad73d37324} 
void {\bfseries set\+Parity} (\mbox{\hyperlink{class_u_a_r_t_core_a53addcd39a841913c86bd7e25cca94a0}{UARTCore\+::\+Parity}} parity)
\item 
\Hypertarget{class_u_a_r_t_interface_a607a1921a95175c7134083e6edc4dd49}\label{class_u_a_r_t_interface_a607a1921a95175c7134083e6edc4dd49} 
void {\bfseries set\+Stop\+Bits} (\mbox{\hyperlink{class_u_a_r_t_core_ab88ed673e8897a7804c27ac7d749f00b}{UARTCore\+::\+Stop\+Bits}} stop\+Bits)
\item 
\Hypertarget{class_u_a_r_t_interface_a7afca3baa541adc46cce962c6e49a99f}\label{class_u_a_r_t_interface_a7afca3baa541adc46cce962c6e49a99f} 
bool {\bfseries send} (char data\mbox{[}$\,$\mbox{]}, size\+\_\+t length)
\item 
\Hypertarget{class_u_a_r_t_interface_a297c6d3a20adff81cc931df77c873dc1}\label{class_u_a_r_t_interface_a297c6d3a20adff81cc931df77c873dc1} 
size\+\_\+t {\bfseries read} (char \texorpdfstring{$\ast$}{*}buffer)
\item 
\Hypertarget{class_u_a_r_t_interface_a1f0dbfc250e97272918529a31167258e}\label{class_u_a_r_t_interface_a1f0dbfc250e97272918529a31167258e} 
size\+\_\+t {\bfseries available} ()
\item 
\Hypertarget{class_u_a_r_t_interface_a74b86b7da755c35540fe09f3ac85aaf6}\label{class_u_a_r_t_interface_a74b86b7da755c35540fe09f3ac85aaf6} 
void {\bfseries set\+Uart\+Core} (\mbox{\hyperlink{class_u_a_r_t_core}{UARTCore}} \texorpdfstring{$\ast$}{*}core)
\item 
\Hypertarget{class_u_a_r_t_interface_ada0e4a549cc65904764ffd5af94f325d}\label{class_u_a_r_t_interface_ada0e4a549cc65904764ffd5af94f325d} 
\mbox{\hyperlink{class_u_a_r_t_core}{UARTCore}} \texorpdfstring{$\ast$}{*} {\bfseries get\+Uart\+Core} ()
\end{DoxyCompactItemize}
\doxysubsection*{Public Member Functions inherited from \mbox{\hyperlink{class_interface}{Interface}}}
\begin{DoxyCompactItemize}
\item 
virtual void \mbox{\hyperlink{class_interface_a3ac5ff9b58ddb3323ad28d470850b41e}{setQ}} (uint16\+\_\+t q)
\item 
virtual uint16\+\_\+t {\bfseries getQ} () const
\item 
void {\bfseries rename} (const String \&new\+Name)
\item 
{\footnotesize template$<$typename T$>$ }\\T {\bfseries as} ()
\item 
void {\bfseries validate} ()
\item 
void {\bfseries validate} (bool state)
\item 
void {\bfseries invalidate} ()
\item 
bool {\bfseries is\+Valid} ()
\item 
bool {\bfseries is\+Invalid} ()
\item 
String {\bfseries get\+Name} () const
\end{DoxyCompactItemize}
\doxysubsubsection*{Additional Inherited Members}
\doxysubsection*{Public Types inherited from \mbox{\hyperlink{class_interface}{Interface}}}
\begin{DoxyCompactItemize}
\item 
\Hypertarget{class_interface_a765c7b30069d200e461995c602b98e90}\label{class_interface_a765c7b30069d200e461995c602b98e90} 
enum {\bfseries Resolution} \{ {\bfseries RES\+\_\+8\+BIT} = 8
, {\bfseries RES\+\_\+10\+BIT} = 10
, {\bfseries RES\+\_\+12\+BIT} = 12
, {\bfseries RES\+\_\+16\+BIT} = 16
 \}
\item 
\Hypertarget{class_interface_a01562cbfcb9c8793a7117b67ee0ce079}\label{class_interface_a01562cbfcb9c8793a7117b67ee0ce079} 
enum {\bfseries Type} \{ \newline
{\bfseries DIGITAL\+\_\+\+INPUT}
, {\bfseries DIGITAL\+\_\+\+OUTPUT}
, {\bfseries ANALOG\+\_\+\+INPUT}
, {\bfseries ANALOG\+\_\+\+OUTPUT}
, \newline
{\bfseries RELAIS}
, {\bfseries BUS}
 \}
\end{DoxyCompactItemize}
\doxysubsection*{Protected Attributes inherited from \mbox{\hyperlink{class_interface}{Interface}}}
\begin{DoxyCompactItemize}
\item 
String {\bfseries name}
\item 
uint16\+\_\+t {\bfseries Q} = 0
\item 
bool {\bfseries \+\_\+valid} = false
\item 
bool {\bfseries \+\_\+invalid} = false
\end{DoxyCompactItemize}

\label{doc-func-members}
\Hypertarget{class_u_a_r_t_interface_doc-func-members}
\doxysubsection{Member Function Documentation}
\Hypertarget{class_u_a_r_t_interface_a647b1a022c5527aed8a82ed95621c429}\index{UARTInterface@{UARTInterface}!getType@{getType}}
\index{getType@{getType}!UARTInterface@{UARTInterface}}
\doxysubsubsection{\texorpdfstring{getType()}{getType()}}
{\footnotesize\ttfamily \label{class_u_a_r_t_interface_a647b1a022c5527aed8a82ed95621c429} 
Interface\+::\+Type UARTInterface\+::get\+Type (\begin{DoxyParamCaption}{}{}\end{DoxyParamCaption}) const\hspace{0.3cm}{\ttfamily [inline]}, {\ttfamily [override]}, {\ttfamily [virtual]}}

Implements \mbox{\hyperlink{class_interface}{Interface}}.

The documentation for this class was generated from the following file\+:\begin{DoxyCompactItemize}
\item 
C\+:/\+Users/leowa/\+Documents/\+Platform\+IO/\+Projects/\+CANTram\+Framework\+Usage/lib/\+CANTram\+Framework/include/UARTInterface.\+h\end{DoxyCompactItemize}
