LeoWatti99/CANTram-Framework/Doxygen/latex/df/dcb/_c_a_n_tram_module_8h.tex

\doxysection{C\+:/\+Users/leowa/\+Documents/\+Platform\+IO/\+Projects/\+CANTram\+Framework\+Usage/lib/\+CANTram\+Framework/include/\+CANTram\+Module.h File Reference}
\hypertarget{_c_a_n_tram_module_8h}{}\label{_c_a_n_tram_module_8h}\index{C:/Users/leowa/Documents/PlatformIO/Projects/CANTramFrameworkUsage/lib/CANTramFramework/include/CANTramModule.h@{C:/Users/leowa/Documents/PlatformIO/Projects/CANTramFrameworkUsage/lib/CANTramFramework/include/CANTramModule.h}}

Base class for CANTram hardware modules.  

{\ttfamily \#include $<$Arduino.\+h$>$}\newline
{\ttfamily \#include "{}Interface.\+h"{}}\newline
{\ttfamily \#include "{}Debug.\+h"{}}\newline
Include dependency graph for CANTram\+Module.\+h\+:
\nopagebreak
\begin{figure}[H]
\begin{center}
\leavevmode
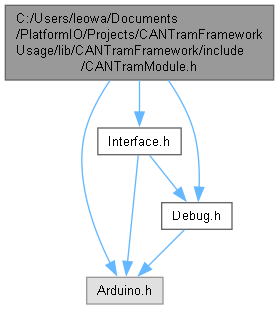
[picture p40: Doxygen/html/d3/dba/_c_a_n_tram_module_8h__incl.png]

\end{center}
\end{figure}
This graph shows which files directly or indirectly include this file\+:
\nopagebreak
\begin{figure}[H]
\begin{center}
\leavevmode
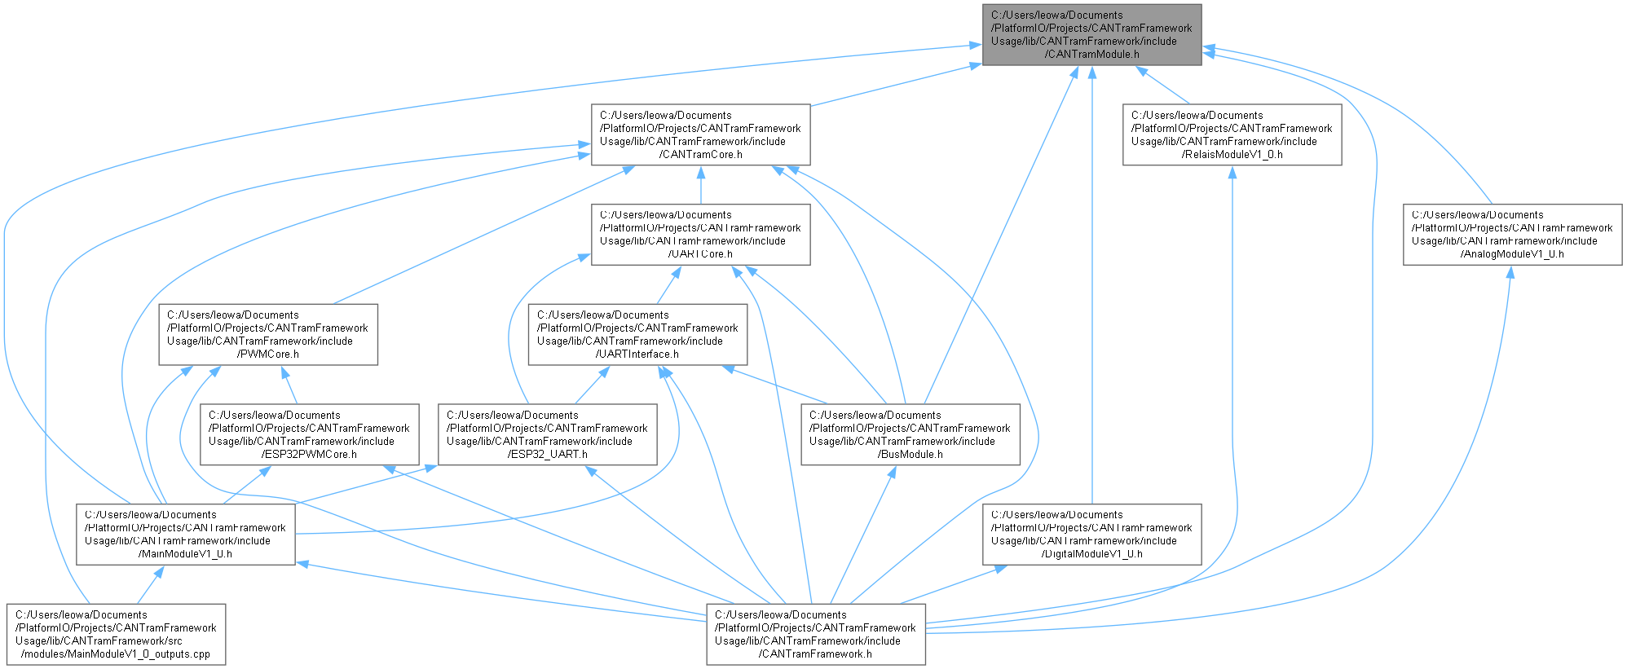
[picture p41: Doxygen/html/de/d2a/_c_a_n_tram_module_8h__dep__incl.png]

\end{center}
\end{figure}
\doxysubsubsection*{Classes}
\begin{DoxyCompactItemize}
\item 
class \mbox{\hyperlink{class_c_a_n_tram_module}{CANTram\+Module}}
\end{DoxyCompactItemize}

\doxysubsection{Detailed Description}
Base class for CANTram hardware modules. 

Declares the abstract \doxylink{class_c_a_n_tram_module}{CANTram\+Module} class which all hardware modules must implement. Provides lifecycle hooks for attachment, GPIO/resource provisioning, initialization and periodic cycling.
