LeoWatti99/CANTram-Framework/Doxygen/latex/d2/d03/class_hardware_resource_a26f48b38e5bb1d9bdd47ea2e6de87fdb_icgraph.pdf

HardwareResource::request
Usage ESP32PWMCore::addChannel
