LeoWatti99/CANTram-Framework/Doxygen/latex/d2/d03/class_hardware_resource_a6b7a709561faf5d344b7c3e14bf37558_icgraph.pdf

HardwareResource::getMax
Usages

HardwareResource::getRemaining Usages

HardwareResource::request
Usage ESP32PWMCore::addChannel
