LeoWatti99/CANTram-Framework/Doxygen/latex/d2/d03/class_hardware_resource_a7372684f2afb5139ef8464194a087649_icgraph.pdf

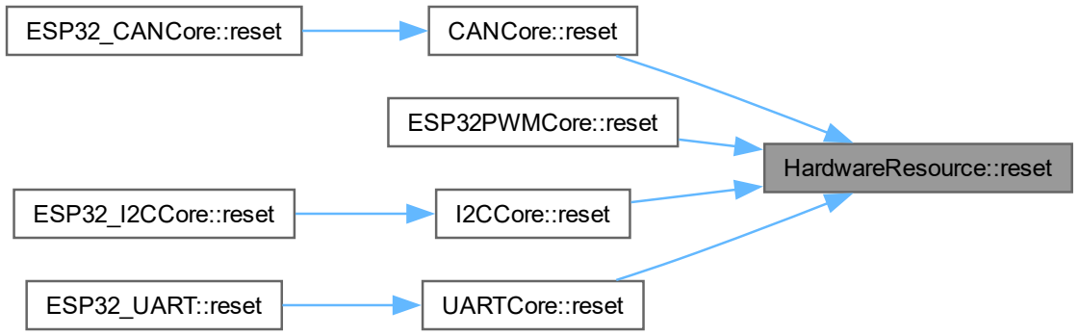
[picture p42: figure]
HardwareResource::reset; CANCore::reset; ESP32PWMCore::reset; I2CCore::reset; UARTCore::reset; ESP32_CANCore::reset; ESP32_I2CCore::reset; ESP32_UART::reset
