LeoWatti99/CANTram-Framework/Doxygen/latex/d2/d03/class_hardware_resource_ad1058e4c12406f756755fad5db55dc77_icgraph.pdf

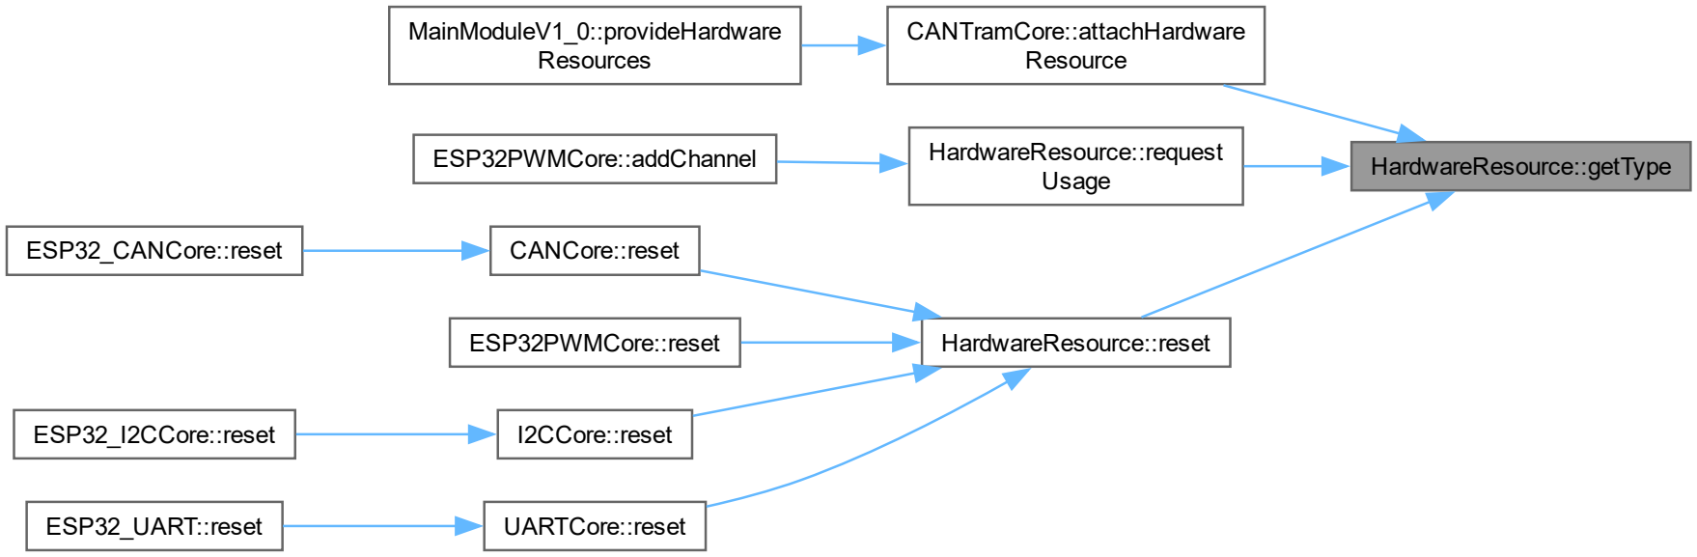
[picture p43: figure]
HardwareResource::getType; CANTramCore::attachHardware Resource; HardwareResource::request Usage; HardwareResource::reset; MainModuleV1_0::provideHardware Resources; ESP32PWMCore::addChannel; CANCore::reset; ESP32PWMCore::reset; I2CCore::reset; UARTCore::reset; ESP32_CANCore::reset; ESP32_I2CCore::reset; ESP32_UART::reset
