LeoWatti99/CANTram-Framework/Doxygen/latex/d6/d4a/class_hardware_resource__inherit__graph.pdf

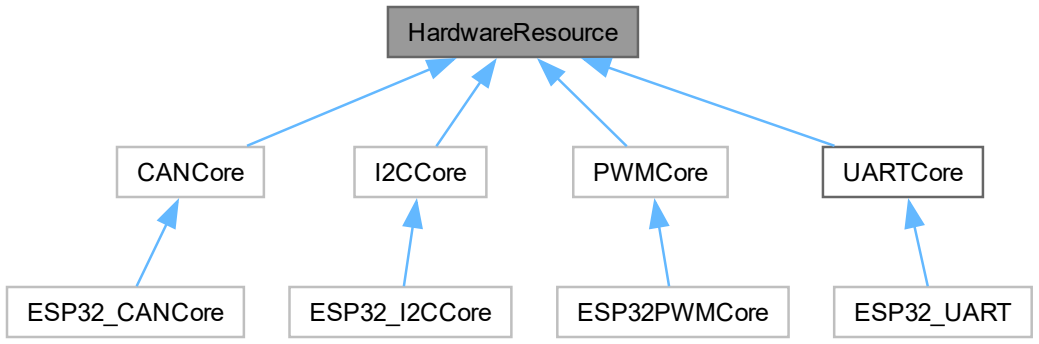
[picture p44: figure]
HardwareResource; CANCore; I2CCore; PWMCore; UARTCore; ESP32_CANCore; ESP32_I2CCore; ESP32PWMCore; ESP32_UART
