LeoWatti99/CANTram-Framework/Doxygen/latex/d8/da0/_hardware_resource_8h__incl.pdf

C:/Users/leowa/Documents
/PlatformIO/Projects/CANTramFramework Usage/lib/CANTramFramework/include /HardwareResource.h

Debug.h

Arduino.h
