LeoWatti99/CANTram-Framework/Doxygen/latex/d0/d4d/class_relais_module_v1__0_a1a7004ca779f46212dde0bd70c0a8bca_cgraph.pdf

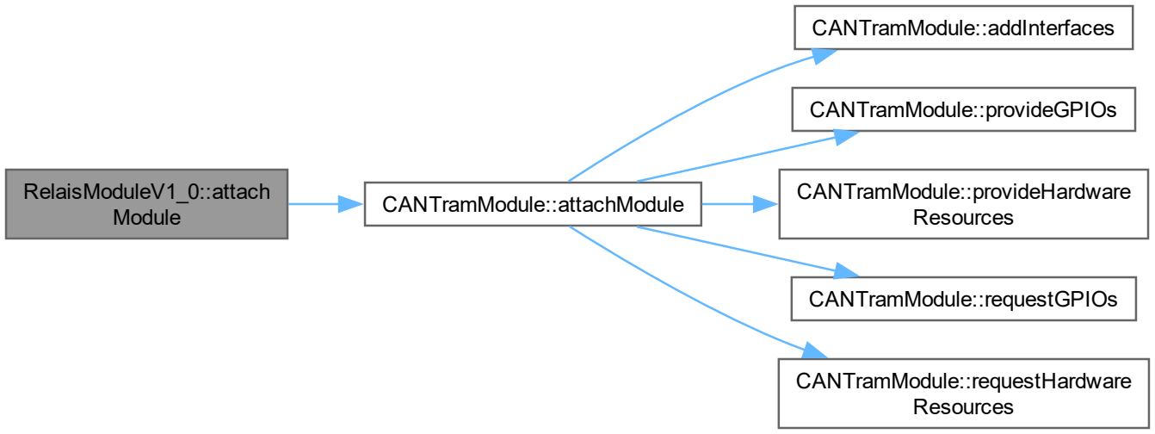
[picture p45: figure]
RelaisModuleV1_0::attach; Module; CANTramModule::attachModule; CANTramModule::addInterfaces; CANTramModule::provideGPIOs; CANTramModule::provideHardware Resources; CANTramModule::requestGPIOs; CANTramModule::requestHardware Resources
