LeoWatti99/CANTram-Framework/Doxygen/latex/d0/d97/class_e_s_p32___i2_c_core_aa3e0817cba1f01e19e046fa27a776eab_cgraph.pdf

ESP32_I2CCore::reset | I2CCore::reset | HardwareResource::reset | HardwareResource::getType
