LeoWatti99/CANTram-Framework/Doxygen/latex/d0/d9a/_c_a_n_core_8h__incl.pdf

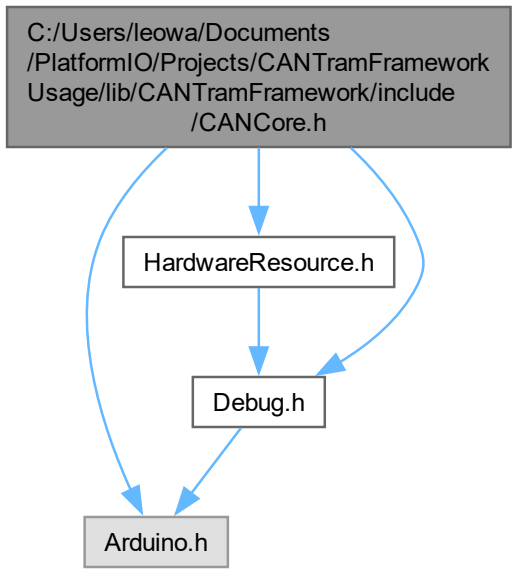
[picture p46: figure]
C:/Users/leowa/Documents /PlatformIO/Projects/CANTramFramework Usage/lib/CANTramFramework/include /CANCore.h; Arduino.h; HardwareResource.h; Debug.h
