LeoWatti99/CANTram-Framework/Doxygen/latex/d0/dd5/class_i2_c_core_a0c8934608811f1a80247981f4e222ce9_cgraph.pdf

I2CCore::reset | HardwareResource::reset | HardwareResource::getType
