LeoWatti99/CANTram-Framework/Doxygen/latex/d1/d0d/class_c_a_n_core__inherit__graph.pdf

CANCore

ESP32_CANCore

HardwareResource
