LeoWatti99/CANTram-Framework/Doxygen/latex/d1/dbd/class_i2_c_core__inherit__graph.pdf

I2CCore

ESP32_I2CCore

HardwareResource
