LeoWatti99/CANTram-Framework/Doxygen/latex/d2/d79/class_main_module_v1__0__coll__graph.pdf

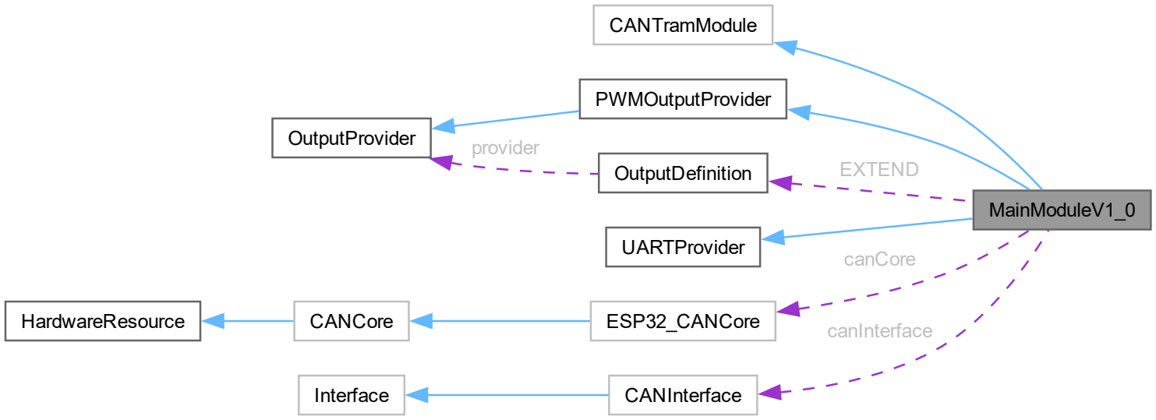
[picture p47: figure]
MainModuleV1_0; CANTramModule; PWMOutputProvider; OutputProvider; OutputDefinition; provider; UARTProvider; EXTEND; ESP32_CANCore; canCore; HardwareResource; CANCore; CANInterface; canInterface; Interface
