LeoWatti99/CANTram-Framework/Doxygen/latex/d2/db0/class_e_s_p32___i2_c_core__coll__graph.pdf

ESP32_I2CCore

I2CCore

HardwareResource
