LeoWatti99/CANTram-Framework/Doxygen/latex/d2/dee/class_c_a_n_tram_module_a14b79b625e82a3f11ebbb8271b6466b7_icgraph.pdf

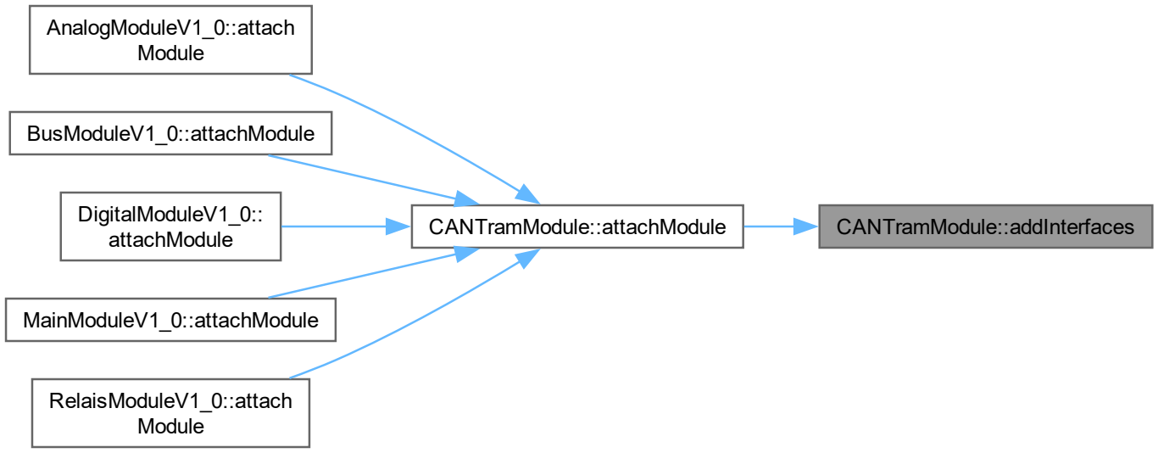
[picture p48: figure]
CANTramModule::attachModule; CANTramModule::addInterfaces; AnalogModuleV1_0::attach Module; BusModuleV1_0::attachModule; DigitalModuleV1_0:: attachModule; MainModuleV1_0::attachModule; RelaisModuleV1_0::attach Module
