LeoWatti99/CANTram-Framework/Doxygen/latex/d2/dee/class_c_a_n_tram_module_a67cab1c238257e6d9b88afc4f644e477_cgraph.pdf

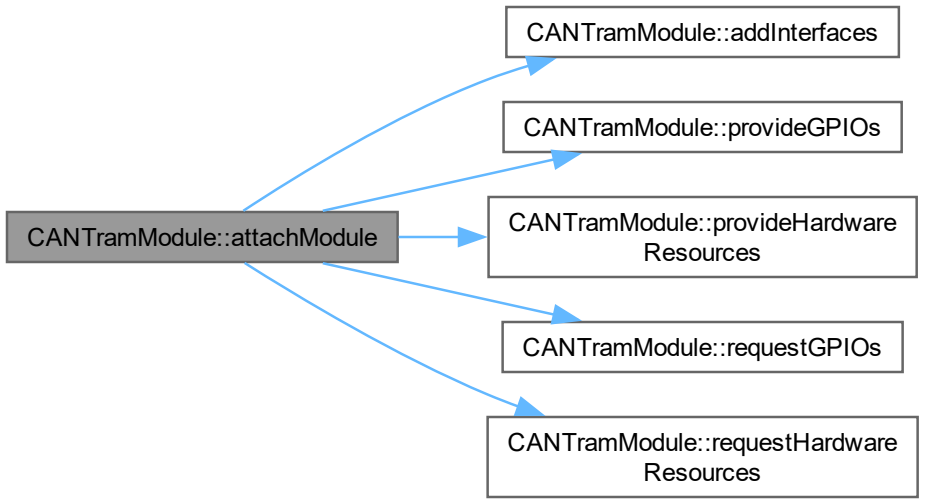
[picture p49: figure]
CANTramModule::attachModule; CANTramModule::addInterfaces; CANTramModule::provideGPIOs; CANTramModule::provideHardware Resources; CANTramModule::requestGPIOs; CANTramModule::requestHardware Resources
