LeoWatti99/CANTram-Framework/Doxygen/latex/d2/dee/class_c_a_n_tram_module_a67cab1c238257e6d9b88afc4f644e477_icgraph.pdf

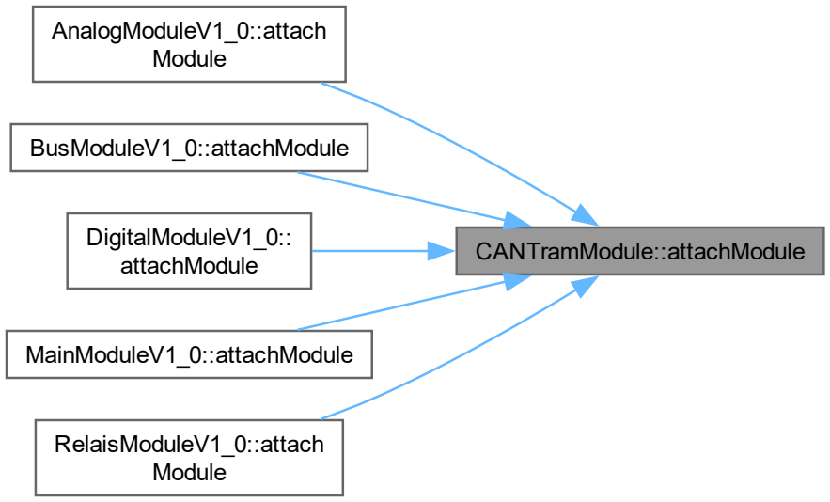
[picture p50: figure]
CANTramModule::attachModule; AnalogModuleV1_0::attach Module; BusModuleV1_0::attachModule; DigitalModuleV1_0:: attachModule; MainModuleV1_0::attachModule; RelaisModuleV1_0::attach Module
