LeoWatti99/CANTram-Framework/Doxygen/latex/d2/dee/class_c_a_n_tram_module_a7905817e8fee9e8bccfc9bbe70ae5669_icgraph.pdf

CANTramCore::attachModule | CANTramCore::attachModule | CANTramModule::getGPIOStart
