LeoWatti99/CANTram-Framework/Doxygen/latex/d2/dee/class_c_a_n_tram_module_a7f2c1c05cafb19676aed58c11219d0f5_icgraph.pdf

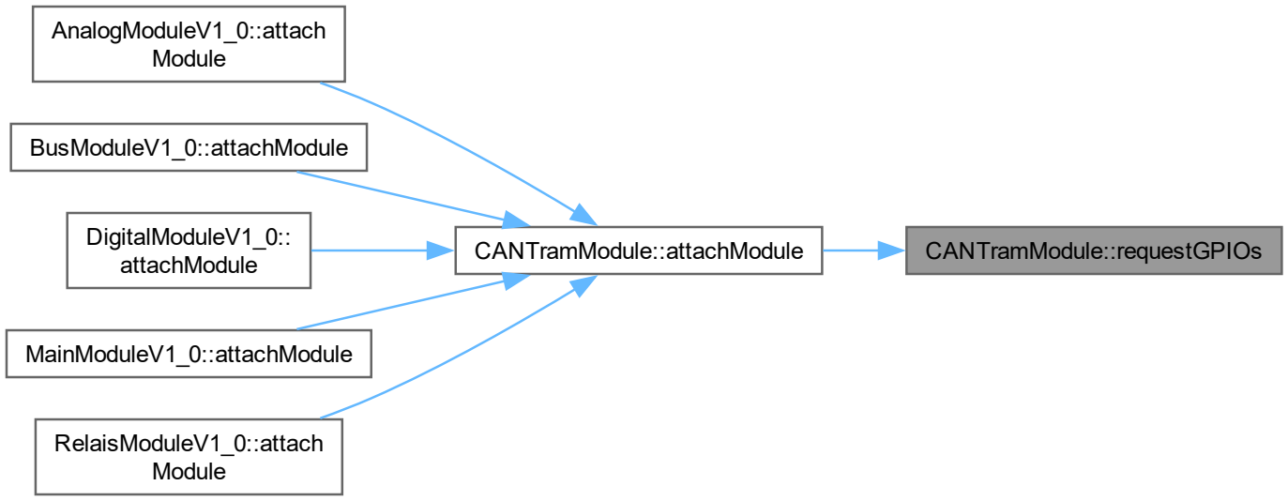
[picture p51: figure]
CANTramModule::attachModule; CANTramModule::requestGPIOs; AnalogModuleV1_0::attach Module; BusModuleV1_0::attachModule; DigitalModuleV1_0:: attachModule; MainModuleV1_0::attachModule; RelaisModuleV1_0::attach Module
