LeoWatti99/CANTram-Framework/Doxygen/latex/d2/dee/class_c_a_n_tram_module_a80b400128bb6f0841953bb7a75cbf99c_icgraph.pdf

CANTramCore::attachModule | CANTramCore::attachModule | CANTramModule::getSlot
