LeoWatti99/CANTram-Framework/Doxygen/latex/d2/dee/class_c_a_n_tram_module_a88dd0ab2213df828b576d337e38c1ac8_icgraph.pdf

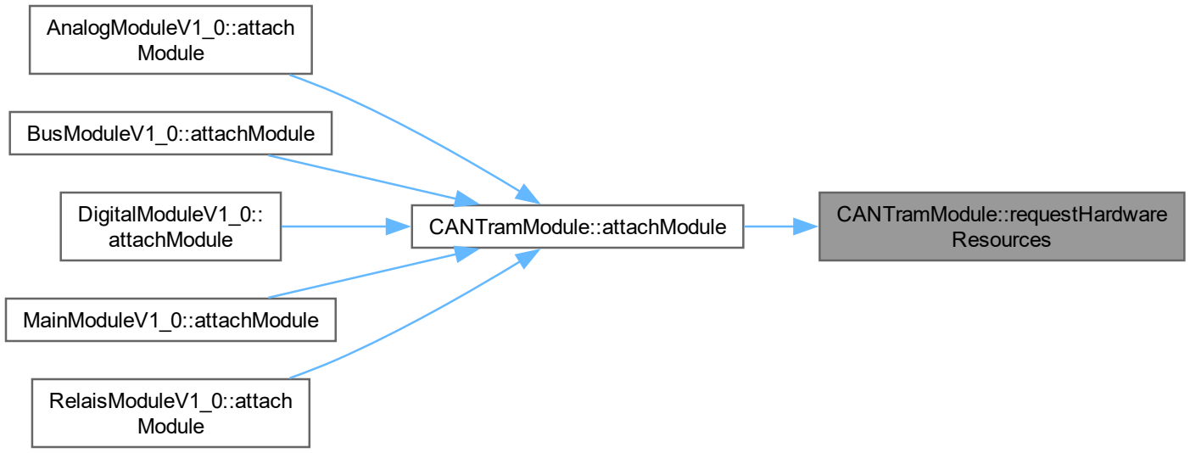
[picture p52: figure]
CANTramModule::requestHardware Resources CANTramModule::attachModule; AnalogModuleV1_0::attach Module; BusModuleV1_0::attachModule; DigitalModuleV1_0:: attachModule; MainModuleV1_0::attachModule; RelaisModuleV1_0::attach Module
