LeoWatti99/CANTram-Framework/Doxygen/latex/d2/dee/class_c_a_n_tram_module_abaad4d92c02fc8bb525a57d8ac06db7e_icgraph.pdf

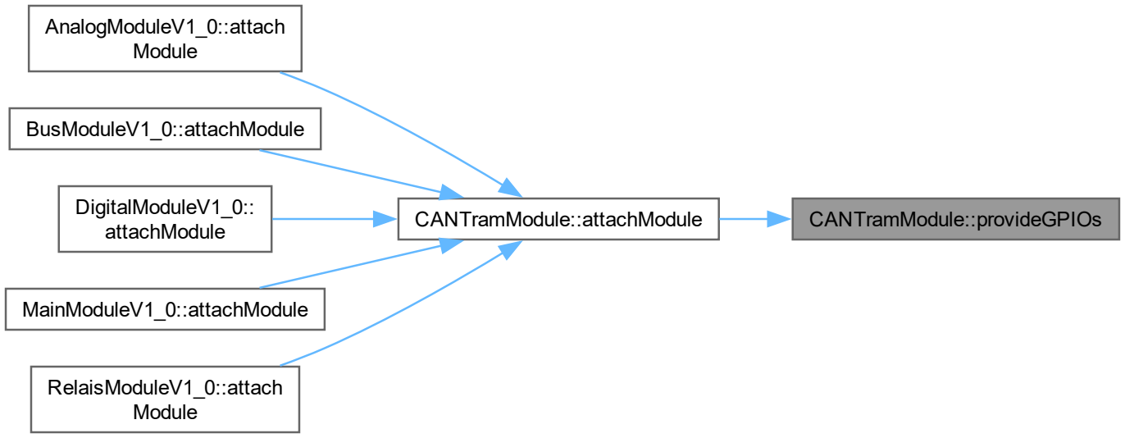
[picture p53: figure]
CANTramModule::attachModule; CANTramModule::provideGPIOs; AnalogModuleV1_0::attach Module; BusModuleV1_0::attachModule; DigitalModuleV1_0:: attachModule; MainModuleV1_0::attachModule; RelaisModuleV1_0::attach Module
