LeoWatti99/CANTram-Framework/Doxygen/latex/d3/d50/class_e_s_p32_p_w_m_core__inherit__graph.pdf

ESP32PWMCore

PWMCore

HardwareResource
