LeoWatti99/CANTram-Framework/Doxygen/latex/d3/d55/class_e_s_p32___c_a_n_core__inherit__graph.pdf

ESP32_CANCore

CANCore

HardwareResource
