LeoWatti99/CANTram-Framework/Doxygen/latex/d3/d5a/_u_a_r_t_core_8h__dep__incl.pdf

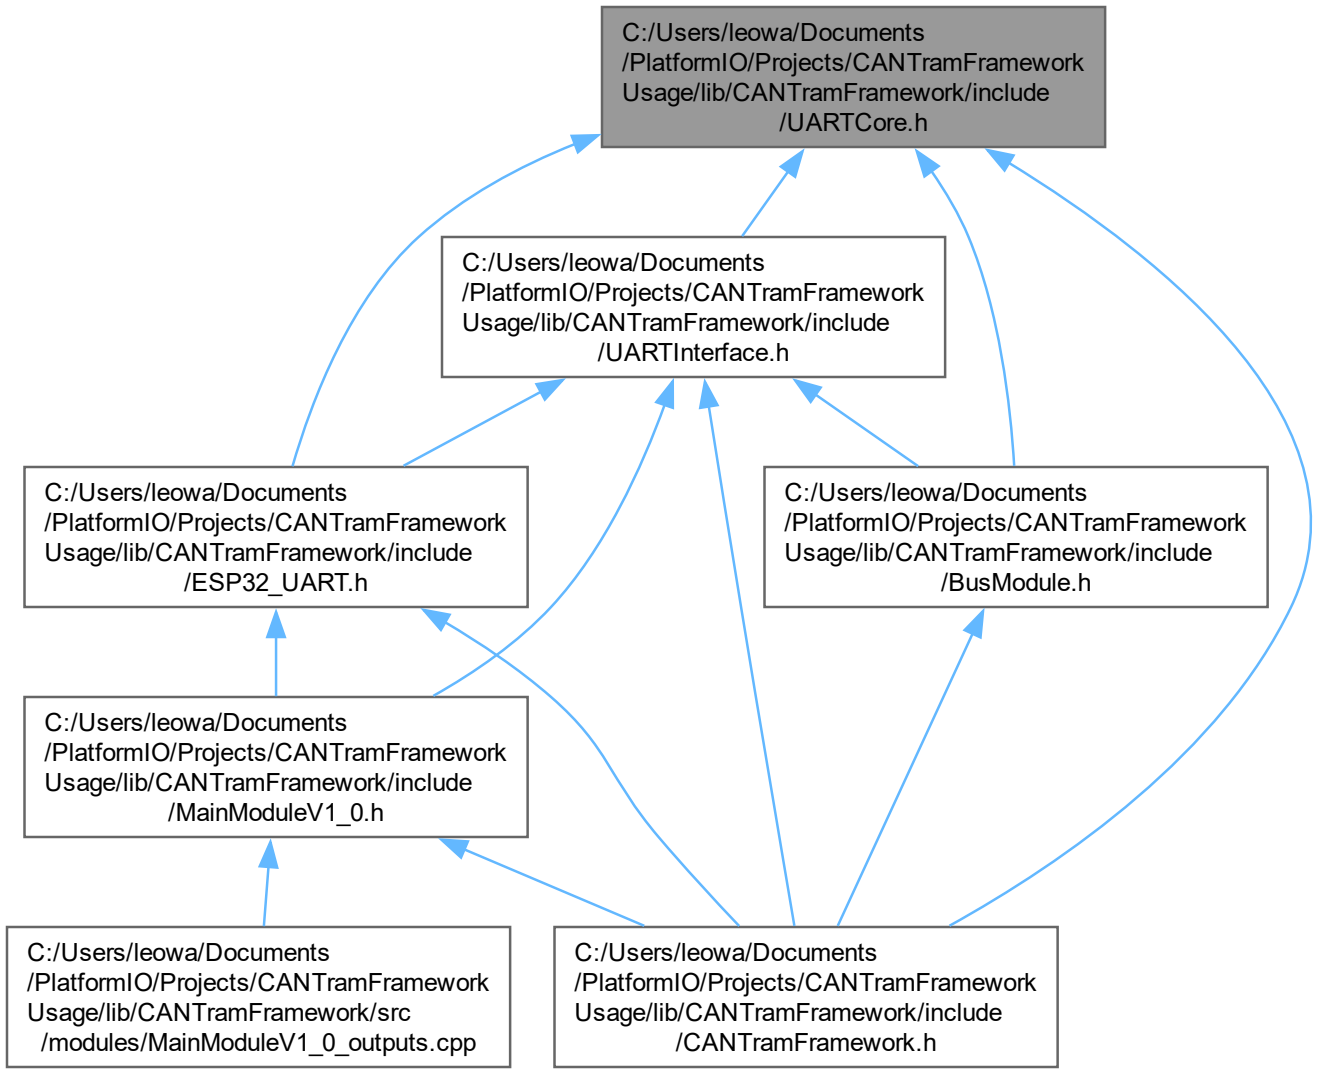
[picture p54: figure]
C:/Users/leowa/Documents /PlatformIO/Projects/CANTramFramework Usage/lib/CANTramFramework/include /UARTCore.h; C:/Users/leowa/Documents /PlatformIO/Projects/CANTramFramework Usage/lib/CANTramFramework/include /BusModule.h; C:/Users/leowa/Documents /PlatformIO/Projects/CANTramFramework Usage/lib/CANTramFramework/include /CANTramFramework.h; C:/Users/leowa/Documents /PlatformIO/Projects/CANTramFramework Usage/lib/CANTramFramework/include /ESP32_UART.h; C:/Users/leowa/Documents /PlatformIO/Projects/CANTramFramework Usage/lib/CANTramFramework/include /UARTInterface.h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
