LeoWatti99/CANTram-Framework/Doxygen/latex/d3/dba/_c_a_n_tram_module_8h__incl.pdf

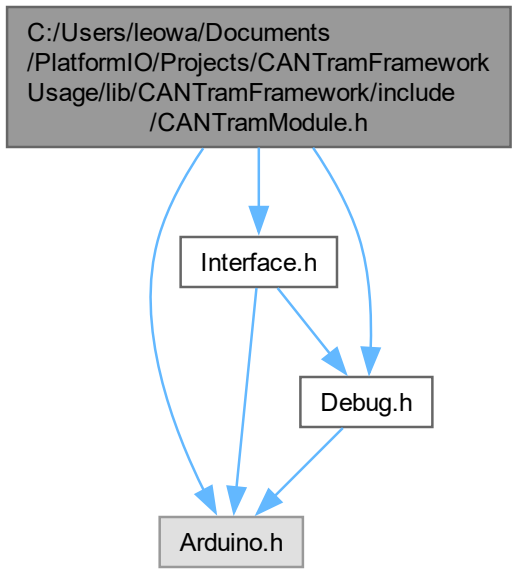
[picture p55: figure]
C:/Users/leowa/Documents /PlatformIO/Projects/CANTramFramework Usage/lib/CANTramFramework/include /CANTramModule.h; Arduino.h; Interface.h; Debug.h
