LeoWatti99/CANTram-Framework/Doxygen/latex/d4/d06/class_analog_module_v1__0_ac7d18b81c9980020734c35b7987219b6_cgraph.pdf

AnalogModuleV1_0::request
HardwareResources

PWMOutputProvider::
registerPWMChannel
