LeoWatti99/CANTram-Framework/Doxygen/latex/d4/d06/class_analog_module_v1__0_adf25f90bf6a38cfe20c6ac8984cf36fa_cgraph.pdf

AnalogModuleV1_0::cycle | PWMOutputProvider:: setPWM
