LeoWatti99/CANTram-Framework/Doxygen/latex/d4/d55/class_e_s_p32_p_w_m_core__coll__graph.pdf

ESP32PWMCore

PWMCore

HardwareResource
