LeoWatti99/CANTram-Framework/Doxygen/latex/d4/da9/class_u_a_r_t_core_aeaf04f4297b48fdaee839a2ff9fb4ad4_cgraph.pdf

UARTCore::reset | HardwareResource::reset | HardwareResource::getType
