LeoWatti99/CANTram-Framework/Doxygen/latex/d4/ddb/class_digital_module_v1__0_a6b52d3ca7181a224b478d93766a7bfe7_cgraph.pdf

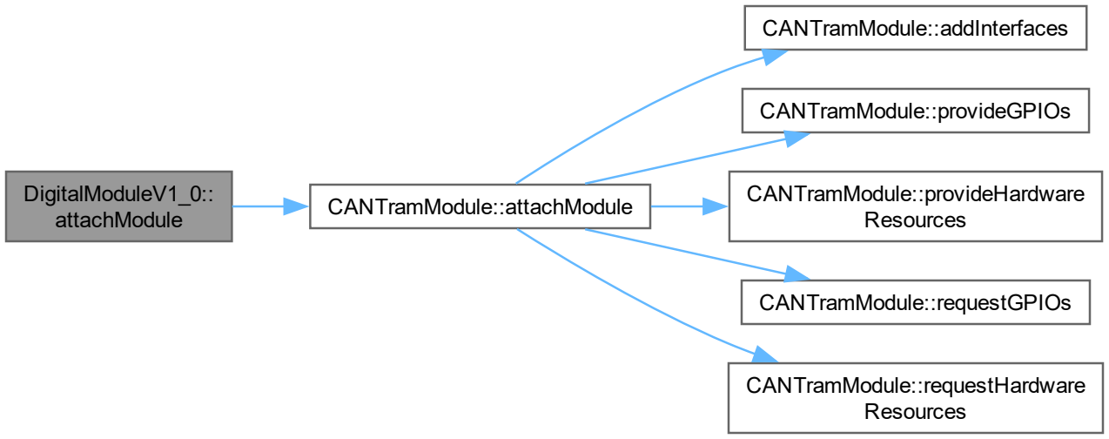
[picture p56: figure]
DigitalModuleV1_0::; attachModule; CANTramModule::attachModule; CANTramModule::addInterfaces; CANTramModule::provideGPIOs; CANTramModule::provideHardware Resources; CANTramModule::requestGPIOs; CANTramModule::requestHardware Resources
