LeoWatti99/CANTram-Framework/Doxygen/latex/d6/d0e/_output_definition_8h__incl.pdf

C:/Users/leowa/Documents
/PlatformIO/Projects/CANTramFramework Usage/lib/CANTramFramework/include /OutputDefinition.h

Arduino.h

Debug.h
