LeoWatti99/CANTram-Framework/Doxygen/latex/d6/d1c/_m_a_x22531_8h__incl.pdf

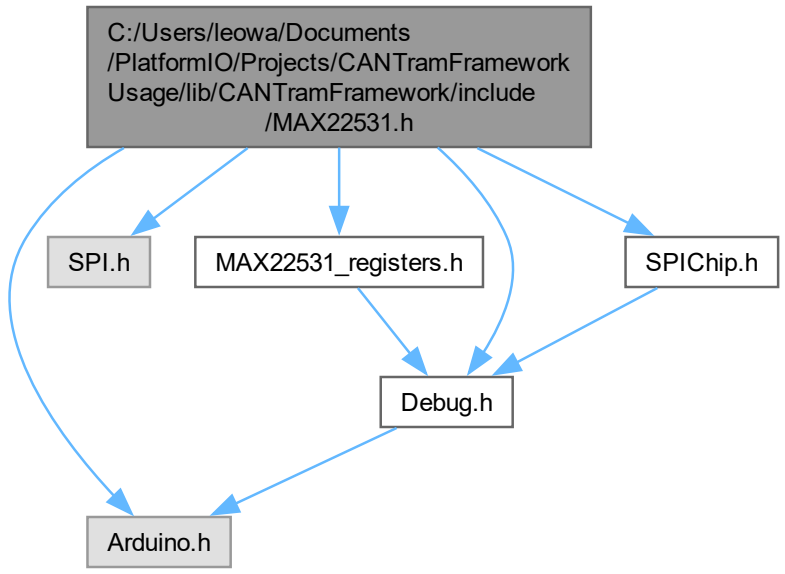
[picture p57: figure]
C:/Users/leowa/Documents /PlatformIO/Projects/CANTramFramework Usage/lib/CANTramFramework/include /MAX22531.h; Arduino.h; SPI.h; MAX22531_registers.h; Debug.h; SPIChip.h
