LeoWatti99/CANTram-Framework/Doxygen/latex/d6/d24/class_e_s_p32___c_a_n_core_a82b0d9ba535b47648ac951338794509e_icgraph.pdf

ESP32_CANCore::readMessage | ESP32_CANCore::available
