LeoWatti99/CANTram-Framework/Doxygen/latex/d6/d24/class_e_s_p32___c_a_n_core_a85a0e3c4965503c96d865bbcc200cd2a_cgraph.pdf

ESP32_CANCore::reset | CANCore::reset | HardwareResource::reset | HardwareResource::getType
