LeoWatti99/CANTram-Framework/Doxygen/latex/d6/d24/class_e_s_p32___c_a_n_core_adbab7ae89e53ad752bc06e789381c4d5_cgraph.pdf

ESP32_CANCore::readMessage | ESP32_CANCore::available
