LeoWatti99/CANTram-Framework/Doxygen/latex/d0/de8/class_relais_interface.tex

\doxysection{Relais\+Interface Class Reference}
\hypertarget{class_relais_interface}{}\label{class_relais_interface}\index{RelaisInterface@{RelaisInterface}}

Inheritance diagram for Relais\+Interface\+:
\nopagebreak
\begin{figure}[H]
\begin{center}
\leavevmode

\end{center}
\end{figure}

Collaboration diagram for Relais\+Interface\+:
\nopagebreak
\begin{figure}[H]
\begin{center}
\leavevmode

\end{center}
\end{figure}
\doxysubsubsection*{Public Member Functions}
\begin{DoxyCompactItemize}
\item 
Interface\+::\+Type \mbox{\hyperlink{class_relais_interface_a280068104c515b47b0fc9b35f725e2f2}{get\+Type}} () const override
\end{DoxyCompactItemize}
\doxysubsection*{Public Member Functions inherited from \mbox{\hyperlink{class_interface}{Interface}}}
\begin{DoxyCompactItemize}
\item 
virtual void \mbox{\hyperlink{class_interface_a3ac5ff9b58ddb3323ad28d470850b41e}{setQ}} (uint16\+\_\+t q)
\item 
virtual uint16\+\_\+t {\bfseries getQ} () const
\item 
void {\bfseries rename} (const String \&new\+Name)
\item 
{\footnotesize template$<$typename T$>$ }\\T {\bfseries as} ()
\item 
void {\bfseries validate} ()
\item 
void {\bfseries validate} (bool state)
\item 
void {\bfseries invalidate} ()
\item 
bool {\bfseries is\+Valid} ()
\item 
bool {\bfseries is\+Invalid} ()
\item 
String {\bfseries get\+Name} () const
\end{DoxyCompactItemize}
\doxysubsubsection*{Additional Inherited Members}
\doxysubsection*{Public Types inherited from \mbox{\hyperlink{class_interface}{Interface}}}
\begin{DoxyCompactItemize}
\item 
\Hypertarget{class_interface_a765c7b30069d200e461995c602b98e90}\label{class_interface_a765c7b30069d200e461995c602b98e90} 
enum {\bfseries Resolution} \{ {\bfseries RES\+\_\+8\+BIT} = 8
, {\bfseries RES\+\_\+10\+BIT} = 10
, {\bfseries RES\+\_\+12\+BIT} = 12
, {\bfseries RES\+\_\+16\+BIT} = 16
 \}
\item 
\Hypertarget{class_interface_a01562cbfcb9c8793a7117b67ee0ce079}\label{class_interface_a01562cbfcb9c8793a7117b67ee0ce079} 
enum {\bfseries Type} \{ \newline
{\bfseries DIGITAL\+\_\+\+INPUT}
, {\bfseries DIGITAL\+\_\+\+OUTPUT}
, {\bfseries ANALOG\+\_\+\+INPUT}
, {\bfseries ANALOG\+\_\+\+OUTPUT}
, \newline
{\bfseries RELAIS}
, {\bfseries BUS}
 \}
\end{DoxyCompactItemize}
\doxysubsection*{Protected Attributes inherited from \mbox{\hyperlink{class_interface}{Interface}}}
\begin{DoxyCompactItemize}
\item 
String {\bfseries name}
\item 
uint16\+\_\+t {\bfseries Q} = 0
\item 
bool {\bfseries \+\_\+valid} = false
\item 
bool {\bfseries \+\_\+invalid} = false
\end{DoxyCompactItemize}

\label{doc-func-members}
\Hypertarget{class_relais_interface_doc-func-members}
\doxysubsection{Member Function Documentation}
\Hypertarget{class_relais_interface_a280068104c515b47b0fc9b35f725e2f2}\index{RelaisInterface@{RelaisInterface}!getType@{getType}}
\index{getType@{getType}!RelaisInterface@{RelaisInterface}}
\doxysubsubsection{\texorpdfstring{getType()}{getType()}}
{\footnotesize\ttfamily \label{class_relais_interface_a280068104c515b47b0fc9b35f725e2f2} 
Interface\+::\+Type Relais\+Interface\+::get\+Type (\begin{DoxyParamCaption}{}{}\end{DoxyParamCaption}) const\hspace{0.3cm}{\ttfamily [inline]}, {\ttfamily [override]}, {\ttfamily [virtual]}}

Implements \mbox{\hyperlink{class_interface}{Interface}}.

The documentation for this class was generated from the following file\+:\begin{DoxyCompactItemize}
\item 
C\+:/\+Users/leowa/\+Documents/\+Platform\+IO/\+Projects/\+CANTram\+Framework\+Usage/lib/\+CANTram\+Framework/include/Relais\+Interface.\+h\end{DoxyCompactItemize}
