LeoWatti99/CANTram-Framework/Doxygen/latex/d2/dee/class_c_a_n_tram_module.tex

\doxysection{CANTram\+Module Class Reference}
\hypertarget{class_c_a_n_tram_module}{}\label{class_c_a_n_tram_module}\index{CANTramModule@{CANTramModule}}

Inheritance diagram for CANTram\+Module\+:
\nopagebreak
\begin{figure}[H]
\begin{center}
\leavevmode

\end{center}
\end{figure}
\doxysubsubsection*{Public Member Functions}
\begin{DoxyCompactItemize}
\item 
\mbox{\hyperlink{class_c_a_n_tram_module_ae1c9554adb901b7e798a44d521781c0b}{CANTram\+Module}} ()=default
\begin{DoxyCompactList}\small\item\em Default constructor. \end{DoxyCompactList}\item 
virtual \mbox{\hyperlink{class_c_a_n_tram_module_a8f93d67f0d5b49b7864369196cb323e6}{\texorpdfstring{$\sim$}{\string~}\+CANTram\+Module}} ()=default
\begin{DoxyCompactList}\small\item\em Destructor. \end{DoxyCompactList}\item 
virtual String \mbox{\hyperlink{class_c_a_n_tram_module_a3edca0142c5fa8a0d91a549f8371b460}{get\+HWType}} () const =0
\begin{DoxyCompactList}\small\item\em Get the hardware type string. \end{DoxyCompactList}\item 
virtual String \mbox{\hyperlink{class_c_a_n_tram_module_a5d9287df902bd2f9ec32b4317f95fff6}{get\+HWVersion}} () const =0
\begin{DoxyCompactList}\small\item\em Get the hardware version string. \end{DoxyCompactList}\item 
virtual String \mbox{\hyperlink{class_c_a_n_tram_module_acf8e6722dc924b1bf4d5289f3684fd29}{get\+FWVersion}} () const =0
\begin{DoxyCompactList}\small\item\em Get the firmware version string. \end{DoxyCompactList}\item 
virtual uint8\+\_\+t \mbox{\hyperlink{class_c_a_n_tram_module_afa6df5b58f7681a8a316b3910f987cce}{get\+GPIODemand}} () const =0
\begin{DoxyCompactList}\small\item\em Get the GPIO demand of the module. \end{DoxyCompactList}\item 
virtual uint8\+\_\+t \mbox{\hyperlink{class_c_a_n_tram_module_ae7247503120b76151cc2086dc4250911}{get\+GPIOSupply}} () const =0
\begin{DoxyCompactList}\small\item\em Get the GPIO supply capacity of the module. \end{DoxyCompactList}\item 
virtual bool \mbox{\hyperlink{class_c_a_n_tram_module_a496814b4e5fa5f162c48f17ec33d4475}{reset}} ()
\begin{DoxyCompactList}\small\item\em Reset the module to a known default state. \end{DoxyCompactList}\item 
uint8\+\_\+t \mbox{\hyperlink{class_c_a_n_tram_module_a80b400128bb6f0841953bb7a75cbf99c}{get\+Slot}} () const
\begin{DoxyCompactList}\small\item\em Get assigned slot index. \end{DoxyCompactList}\item 
uint8\+\_\+t \mbox{\hyperlink{class_c_a_n_tram_module_a7905817e8fee9e8bccfc9bbe70ae5669}{get\+GPIOStart}} () const
\begin{DoxyCompactList}\small\item\em Get starting GPIO index assigned to the module. \end{DoxyCompactList}\item 
virtual void \mbox{\hyperlink{class_c_a_n_tram_module_a1be4a73e5fc8e14edad90741593d2d29}{cycle}} (uint8\+\_\+t \texorpdfstring{$\ast$}{*}response)
\begin{DoxyCompactList}\small\item\em Periodic cycle callback. \end{DoxyCompactList}\item 
virtual bool \mbox{\hyperlink{class_c_a_n_tram_module_a67cab1c238257e6d9b88afc4f644e477}{attach\+Module}} (uint8\+\_\+t slot, uint8\+\_\+t gpio\+Start)
\begin{DoxyCompactList}\small\item\em Attach this module to a slot and assign GPIO range. \end{DoxyCompactList}\item 
virtual bool \mbox{\hyperlink{class_c_a_n_tram_module_abaad4d92c02fc8bb525a57d8ac06db7e}{provide\+GPIOs}} ()=0
\begin{DoxyCompactList}\small\item\em Provide GPIO definitions to the core. \end{DoxyCompactList}\item 
virtual bool \mbox{\hyperlink{class_c_a_n_tram_module_a7f2c1c05cafb19676aed58c11219d0f5}{request\+GPIOs}} ()=0
\begin{DoxyCompactList}\small\item\em Request GPIO definitions from the core. \end{DoxyCompactList}\item 
virtual bool \mbox{\hyperlink{class_c_a_n_tram_module_aa509ae950722ebd48383c124ec6a63ec}{provide\+Hardware\+Resources}} ()=0
\begin{DoxyCompactList}\small\item\em Provide hardware resources (e.\+g., I2C, SPI, UART) to the core. \end{DoxyCompactList}\item 
virtual bool \mbox{\hyperlink{class_c_a_n_tram_module_a88dd0ab2213df828b576d337e38c1ac8}{request\+Hardware\+Resources}} ()=0
\begin{DoxyCompactList}\small\item\em Request hardware resources from the core. \end{DoxyCompactList}\item 
virtual bool \mbox{\hyperlink{class_c_a_n_tram_module_a14b79b625e82a3f11ebbb8271b6466b7}{add\+Interfaces}} ()=0
\begin{DoxyCompactList}\small\item\em Setup and validate module interfaces. \end{DoxyCompactList}\item 
virtual bool \mbox{\hyperlink{class_c_a_n_tram_module_a329b502ade3a32987994381c93ddbd0b}{pre\+Initialize}} ()
\begin{DoxyCompactList}\small\item\em Pre-\/initialize the module after attachment and provisioning. \end{DoxyCompactList}\item 
virtual bool \mbox{\hyperlink{class_c_a_n_tram_module_a6930dfb86a2e06ab9a9b299520830fb7}{initialize}} ()=0
\begin{DoxyCompactList}\small\item\em Initialize the module after attachment and provisioning. \end{DoxyCompactList}\item 
virtual \mbox{\hyperlink{class_interface}{Interface}} \texorpdfstring{$\ast$}{*}\texorpdfstring{$\ast$}{*} \mbox{\hyperlink{class_c_a_n_tram_module_a09c919fc31111badfec18faf64c729f4}{get\+Interfaces}} ()=0
\begin{DoxyCompactList}\small\item\em Get pointer to module\textquotesingle{}s interface array. \end{DoxyCompactList}\item 
virtual size\+\_\+t \mbox{\hyperlink{class_c_a_n_tram_module_a68c703147d8b495e324febcaccd49dea}{get\+Interface\+Count}} ()=0
\begin{DoxyCompactList}\small\item\em Get number of interfaces provided by the module. \end{DoxyCompactList}\end{DoxyCompactItemize}
\doxysubsubsection*{Protected Attributes}
\begin{DoxyCompactItemize}
\item 
\Hypertarget{class_c_a_n_tram_module_a71a85530bed12d5978e5b74e3c632ab7}\label{class_c_a_n_tram_module_a71a85530bed12d5978e5b74e3c632ab7} 
uint8\+\_\+t {\bfseries SLOT} = 0
\item 
\Hypertarget{class_c_a_n_tram_module_ae005164dd472f88c7f8c82b5e409cd06}\label{class_c_a_n_tram_module_ae005164dd472f88c7f8c82b5e409cd06} 
uint8\+\_\+t {\bfseries GPIO\+\_\+\+START} = 0
\end{DoxyCompactItemize}

\label{doc-constructors}
\Hypertarget{class_c_a_n_tram_module_doc-constructors}
\doxysubsection{Constructor \& Destructor Documentation}
\Hypertarget{class_c_a_n_tram_module_ae1c9554adb901b7e798a44d521781c0b}\index{CANTramModule@{CANTramModule}!CANTramModule@{CANTramModule}}
\index{CANTramModule@{CANTramModule}!CANTramModule@{CANTramModule}}
\doxysubsubsection{\texorpdfstring{CANTramModule()}{CANTramModule()}}
{\footnotesize\ttfamily \label{class_c_a_n_tram_module_ae1c9554adb901b7e798a44d521781c0b} 
CANTram\+Module\+::\+CANTram\+Module (\begin{DoxyParamCaption}{}{}\end{DoxyParamCaption})\hspace{0.3cm}{\ttfamily [default]}}

Default constructor. 

Constructs an empty \doxylink{class_c_a_n_tram_module}{CANTram\+Module} instance. Derived classes should perform initialization in \doxylink{class_c_a_n_tram_module_a67cab1c238257e6d9b88afc4f644e477}{attach\+Module()}/initialize(). \Hypertarget{class_c_a_n_tram_module_a8f93d67f0d5b49b7864369196cb323e6}\index{CANTramModule@{CANTramModule}!````~CANTramModule@{\texorpdfstring{$\sim$}{\string~}CANTramModule}}
\index{````~CANTramModule@{\texorpdfstring{$\sim$}{\string~}CANTramModule}!CANTramModule@{CANTramModule}}
\doxysubsubsection{\texorpdfstring{\texorpdfstring{$\sim$}{\string~}CANTramModule()}{\string~CANTramModule()}}
{\footnotesize\ttfamily \label{class_c_a_n_tram_module_a8f93d67f0d5b49b7864369196cb323e6} 
virtual CANTram\+Module\+::\texorpdfstring{$\sim$}{\string~}\+CANTram\+Module (\begin{DoxyParamCaption}{}{}\end{DoxyParamCaption})\hspace{0.3cm}{\ttfamily [virtual]}, {\ttfamily [default]}}

Destructor. 

Virtual destructor to ensure proper cleanup in derived classes. 

\label{doc-func-members}
\Hypertarget{class_c_a_n_tram_module_doc-func-members}
\doxysubsection{Member Function Documentation}
\Hypertarget{class_c_a_n_tram_module_a14b79b625e82a3f11ebbb8271b6466b7}\index{CANTramModule@{CANTramModule}!addInterfaces@{addInterfaces}}
\index{addInterfaces@{addInterfaces}!CANTramModule@{CANTramModule}}
\doxysubsubsection{\texorpdfstring{addInterfaces()}{addInterfaces()}}
{\footnotesize\ttfamily \label{class_c_a_n_tram_module_a14b79b625e82a3f11ebbb8271b6466b7} 
virtual bool CANTram\+Module\+::add\+Interfaces (\begin{DoxyParamCaption}{}{}\end{DoxyParamCaption})\hspace{0.3cm}{\ttfamily [pure virtual]}}

Setup and validate module interfaces. 

Populate the module\textquotesingle{}s Interface\texorpdfstring{$\ast$}{*} array, name interfaces and validate them as needed. \begin{DoxyReturn}{Returns}
true if interfaces were successfully added and validated, false otherwise. 
\end{DoxyReturn}

Implemented in \mbox{\hyperlink{class_analog_module_v1__0_ae288aa8255de5ca8b8a08ef1c18b44b2}{Analog\+Module\+V1\+\_\+0}}, \mbox{\hyperlink{class_bus_module_v1__0_ad4d8d6745e0f039f1aaf1f4adf0f4416}{Bus\+Module\+V1\+\_\+0}}, \mbox{\hyperlink{class_digital_module_v1__0_a4748ca50960d9b54c52b18a00a35dc55}{Digital\+Module\+V1\+\_\+0}}, \mbox{\hyperlink{class_main_module_v1__0_a7d462f2505c3a1f632db53f4e69bd6ee}{Main\+Module\+V1\+\_\+0}}, and \mbox{\hyperlink{class_relais_module_v1__0_ace1bb24ccb82505ab38059203b179f1a}{Relais\+Module\+V1\+\_\+0}}.

Here is the caller graph for this function\+:
\nopagebreak
\begin{figure}[H]
\begin{center}
\leavevmode
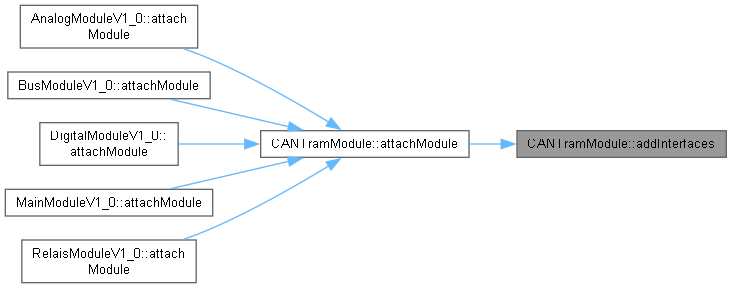
[picture p58: Doxygen/html/d2/dee/class_c_a_n_tram_module_a14b79b625e82a3f11ebbb8271b6466b7_icgraph.png]

\end{center}
\end{figure}
\Hypertarget{class_c_a_n_tram_module_a67cab1c238257e6d9b88afc4f644e477}\index{CANTramModule@{CANTramModule}!attachModule@{attachModule}}
\index{attachModule@{attachModule}!CANTramModule@{CANTramModule}}
\doxysubsubsection{\texorpdfstring{attachModule()}{attachModule()}}
{\footnotesize\ttfamily \label{class_c_a_n_tram_module_a67cab1c238257e6d9b88afc4f644e477} 
bool CANTram\+Module\+::attach\+Module (\begin{DoxyParamCaption}\item[{uint8\+\_\+t}]{slot}{, }\item[{uint8\+\_\+t}]{gpio\+Start}{}\end{DoxyParamCaption})\hspace{0.3cm}{\ttfamily [virtual]}}

Attach this module to a slot and assign GPIO range. 

Attach this module to a slot and assign its GPIO range.

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

Reimplemented in \mbox{\hyperlink{class_analog_module_v1__0_a0d48d770904f90501dfa2bef16270d8c}{Analog\+Module\+V1\+\_\+0}}, \mbox{\hyperlink{class_bus_module_v1__0_a16bba6acd40262044fbb2dfa89967a37}{Bus\+Module\+V1\+\_\+0}}, \mbox{\hyperlink{class_digital_module_v1__0_a6b52d3ca7181a224b478d93766a7bfe7}{Digital\+Module\+V1\+\_\+0}}, \mbox{\hyperlink{class_main_module_v1__0_a54175254ab9745989cc21d00f490297a}{Main\+Module\+V1\+\_\+0}}, and \mbox{\hyperlink{class_relais_module_v1__0_a1a7004ca779f46212dde0bd70c0a8bca}{Relais\+Module\+V1\+\_\+0}}.

Here is the call graph for this function\+:
\nopagebreak
\begin{figure}[H]
\begin{center}
\leavevmode
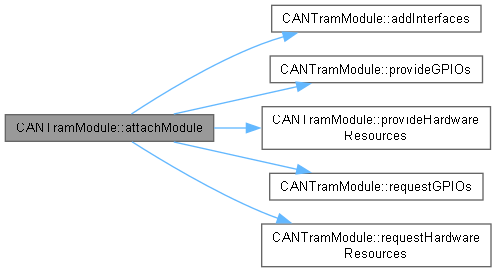
[picture p59: Doxygen/html/d2/dee/class_c_a_n_tram_module_a67cab1c238257e6d9b88afc4f644e477_cgraph.png]

\end{center}
\end{figure}
Here is the caller graph for this function\+:
\nopagebreak
\begin{figure}[H]
\begin{center}
\leavevmode
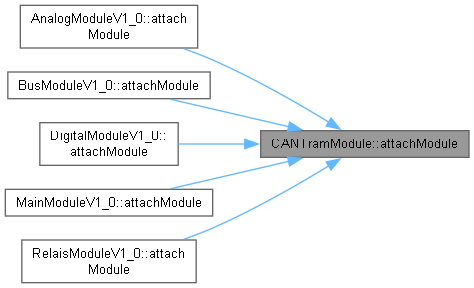
[picture p60: Doxygen/html/d2/dee/class_c_a_n_tram_module_a67cab1c238257e6d9b88afc4f644e477_icgraph.png]

\end{center}
\end{figure}
\Hypertarget{class_c_a_n_tram_module_a1be4a73e5fc8e14edad90741593d2d29}\index{CANTramModule@{CANTramModule}!cycle@{cycle}}
\index{cycle@{cycle}!CANTramModule@{CANTramModule}}
\doxysubsubsection{\texorpdfstring{cycle()}{cycle()}}
{\footnotesize\ttfamily \label{class_c_a_n_tram_module_a1be4a73e5fc8e14edad90741593d2d29} 
virtual void CANTram\+Module\+::cycle (\begin{DoxyParamCaption}\item[{uint8\+\_\+t \texorpdfstring{$\ast$}{*}}]{response}{}\end{DoxyParamCaption})\hspace{0.3cm}{\ttfamily [inline]}, {\ttfamily [virtual]}}

Periodic cycle callback. 

Called regularly by the core to allow the module to perform time-\/based tasks. 
\begin{DoxyParams}{Parameters}
{\em response} & Optional pointer to a response buffer where the module may write response bytes. May be nullptr. \\
\hline
\end{DoxyParams}

Reimplemented in \mbox{\hyperlink{class_analog_module_v1__0_adf25f90bf6a38cfe20c6ac8984cf36fa}{Analog\+Module\+V1\+\_\+0}}, \mbox{\hyperlink{class_bus_module_v1__0_a25a59d36f49cd5316a0186bd02b1a588}{Bus\+Module\+V1\+\_\+0}}, \mbox{\hyperlink{class_digital_module_v1__0_a75ccf259962e3e9414b0bfc92b77c9c7}{Digital\+Module\+V1\+\_\+0}}, \mbox{\hyperlink{class_main_module_v1__0_a37be53a3ecbf9864791b17facd5f2169}{Main\+Module\+V1\+\_\+0}}, and \mbox{\hyperlink{class_relais_module_v1__0_a6036020b6f6dd6cbb9ab1c6428fa719b}{Relais\+Module\+V1\+\_\+0}}.

Here is the call graph for this function\+:
\nopagebreak
\begin{figure}[H]
\begin{center}
\leavevmode

\end{center}
\end{figure}
Here is the caller graph for this function\+:
\nopagebreak
\begin{figure}[H]
\begin{center}
\leavevmode

\end{center}
\end{figure}
\Hypertarget{class_c_a_n_tram_module_acf8e6722dc924b1bf4d5289f3684fd29}\index{CANTramModule@{CANTramModule}!getFWVersion@{getFWVersion}}
\index{getFWVersion@{getFWVersion}!CANTramModule@{CANTramModule}}
\doxysubsubsection{\texorpdfstring{getFWVersion()}{getFWVersion()}}
{\footnotesize\ttfamily \label{class_c_a_n_tram_module_acf8e6722dc924b1bf4d5289f3684fd29} 
virtual String CANTram\+Module\+::get\+FWVersion (\begin{DoxyParamCaption}{}{}\end{DoxyParamCaption}) const\hspace{0.3cm}{\ttfamily [pure virtual]}}

Get the firmware version string. 

Returns the firmware version string implemented by the module. \begin{DoxyReturn}{Returns}
String Firmware version (e.\+g. "{}1.\+0"{}). 
\end{DoxyReturn}

Implemented in \mbox{\hyperlink{class_analog_module_v1__0_aa4c1e1889578720bc95599c563397114}{Analog\+Module\+V1\+\_\+0}}, \mbox{\hyperlink{class_bus_module_v1__0_abb12c39782672f8904b8cc7f5a8c7364}{Bus\+Module\+V1\+\_\+0}}, \mbox{\hyperlink{class_digital_module_v1__0_a8ecee0734562f0601963b0d4365f4ef8}{Digital\+Module\+V1\+\_\+0}}, \mbox{\hyperlink{class_main_module_v1__0_a87ce54b0fb2bbd67622e48024dc17b9e}{Main\+Module\+V1\+\_\+0}}, and \mbox{\hyperlink{class_relais_module_v1__0_a5b51d4cb5afd3981a560c4084c8a8933}{Relais\+Module\+V1\+\_\+0}}.

\Hypertarget{class_c_a_n_tram_module_afa6df5b58f7681a8a316b3910f987cce}\index{CANTramModule@{CANTramModule}!getGPIODemand@{getGPIODemand}}
\index{getGPIODemand@{getGPIODemand}!CANTramModule@{CANTramModule}}
\doxysubsubsection{\texorpdfstring{getGPIODemand()}{getGPIODemand()}}
{\footnotesize\ttfamily \label{class_c_a_n_tram_module_afa6df5b58f7681a8a316b3910f987cce} 
virtual uint8\+\_\+t CANTram\+Module\+::get\+GPIODemand (\begin{DoxyParamCaption}{}{}\end{DoxyParamCaption}) const\hspace{0.3cm}{\ttfamily [pure virtual]}}

Get the GPIO demand of the module. 

Returns how many GPIOs this module requires from the core. \begin{DoxyReturn}{Returns}
uint8\+\_\+t Number of GPIOs demanded by the module. 
\end{DoxyReturn}

Implemented in \mbox{\hyperlink{class_analog_module_v1__0_ab34d1eaa309b1b2e37851d66287f43d6}{Analog\+Module\+V1\+\_\+0}}, \mbox{\hyperlink{class_bus_module_v1__0_ab1f6be81ebb01684222a2fbfdc19cba1}{Bus\+Module\+V1\+\_\+0}}, \mbox{\hyperlink{class_digital_module_v1__0_a0e1364361441d3180ed65e22b08ba695}{Digital\+Module\+V1\+\_\+0}}, \mbox{\hyperlink{class_main_module_v1__0_a501133cf4a307fc25acaf0b6f79dcebc}{Main\+Module\+V1\+\_\+0}}, and \mbox{\hyperlink{class_relais_module_v1__0_a078c91e0b5bc3f21a22bc71388ea1b0d}{Relais\+Module\+V1\+\_\+0}}.

\Hypertarget{class_c_a_n_tram_module_a7905817e8fee9e8bccfc9bbe70ae5669}\index{CANTramModule@{CANTramModule}!getGPIOStart@{getGPIOStart}}
\index{getGPIOStart@{getGPIOStart}!CANTramModule@{CANTramModule}}
\doxysubsubsection{\texorpdfstring{getGPIOStart()}{getGPIOStart()}}
{\footnotesize\ttfamily \label{class_c_a_n_tram_module_a7905817e8fee9e8bccfc9bbe70ae5669} 
uint8\+\_\+t CANTram\+Module\+::get\+GPIOStart (\begin{DoxyParamCaption}{}{}\end{DoxyParamCaption}) const\hspace{0.3cm}{\ttfamily [inline]}}

Get starting GPIO index assigned to the module. 

Returns the first GPIO index allocated to this module. \begin{DoxyReturn}{Returns}
uint8\+\_\+t GPIO start index. 
\end{DoxyReturn}
Here is the caller graph for this function\+:
\nopagebreak
\begin{figure}[H]
\begin{center}
\leavevmode

\end{center}
\end{figure}
\Hypertarget{class_c_a_n_tram_module_ae7247503120b76151cc2086dc4250911}\index{CANTramModule@{CANTramModule}!getGPIOSupply@{getGPIOSupply}}
\index{getGPIOSupply@{getGPIOSupply}!CANTramModule@{CANTramModule}}
\doxysubsubsection{\texorpdfstring{getGPIOSupply()}{getGPIOSupply()}}
{\footnotesize\ttfamily \label{class_c_a_n_tram_module_ae7247503120b76151cc2086dc4250911} 
virtual uint8\+\_\+t CANTram\+Module\+::get\+GPIOSupply (\begin{DoxyParamCaption}{}{}\end{DoxyParamCaption}) const\hspace{0.3cm}{\ttfamily [pure virtual]}}

Get the GPIO supply capacity of the module. 

Returns how many GPIOs this module provides/supplies to the system. \begin{DoxyReturn}{Returns}
uint8\+\_\+t Number of GPIOs supplied by the module. 
\end{DoxyReturn}

Implemented in \mbox{\hyperlink{class_analog_module_v1__0_a8f3dcb7de360ffab0709a04a9657f682}{Analog\+Module\+V1\+\_\+0}}, \mbox{\hyperlink{class_bus_module_v1__0_ab3624eb3ad2ae3333c22125fb0fee5b5}{Bus\+Module\+V1\+\_\+0}}, \mbox{\hyperlink{class_digital_module_v1__0_a659aa59723788b608b208e34fbbe50ab}{Digital\+Module\+V1\+\_\+0}}, \mbox{\hyperlink{class_main_module_v1__0_a716b45f8a875e8c156aa04ad17275605}{Main\+Module\+V1\+\_\+0}}, and \mbox{\hyperlink{class_relais_module_v1__0_ac06c3a60aebdb574e90d3b28a6b944e3}{Relais\+Module\+V1\+\_\+0}}.

\Hypertarget{class_c_a_n_tram_module_a3edca0142c5fa8a0d91a549f8371b460}\index{CANTramModule@{CANTramModule}!getHWType@{getHWType}}
\index{getHWType@{getHWType}!CANTramModule@{CANTramModule}}
\doxysubsubsection{\texorpdfstring{getHWType()}{getHWType()}}
{\footnotesize\ttfamily \label{class_c_a_n_tram_module_a3edca0142c5fa8a0d91a549f8371b460} 
virtual String CANTram\+Module\+::get\+HWType (\begin{DoxyParamCaption}{}{}\end{DoxyParamCaption}) const\hspace{0.3cm}{\ttfamily [pure virtual]}}

Get the hardware type string. 

Returns a human readable hardware type identifier for the concrete module implementation. \begin{DoxyReturn}{Returns}
String Hardware type identifier (e.\+g. "{}\+Main\+Module\+V1.\+0"{}). 
\end{DoxyReturn}

Implemented in \mbox{\hyperlink{class_analog_module_v1__0_a51a372016b5d240a79d49e6853bd8518}{Analog\+Module\+V1\+\_\+0}}, \mbox{\hyperlink{class_bus_module_v1__0_ad27db80f3d7030a0fafdd985079b3bdd}{Bus\+Module\+V1\+\_\+0}}, \mbox{\hyperlink{class_digital_module_v1__0_a529264909bab166dc52d224ca719011b}{Digital\+Module\+V1\+\_\+0}}, \mbox{\hyperlink{class_main_module_v1__0_aa9412fc0abc8f621580ab2bead087696}{Main\+Module\+V1\+\_\+0}}, and \mbox{\hyperlink{class_relais_module_v1__0_ad4d2c5de92e8bee2911ad9f228148c35}{Relais\+Module\+V1\+\_\+0}}.

Here is the caller graph for this function\+:
\nopagebreak
\begin{figure}[H]
\begin{center}
\leavevmode

\end{center}
\end{figure}
\Hypertarget{class_c_a_n_tram_module_a5d9287df902bd2f9ec32b4317f95fff6}\index{CANTramModule@{CANTramModule}!getHWVersion@{getHWVersion}}
\index{getHWVersion@{getHWVersion}!CANTramModule@{CANTramModule}}
\doxysubsubsection{\texorpdfstring{getHWVersion()}{getHWVersion()}}
{\footnotesize\ttfamily \label{class_c_a_n_tram_module_a5d9287df902bd2f9ec32b4317f95fff6} 
virtual String CANTram\+Module\+::get\+HWVersion (\begin{DoxyParamCaption}{}{}\end{DoxyParamCaption}) const\hspace{0.3cm}{\ttfamily [pure virtual]}}

Get the hardware version string. 

Returns the hardware revision/version string for the module. \begin{DoxyReturn}{Returns}
String Hardware version (e.\+g. "{}1.\+0"{}). 
\end{DoxyReturn}

Implemented in \mbox{\hyperlink{class_analog_module_v1__0_a7b4e1ca68f8d9f31965655a7d469592c}{Analog\+Module\+V1\+\_\+0}}, \mbox{\hyperlink{class_bus_module_v1__0_a64857b219f743fa39813812c9b911428}{Bus\+Module\+V1\+\_\+0}}, \mbox{\hyperlink{class_digital_module_v1__0_ad41f6d07efca1d95dac17f2f77fe1b82}{Digital\+Module\+V1\+\_\+0}}, \mbox{\hyperlink{class_main_module_v1__0_aa2cbb581d4fe04640109f0b6ecb0042a}{Main\+Module\+V1\+\_\+0}}, and \mbox{\hyperlink{class_relais_module_v1__0_a2256db6eb1b2430fc9fbb82ad05152dd}{Relais\+Module\+V1\+\_\+0}}.

\Hypertarget{class_c_a_n_tram_module_a68c703147d8b495e324febcaccd49dea}\index{CANTramModule@{CANTramModule}!getInterfaceCount@{getInterfaceCount}}
\index{getInterfaceCount@{getInterfaceCount}!CANTramModule@{CANTramModule}}
\doxysubsubsection{\texorpdfstring{getInterfaceCount()}{getInterfaceCount()}}
{\footnotesize\ttfamily \label{class_c_a_n_tram_module_a68c703147d8b495e324febcaccd49dea} 
virtual size\+\_\+t CANTram\+Module\+::get\+Interface\+Count (\begin{DoxyParamCaption}{}{}\end{DoxyParamCaption})\hspace{0.3cm}{\ttfamily [pure virtual]}}

Get number of interfaces provided by the module. 

Return the number of entries in the interfaces array returned by \doxylink{class_c_a_n_tram_module_a09c919fc31111badfec18faf64c729f4}{get\+Interfaces()}. \begin{DoxyReturn}{Returns}
size\+\_\+t Number of interface pointers. 
\end{DoxyReturn}

Implemented in \mbox{\hyperlink{class_analog_module_v1__0_a27c2aef9374563ee7a5130443233d333}{Analog\+Module\+V1\+\_\+0}}, \mbox{\hyperlink{class_bus_module_v1__0_ab2f8ee922f12c35d5d893cb4e07b4565}{Bus\+Module\+V1\+\_\+0}}, \mbox{\hyperlink{class_digital_module_v1__0_ad4d78cb2cf619fdf7f90455e27268b9f}{Digital\+Module\+V1\+\_\+0}}, \mbox{\hyperlink{class_main_module_v1__0_a58582a6adfe8c35b7bf6d17d683a6fa4}{Main\+Module\+V1\+\_\+0}}, and \mbox{\hyperlink{class_relais_module_v1__0_ae437de38ae5e1caa91ea6d6fca5b7519}{Relais\+Module\+V1\+\_\+0}}.

\Hypertarget{class_c_a_n_tram_module_a09c919fc31111badfec18faf64c729f4}\index{CANTramModule@{CANTramModule}!getInterfaces@{getInterfaces}}
\index{getInterfaces@{getInterfaces}!CANTramModule@{CANTramModule}}
\doxysubsubsection{\texorpdfstring{getInterfaces()}{getInterfaces()}}
{\footnotesize\ttfamily \label{class_c_a_n_tram_module_a09c919fc31111badfec18faf64c729f4} 
virtual \mbox{\hyperlink{class_interface}{Interface}} \texorpdfstring{$\ast$}{*}\texorpdfstring{$\ast$}{*} CANTram\+Module\+::get\+Interfaces (\begin{DoxyParamCaption}{}{}\end{DoxyParamCaption})\hspace{0.3cm}{\ttfamily [pure virtual]}}

Get pointer to module\textquotesingle{}s interface array. 

Returns a pointer to the internal Interface\texorpdfstring{$\ast$}{*} array used by the core to enumerate interfaces. \begin{DoxyReturn}{Returns}
Interface\texorpdfstring{$\ast$}{*}\texorpdfstring{$\ast$}{*} Pointer to the first element of the module\textquotesingle{}s interfaces array. 
\end{DoxyReturn}

Implemented in \mbox{\hyperlink{class_analog_module_v1__0_a25653fb8e041079aeec6c8be87cc077a}{Analog\+Module\+V1\+\_\+0}}, \mbox{\hyperlink{class_bus_module_v1__0_af6c2381228cdd502b31111301cb116fd}{Bus\+Module\+V1\+\_\+0}}, \mbox{\hyperlink{class_digital_module_v1__0_a67cd467b3c2ee6245938155a10778c20}{Digital\+Module\+V1\+\_\+0}}, \mbox{\hyperlink{class_main_module_v1__0_ab58fe7ec532bc345ccaa8139ee29ac38}{Main\+Module\+V1\+\_\+0}}, and \mbox{\hyperlink{class_relais_module_v1__0_a78579ed4ffa12aa6978e2c319632cbef}{Relais\+Module\+V1\+\_\+0}}.

\Hypertarget{class_c_a_n_tram_module_a80b400128bb6f0841953bb7a75cbf99c}\index{CANTramModule@{CANTramModule}!getSlot@{getSlot}}
\index{getSlot@{getSlot}!CANTramModule@{CANTramModule}}
\doxysubsubsection{\texorpdfstring{getSlot()}{getSlot()}}
{\footnotesize\ttfamily \label{class_c_a_n_tram_module_a80b400128bb6f0841953bb7a75cbf99c} 
uint8\+\_\+t CANTram\+Module\+::get\+Slot (\begin{DoxyParamCaption}{}{}\end{DoxyParamCaption}) const\hspace{0.3cm}{\ttfamily [inline]}}

Get assigned slot index. 

Returns the slot index the module was attached to via \doxylink{class_c_a_n_tram_module_a67cab1c238257e6d9b88afc4f644e477}{attach\+Module()}. \begin{DoxyReturn}{Returns}
uint8\+\_\+t Slot index. 
\end{DoxyReturn}
Here is the caller graph for this function\+:
\nopagebreak
\begin{figure}[H]
\begin{center}
\leavevmode

\end{center}
\end{figure}
\Hypertarget{class_c_a_n_tram_module_a6930dfb86a2e06ab9a9b299520830fb7}\index{CANTramModule@{CANTramModule}!initialize@{initialize}}
\index{initialize@{initialize}!CANTramModule@{CANTramModule}}
\doxysubsubsection{\texorpdfstring{initialize()}{initialize()}}
{\footnotesize\ttfamily \label{class_c_a_n_tram_module_a6930dfb86a2e06ab9a9b299520830fb7} 
virtual bool CANTram\+Module\+::initialize (\begin{DoxyParamCaption}{}{}\end{DoxyParamCaption})\hspace{0.3cm}{\ttfamily [pure virtual]}}

Initialize the module after attachment and provisioning. 

Perform runtime initialization (start drivers, begin peripherals) once all modules have been attached. \begin{DoxyReturn}{Returns}
true if initialization succeeded, false otherwise. 
\end{DoxyReturn}

Implemented in \mbox{\hyperlink{class_analog_module_v1__0_ad93b42ec5c2d12a57aece35289506add}{Analog\+Module\+V1\+\_\+0}}, \mbox{\hyperlink{class_bus_module_v1__0_aedf45f0be91985e58f6b6d08af048fb3}{Bus\+Module\+V1\+\_\+0}}, \mbox{\hyperlink{class_digital_module_v1__0_adbbb9654bd1819b20c6247ea3a9eb291}{Digital\+Module\+V1\+\_\+0}}, \mbox{\hyperlink{class_main_module_v1__0_a1b5ee0f095998b264fa3424e0dd9cdc5}{Main\+Module\+V1\+\_\+0}}, and \mbox{\hyperlink{class_relais_module_v1__0_aee1e17f77ccc4737865e34291e86c103}{Relais\+Module\+V1\+\_\+0}}.

\Hypertarget{class_c_a_n_tram_module_a329b502ade3a32987994381c93ddbd0b}\index{CANTramModule@{CANTramModule}!preInitialize@{preInitialize}}
\index{preInitialize@{preInitialize}!CANTramModule@{CANTramModule}}
\doxysubsubsection{\texorpdfstring{preInitialize()}{preInitialize()}}
{\footnotesize\ttfamily \label{class_c_a_n_tram_module_a329b502ade3a32987994381c93ddbd0b} 
virtual bool CANTram\+Module\+::pre\+Initialize (\begin{DoxyParamCaption}{}{}\end{DoxyParamCaption})\hspace{0.3cm}{\ttfamily [inline]}, {\ttfamily [virtual]}}

Pre-\/initialize the module after attachment and provisioning. 

Perform any pre-\/initialization steps before the main \doxylink{class_c_a_n_tram_module_a6930dfb86a2e06ab9a9b299520830fb7}{initialize()} call. May be used to establish e.\+g. i2c communication needed for initialization. \begin{DoxyReturn}{Returns}
true if pre-\/initialization succeeded, false otherwise. 
\end{DoxyReturn}

Reimplemented in \mbox{\hyperlink{class_bus_module_v1__0_ae39f45e115c9d24cb7adf367fbdd64b7}{Bus\+Module\+V1\+\_\+0}}, and \mbox{\hyperlink{class_main_module_v1__0_a2917d9056213cc8633b13f91722be603}{Main\+Module\+V1\+\_\+0}}.

\Hypertarget{class_c_a_n_tram_module_abaad4d92c02fc8bb525a57d8ac06db7e}\index{CANTramModule@{CANTramModule}!provideGPIOs@{provideGPIOs}}
\index{provideGPIOs@{provideGPIOs}!CANTramModule@{CANTramModule}}
\doxysubsubsection{\texorpdfstring{provideGPIOs()}{provideGPIOs()}}
{\footnotesize\ttfamily \label{class_c_a_n_tram_module_abaad4d92c02fc8bb525a57d8ac06db7e} 
virtual bool CANTram\+Module\+::provide\+GPIOs (\begin{DoxyParamCaption}{}{}\end{DoxyParamCaption})\hspace{0.3cm}{\ttfamily [pure virtual]}}

Provide GPIO definitions to the core. 

Called during module attachment to allow the module to declare any GPIOs it owns or provides. \begin{DoxyReturn}{Returns}
true if GPIO definitions were provided successfully, false otherwise. 
\end{DoxyReturn}

Implemented in \mbox{\hyperlink{class_analog_module_v1__0_a214392a00aecdb232ff0cf0c12271d7c}{Analog\+Module\+V1\+\_\+0}}, \mbox{\hyperlink{class_bus_module_v1__0_ae608f88ec327b8ea590cfe5767ae6106}{Bus\+Module\+V1\+\_\+0}}, \mbox{\hyperlink{class_digital_module_v1__0_a70d92346670144adca80528dbfad8fe4}{Digital\+Module\+V1\+\_\+0}}, \mbox{\hyperlink{class_main_module_v1__0_a85406338313930631d9da73cf9248a8c}{Main\+Module\+V1\+\_\+0}}, and \mbox{\hyperlink{class_relais_module_v1__0_a6373363c88ca982860ec7f07f81005cb}{Relais\+Module\+V1\+\_\+0}}.

Here is the caller graph for this function\+:
\nopagebreak
\begin{figure}[H]
\begin{center}
\leavevmode
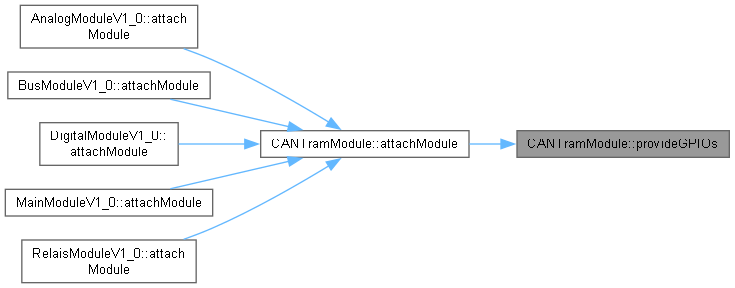
[picture p61: Doxygen/html/d2/dee/class_c_a_n_tram_module_abaad4d92c02fc8bb525a57d8ac06db7e_icgraph.png]

\end{center}
\end{figure}
\Hypertarget{class_c_a_n_tram_module_aa509ae950722ebd48383c124ec6a63ec}\index{CANTramModule@{CANTramModule}!provideHardwareResources@{provideHardwareResources}}
\index{provideHardwareResources@{provideHardwareResources}!CANTramModule@{CANTramModule}}
\doxysubsubsection{\texorpdfstring{provideHardwareResources()}{provideHardwareResources()}}
{\footnotesize\ttfamily \label{class_c_a_n_tram_module_aa509ae950722ebd48383c124ec6a63ec} 
virtual bool CANTram\+Module\+::provide\+Hardware\+Resources (\begin{DoxyParamCaption}{}{}\end{DoxyParamCaption})\hspace{0.3cm}{\ttfamily [pure virtual]}}

Provide hardware resources (e.\+g., I2C, SPI, UART) to the core. 

Called during attachment to attach \doxylink{class_hardware_resource}{Hardware\+Resource} instances that other modules can request. \begin{DoxyReturn}{Returns}
true if resources were successfully provided, false otherwise. 
\end{DoxyReturn}

Implemented in \mbox{\hyperlink{class_analog_module_v1__0_a094a3fac21a9835d501d965dc6c3f4bf}{Analog\+Module\+V1\+\_\+0}}, \mbox{\hyperlink{class_bus_module_v1__0_a5d7b5c4ee7d5a1ba9d8ed0628a7f597f}{Bus\+Module\+V1\+\_\+0}}, \mbox{\hyperlink{class_digital_module_v1__0_abea9ddf782b2583cca8caf4d268ee203}{Digital\+Module\+V1\+\_\+0}}, \mbox{\hyperlink{class_main_module_v1__0_aa67512e4c9fda1474b76868708383778}{Main\+Module\+V1\+\_\+0}}, and \mbox{\hyperlink{class_relais_module_v1__0_ac9c120d926b21c489108c1f925f2abac}{Relais\+Module\+V1\+\_\+0}}.

Here is the caller graph for this function\+:
\nopagebreak
\begin{figure}[H]
\begin{center}
\leavevmode
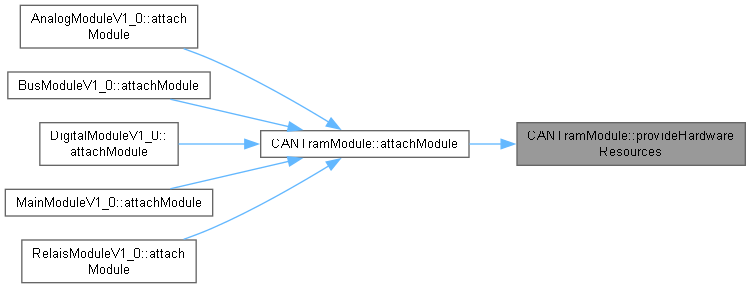
[picture p62: Doxygen/html/d2/dee/class_c_a_n_tram_module_aa509ae950722ebd48383c124ec6a63ec_icgraph.png]

\end{center}
\end{figure}
\Hypertarget{class_c_a_n_tram_module_a7f2c1c05cafb19676aed58c11219d0f5}\index{CANTramModule@{CANTramModule}!requestGPIOs@{requestGPIOs}}
\index{requestGPIOs@{requestGPIOs}!CANTramModule@{CANTramModule}}
\doxysubsubsection{\texorpdfstring{requestGPIOs()}{requestGPIOs()}}
{\footnotesize\ttfamily \label{class_c_a_n_tram_module_a7f2c1c05cafb19676aed58c11219d0f5} 
virtual bool CANTram\+Module\+::request\+GPIOs (\begin{DoxyParamCaption}{}{}\end{DoxyParamCaption})\hspace{0.3cm}{\ttfamily [pure virtual]}}

Request GPIO definitions from the core. 

Called after provide\+GPIOs to obtain runtime GPIO assignments from \doxylink{class_c_a_n_tram_core}{CANTram\+Core}. \begin{DoxyReturn}{Returns}
true if required GPIOs were acquired and validated, false otherwise. 
\end{DoxyReturn}

Implemented in \mbox{\hyperlink{class_analog_module_v1__0_ad075b7cce67bb33101d4c831a8125ef3}{Analog\+Module\+V1\+\_\+0}}, \mbox{\hyperlink{class_bus_module_v1__0_a4a285d859c46cc480e2ccc452e1f0f38}{Bus\+Module\+V1\+\_\+0}}, \mbox{\hyperlink{class_digital_module_v1__0_ad4f0b8f23b9bb1cece68d1eea31ceb59}{Digital\+Module\+V1\+\_\+0}}, \mbox{\hyperlink{class_main_module_v1__0_a0e0d8a91bc062d1b9bd6c77335ec9e95}{Main\+Module\+V1\+\_\+0}}, and \mbox{\hyperlink{class_relais_module_v1__0_af2e4f33d631bc14e433c404678347b67}{Relais\+Module\+V1\+\_\+0}}.

Here is the caller graph for this function\+:
\nopagebreak
\begin{figure}[H]
\begin{center}
\leavevmode
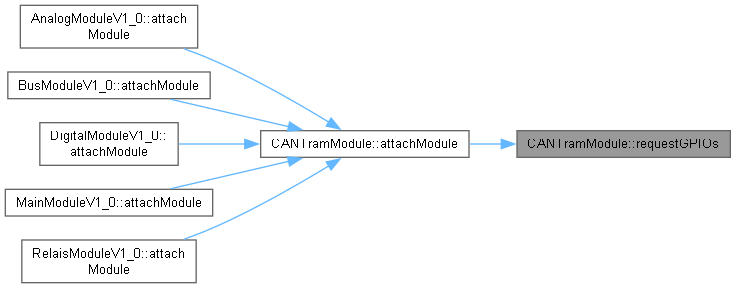
[picture p63: Doxygen/html/d2/dee/class_c_a_n_tram_module_a7f2c1c05cafb19676aed58c11219d0f5_icgraph.png]

\end{center}
\end{figure}
\Hypertarget{class_c_a_n_tram_module_a88dd0ab2213df828b576d337e38c1ac8}\index{CANTramModule@{CANTramModule}!requestHardwareResources@{requestHardwareResources}}
\index{requestHardwareResources@{requestHardwareResources}!CANTramModule@{CANTramModule}}
\doxysubsubsection{\texorpdfstring{requestHardwareResources()}{requestHardwareResources()}}
{\footnotesize\ttfamily \label{class_c_a_n_tram_module_a88dd0ab2213df828b576d337e38c1ac8} 
virtual bool CANTram\+Module\+::request\+Hardware\+Resources (\begin{DoxyParamCaption}{}{}\end{DoxyParamCaption})\hspace{0.3cm}{\ttfamily [pure virtual]}}

Request hardware resources from the core. 

Called when the module should acquire hardware resources supplied by the system (e.\+g., UART core). \begin{DoxyReturn}{Returns}
true if all required hardware resources were granted, false otherwise. 
\end{DoxyReturn}

Implemented in \mbox{\hyperlink{class_analog_module_v1__0_ac7d18b81c9980020734c35b7987219b6}{Analog\+Module\+V1\+\_\+0}}, \mbox{\hyperlink{class_bus_module_v1__0_a805fbe1982b45754d54965eef97c73e3}{Bus\+Module\+V1\+\_\+0}}, \mbox{\hyperlink{class_digital_module_v1__0_aee7d56d42e8e1ef25085cb24385286c5}{Digital\+Module\+V1\+\_\+0}}, \mbox{\hyperlink{class_main_module_v1__0_a40ad97aab74f5d8f08e11456036f835c}{Main\+Module\+V1\+\_\+0}}, and \mbox{\hyperlink{class_relais_module_v1__0_abb33be265117a963c1ab9c34e34ea082}{Relais\+Module\+V1\+\_\+0}}.

Here is the caller graph for this function\+:
\nopagebreak
\begin{figure}[H]
\begin{center}
\leavevmode
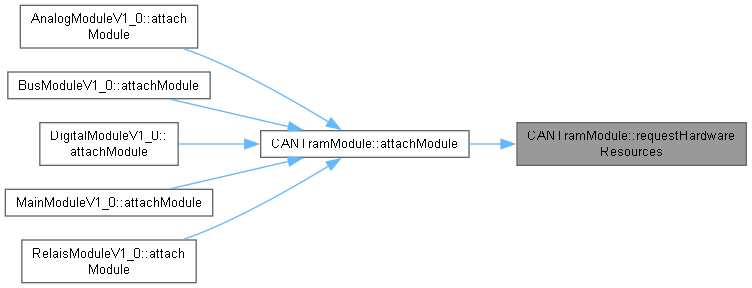
[picture p64: Doxygen/html/d2/dee/class_c_a_n_tram_module_a88dd0ab2213df828b576d337e38c1ac8_icgraph.png]

\end{center}
\end{figure}
\Hypertarget{class_c_a_n_tram_module_a496814b4e5fa5f162c48f17ec33d4475}\index{CANTramModule@{CANTramModule}!reset@{reset}}
\index{reset@{reset}!CANTramModule@{CANTramModule}}
\doxysubsubsection{\texorpdfstring{reset()}{reset()}}
{\footnotesize\ttfamily \label{class_c_a_n_tram_module_a496814b4e5fa5f162c48f17ec33d4475} 
bool CANTram\+Module\+::reset (\begin{DoxyParamCaption}{}{}\end{DoxyParamCaption})\hspace{0.3cm}{\ttfamily [virtual]}}

Reset the module to a known default state. 

Optional override for module-\/specific reset logic. Base implementation should be safe to call. \begin{DoxyReturn}{Returns}
true if reset succeeded, false otherwise.
\end{DoxyReturn}
Default implementation performs module reset actions. It logs the reset operation and returns true. Derived classes may override to perform additional hardware or state reset behavior. \begin{DoxyReturn}{Returns}
true if reset succeeded, false otherwise. 
\end{DoxyReturn}

Reimplemented in \mbox{\hyperlink{class_analog_module_v1__0_af605e705430ba08785ac8dfd68e5efa7}{Analog\+Module\+V1\+\_\+0}}, \mbox{\hyperlink{class_bus_module_v1__0_adca07691ab1dbe6942abd50e3b6a2a23}{Bus\+Module\+V1\+\_\+0}}, and \mbox{\hyperlink{class_main_module_v1__0_a25ea3d52611cb89711973e8c068bbbfc}{Main\+Module\+V1\+\_\+0}}.

Here is the caller graph for this function\+:
\nopagebreak
\begin{figure}[H]
\begin{center}
\leavevmode

\end{center}
\end{figure}

The documentation for this class was generated from the following files\+:\begin{DoxyCompactItemize}
\item 
C\+:/\+Users/leowa/\+Documents/\+Platform\+IO/\+Projects/\+CANTram\+Framework\+Usage/lib/\+CANTram\+Framework/include/\mbox{\hyperlink{_c_a_n_tram_module_8h}{CANTram\+Module.\+h}}\item 
C\+:/\+Users/leowa/\+Documents/\+Platform\+IO/\+Projects/\+CANTram\+Framework\+Usage/lib/\+CANTram\+Framework/src/abstract/CANTram\+Module.\+cpp\end{DoxyCompactItemize}
