LeoWatti99/CANTram-Framework/Doxygen/latex/d3/dc5/_c_a_n_core_8h_source.tex

\doxysection{CANCore.\+h}
\hypertarget{_c_a_n_core_8h_source}{}\label{_c_a_n_core_8h_source}\index{C:/Users/leowa/Documents/PlatformIO/Projects/CANTramFrameworkUsage/lib/CANTramFramework/include/CANCore.h@{C:/Users/leowa/Documents/PlatformIO/Projects/CANTramFrameworkUsage/lib/CANTramFramework/include/CANCore.h}}
\mbox{\hyperlink{_c_a_n_core_8h}{Go to the documentation of this file.}}
\begin{DoxyCode}{0}
\DoxyCodeLine{00001\ \textcolor{preprocessor}{\#ifndef\ CANCORE\_H}}
\DoxyCodeLine{00002\ \textcolor{preprocessor}{\#define\ CANCORE\_H}}
\DoxyCodeLine{00003\ }
\DoxyCodeLine{00004\ \textcolor{preprocessor}{\#include\ <Arduino.h>}}
\DoxyCodeLine{00005\ \textcolor{preprocessor}{\#include\ "{}\mbox{\hyperlink{_hardware_resource_8h}{HardwareResource.h}}"{}}}
\DoxyCodeLine{00006\ }
\DoxyCodeLine{00007\ \textcolor{preprocessor}{\#include\ "{}\mbox{\hyperlink{_debug_8h}{Debug.h}}"{}}}
\DoxyCodeLine{00013\ \textcolor{keyword}{class\ }CANCore\ :\ \textcolor{keyword}{public}\ \mbox{\hyperlink{class_hardware_resource_a7ddffb890a743f2df28128d9afd5bfa5}{HardwareResource}}\{\ }
\DoxyCodeLine{00014\ \textcolor{keyword}{public}:}
\DoxyCodeLine{00015\ }
\DoxyCodeLine{00016\ \textcolor{keyword}{struct\ }\mbox{\hyperlink{struct_c_a_n_core_1_1_c_a_n_message}{CANMessage}}\ \{}
\DoxyCodeLine{00017\ \ \ \ \ uint32\_t\ \ \ \ id;\ \ \ \ \ \ \ \ \ \ \textcolor{comment}{//\ 11-\/bit\ or\ 29-\/bit\ identifier}}
\DoxyCodeLine{00018\ \ \ \ \ \textcolor{keywordtype}{bool}\ \ \ \ \ \ \ \ isExtended;\ \textcolor{comment}{//\ True\ if\ extended\ ID\ (29-\/bit),\ false\ for\ standard\ ID\ (11-\/bit)}}
\DoxyCodeLine{00019\ \ \ \ \ \textcolor{keywordtype}{bool}\ \ \ \ \ \ \ \ isRemote;\ \ \ \textcolor{comment}{//\ True\ if\ remote\ frame}}
\DoxyCodeLine{00020\ \ \ \ \ uint8\_t\ \ \ \ \ data[8];\ \ \ \ \textcolor{comment}{//\ Data\ payload\ (0-\/8\ bytes)}}
\DoxyCodeLine{00021\ \ \ \ \ uint8\_t\ \ \ \ \ length;\ \ \ \ \ \textcolor{comment}{//\ Length\ of\ data\ in\ bytes}}
\DoxyCodeLine{00022\ \ \ \ \ \textcolor{keywordtype}{bool}\ \ \ \ \ \ \ \ error;\ \ \ \ \ \ \textcolor{comment}{//\ Flag\ for\ error\ frames\ \ }}
\DoxyCodeLine{00023\ \ \ \ \ String\ toString()\textcolor{keyword}{\ const\ }\{}
\DoxyCodeLine{00024\ \ \ \ \ \ \ \ \ String\ msg\ =\ \textcolor{stringliteral}{"{}CANMessage[ID:\ "{}}\ +\ String(\textcolor{keywordtype}{id})\ +\ (isExtended\ ?\ \textcolor{stringliteral}{"{}\ (Extended)"{}}\ :\ \textcolor{stringliteral}{"{}\ (Standard)"{}})\ +\ \textcolor{stringliteral}{"{},\ Remote:\ "{}}\ +\ String(isRemote)\ +\ \textcolor{stringliteral}{"{},\ Length:\ "{}}\ +\ String(length)\ +\ \textcolor{stringliteral}{"{},\ Data:\ "{}};}
\DoxyCodeLine{00025\ \ \ \ \ \ \ \ \ \textcolor{keywordflow}{for}(uint8\_t\ i=0;\ i<length;\ i++)\ \{}
\DoxyCodeLine{00026\ \ \ \ \ \ \ \ \ \ \ \ \ msg\ +=\ String(data[i],\ HEX);}
\DoxyCodeLine{00027\ \ \ \ \ \ \ \ \ \ \ \ \ \textcolor{keywordflow}{if}(i\ <\ length\ -\/\ 1)\ msg\ +=\ \textcolor{stringliteral}{"{}\ "{}};}
\DoxyCodeLine{00028\ \ \ \ \ \ \ \ \ \}}
\DoxyCodeLine{00029\ \ \ \ \ \ \ \ \ msg\ +=\ \textcolor{stringliteral}{"{}]"{}};}
\DoxyCodeLine{00030\ \ \ \ \ \ \ \ \ \textcolor{keywordflow}{return}\ msg;}
\DoxyCodeLine{00031\ \ \ \ \ \}\ \ }
\DoxyCodeLine{00032\ \};}
\DoxyCodeLine{00033\ }
\DoxyCodeLine{00034\ \textcolor{keyword}{enum}\ Baudrate\ \{}
\DoxyCodeLine{00035\ \ \ \ \ BR\_NOT\_SET\ =\ 0,}
\DoxyCodeLine{00036\ \ \ \ \ BR\_125K\ =\ 125000,}
\DoxyCodeLine{00037\ \ \ \ \ BR\_250K\ =\ 250000,}
\DoxyCodeLine{00038\ \ \ \ \ BR\_500K\ =\ 500000,}
\DoxyCodeLine{00039\ \ \ \ \ BR\_1M\ \ \ =\ 1000000}
\DoxyCodeLine{00040\ \};}
\DoxyCodeLine{00041\ }
\DoxyCodeLine{00042\ \textcolor{keyword}{enum}\ Status\{}
\DoxyCodeLine{00043\ \ \ \ \ STATUS\_OK,}
\DoxyCodeLine{00044\ \ \ \ \ STATUS\_ERROR\_ACTIVE,}
\DoxyCodeLine{00045\ \ \ \ \ STATUS\_BUS\_OFF,}
\DoxyCodeLine{00046\ \ \ \ \ STATUS\_ERROR\_PASSIVE}
\DoxyCodeLine{00047\ \};}
\DoxyCodeLine{00048\ }
\DoxyCodeLine{00049\ \textcolor{keyword}{enum}\ FilterType\ \{}
\DoxyCodeLine{00050\ \ \ \ \ FILTER\_ACCEPT\_ALL,}
\DoxyCodeLine{00051\ \ \ \ \ FILTER\_MATCH\_ID,}
\DoxyCodeLine{00052\ \ \ \ \ FILTER\_MASKED}
\DoxyCodeLine{00053\ \};}
\DoxyCodeLine{00054\ }
\DoxyCodeLine{00055\ \ \ \ \ }
\DoxyCodeLine{00056\ \ \ \ \ \textcolor{keyword}{virtual}\ \textcolor{keywordtype}{bool}\ begin()=0;}
\DoxyCodeLine{00057\ \ \ \ \ \textcolor{keyword}{virtual}\ \textcolor{keywordtype}{bool}\ setBaudrate(Baudrate\ baudrate)=0;}
\DoxyCodeLine{00058\ \ \ \ \ \textcolor{keyword}{virtual}\ \textcolor{keywordtype}{bool}\ setPins(int8\_t\ txPin,\ int8\_t\ rxPin)=0;}
\DoxyCodeLine{00059\ \ \ \ \ \textcolor{keyword}{virtual}\ \textcolor{keywordtype}{bool}\ end()=0;}
\DoxyCodeLine{00060\ \ \ \ \ \textcolor{keyword}{virtual}\ \textcolor{keywordtype}{bool}\ sendMessage(\textcolor{keyword}{const}\ \mbox{\hyperlink{struct_c_a_n_core_1_1_c_a_n_message}{CANMessage}}\&\ message)=0;}
\DoxyCodeLine{00061\ \ \ \ \ \textcolor{keyword}{virtual}\ \textcolor{keywordtype}{bool}\ readMessage(\mbox{\hyperlink{struct_c_a_n_core_1_1_c_a_n_message}{CANMessage}}\&\ message)=0;}
\DoxyCodeLine{00062\ \ \ \ \ \textcolor{keyword}{virtual}\ uint8\_t\ available()=0;}
\DoxyCodeLine{00063\ \ \ \ \ \textcolor{keyword}{virtual}\ \textcolor{keywordtype}{bool}\ setupFilter(uint32\_t\ \textcolor{keywordtype}{id},\ uint32\_t\ mask)=0;}
\DoxyCodeLine{00064\ }
\DoxyCodeLine{00065\ \ \ \ \ Baudrate\ getBaudrate()\textcolor{keyword}{\ const\ }\{\ \textcolor{keywordflow}{return}\ \_baudrate;\ \}}
\DoxyCodeLine{00066\ \ \ \ \ uint8\_t\ getTxPin()\textcolor{keyword}{\ const\ }\{\ \textcolor{keywordflow}{return}\ \_txPin;\ \}}
\DoxyCodeLine{00067\ \ \ \ \ uint8\_t\ getRxPin()\textcolor{keyword}{\ const\ }\{\ \textcolor{keywordflow}{return}\ \_rxPin;\ \}}
\DoxyCodeLine{00068\ }
\DoxyCodeLine{00069\ \ \ \ \ \textcolor{keyword}{virtual}\ \textcolor{keywordtype}{bool}\ \mbox{\hyperlink{class_c_a_n_core_a611efb48b44ea62f1a7b6428671863ca}{reset}}()\textcolor{keyword}{\ override\ }\{}
\DoxyCodeLine{00070\ \ \ \ \ \ \ \ \ \mbox{\hyperlink{_debug_8h_a693063ba84ad2119e7f3ea1b97947055}{INFO\_PRINTLN}}(\textcolor{stringliteral}{"{}[CANCore]\ Resetting\ CAN\ core."{}});}
\DoxyCodeLine{00071\ \ \ \ \ \ \ \ \ }
\DoxyCodeLine{00072\ \ \ \ \ \ \ \ \ \textcolor{keywordtype}{bool}\ success\ =\ end();}
\DoxyCodeLine{00073\ \ \ \ \ \ \ \ \ \_isInitialized\ =\ \textcolor{keyword}{false};}
\DoxyCodeLine{00074\ \ \ \ \ \ \ \ \ \_txPin\ =\ -\/1;}
\DoxyCodeLine{00075\ \ \ \ \ \ \ \ \ \_rxPin\ =\ -\/1;}
\DoxyCodeLine{00076\ \ \ \ \ \ \ \ \ \_filterId\ =\ 0;}
\DoxyCodeLine{00077\ \ \ \ \ \ \ \ \ \_filterMask\ =\ 0;}
\DoxyCodeLine{00078\ \ \ \ \ \ \ \ \ \_baudrate\ =\ BR\_NOT\_SET;}
\DoxyCodeLine{00079\ \ \ \ \ \ \ \ \ \_filterType\ =\ FILTER\_ACCEPT\_ALL;}
\DoxyCodeLine{00080\ \ \ \ \ \ \ \ \ \_status\ =\ STATUS\_OK;}
\DoxyCodeLine{00081\ \ \ \ \ \ \ \ \ success\ \&=\ \mbox{\hyperlink{class_hardware_resource_a7372684f2afb5139ef8464194a087649}{HardwareResource::reset}}();}
\DoxyCodeLine{00082\ \ \ \ \ \ \ \ \ \textcolor{keywordflow}{return}\ success;}
\DoxyCodeLine{00083\ \ \ \ \ \}}
\DoxyCodeLine{00084\ \ \ \ \ }
\DoxyCodeLine{00085\ }
\DoxyCodeLine{00086\ \ \ \ \ \textcolor{keyword}{protected}:\ \ }
\DoxyCodeLine{00087\ \ \ \ \ \mbox{\hyperlink{class_c_a_n_core}{CANCore}}()=\textcolor{keywordflow}{default};}
\DoxyCodeLine{00088\ \ \ \ \ \mbox{\hyperlink{class_c_a_n_core}{\string~CANCore}}()=\textcolor{keywordflow}{default};}
\DoxyCodeLine{00089\ }
\DoxyCodeLine{00090\ \ \ \ \ Baudrate\ \_baudrate\ =\ BR\_NOT\_SET;}
\DoxyCodeLine{00091\ \ \ \ \ FilterType\ \_filterType\ =\ FILTER\_ACCEPT\_ALL;}
\DoxyCodeLine{00092\ \ \ \ \ int8\_t\ \ \_txPin\ =\ -\/1;}
\DoxyCodeLine{00093\ \ \ \ \ int8\_t\ \ \_rxPin\ =\ -\/1;}
\DoxyCodeLine{00094\ \ \ \ \ Status\ \ \ \_status\ =\ STATUS\_OK;}
\DoxyCodeLine{00095\ \ \ \ \ \textcolor{keywordtype}{bool}\ \ \ \ \_isInitialized\ =\ \textcolor{keyword}{false};}
\DoxyCodeLine{00096\ \ \ \ \ uint32\_t\ \_filterId\ =\ 0;}
\DoxyCodeLine{00097\ \ \ \ \ uint32\_t\ \_filterMask\ =\ 0;}
\DoxyCodeLine{00098\ }
\DoxyCodeLine{00099\ }
\DoxyCodeLine{00100\ \};}
\DoxyCodeLine{00101\ }
\DoxyCodeLine{00102\ \textcolor{preprocessor}{\#endif}}

\end{DoxyCode}
