LeoWatti99/CANTram-Framework/Doxygen/latex/d3/dfd/struct_m_a_x22531_1_1_burst_response.tex

\doxysection{MAX22531\+::Burst\+Response Struct Reference}
\hypertarget{struct_m_a_x22531_1_1_burst_response}{}\label{struct_m_a_x22531_1_1_burst_response}\index{MAX22531::BurstResponse@{MAX22531::BurstResponse}}
\doxysubsubsection*{Public Attributes}
\begin{DoxyCompactItemize}
\item 
\Hypertarget{struct_m_a_x22531_1_1_burst_response_a2f0e1054cb96b1ffff8ca1a31d04a82f}\label{struct_m_a_x22531_1_1_burst_response_a2f0e1054cb96b1ffff8ca1a31d04a82f} 
uint8\+\_\+t {\bfseries status}
\item 
\Hypertarget{struct_m_a_x22531_1_1_burst_response_a4ec8cdd65e3b6ca6842edb526d5654d9}\label{struct_m_a_x22531_1_1_burst_response_a4ec8cdd65e3b6ca6842edb526d5654d9} 
uint16\+\_\+t {\bfseries adc1}
\item 
\Hypertarget{struct_m_a_x22531_1_1_burst_response_a6be1a3884ce0fe4bb4a6f2eb6fee412e}\label{struct_m_a_x22531_1_1_burst_response_a6be1a3884ce0fe4bb4a6f2eb6fee412e} 
uint16\+\_\+t {\bfseries adc2}
\item 
\Hypertarget{struct_m_a_x22531_1_1_burst_response_af48578de66ba11937baa4657aa7fd9bf}\label{struct_m_a_x22531_1_1_burst_response_af48578de66ba11937baa4657aa7fd9bf} 
uint16\+\_\+t {\bfseries adc3}
\item 
\Hypertarget{struct_m_a_x22531_1_1_burst_response_a9013239c0b4473505b4b6524bfa5485c}\label{struct_m_a_x22531_1_1_burst_response_a9013239c0b4473505b4b6524bfa5485c} 
uint16\+\_\+t {\bfseries adc4}
\item 
\Hypertarget{struct_m_a_x22531_1_1_burst_response_ad84d07c1d40d295b874f8f2e7757cb79}\label{struct_m_a_x22531_1_1_burst_response_ad84d07c1d40d295b874f8f2e7757cb79} 
uint16\+\_\+t {\bfseries interrupt}
\item 
\Hypertarget{struct_m_a_x22531_1_1_burst_response_aaf6db2153fc983e5cdbb86e16cc22baf}\label{struct_m_a_x22531_1_1_burst_response_aaf6db2153fc983e5cdbb86e16cc22baf} 
uint8\+\_\+t {\bfseries crc}
\item 
\Hypertarget{struct_m_a_x22531_1_1_burst_response_a89bd1d2fb11245144d37d6819b1d2121}\label{struct_m_a_x22531_1_1_burst_response_a89bd1d2fb11245144d37d6819b1d2121} 
bool {\bfseries filtered}
\end{DoxyCompactItemize}

The documentation for this struct was generated from the following file\+:\begin{DoxyCompactItemize}
\item 
C\+:/\+Users/leowa/\+Documents/\+Platform\+IO/\+Projects/\+CANTram\+Framework\+Usage/lib/\+CANTram\+Framework/include/\mbox{\hyperlink{_m_a_x22531_8h}{MAX22531.\+h}}\end{DoxyCompactItemize}
