LeoWatti99/CANTram-Framework/Doxygen/latex/d5/d31/class_s_p_i_chip.tex

\doxysection{SPIChip Class Reference}
\hypertarget{class_s_p_i_chip}{}\label{class_s_p_i_chip}\index{SPIChip@{SPIChip}}

Inheritance diagram for SPIChip\+:
\nopagebreak
\begin{figure}[H]
\begin{center}
\leavevmode

\end{center}
\end{figure}
\doxysubsubsection*{Public Member Functions}
\begin{DoxyCompactItemize}
\item 
\Hypertarget{class_s_p_i_chip_a05142620f5e942bb549ea42c3c7bde46}\label{class_s_p_i_chip_a05142620f5e942bb549ea42c3c7bde46} 
void {\bfseries activate\+External\+Chip\+Select} ()
\item 
\Hypertarget{class_s_p_i_chip_af43ab3e1cb49c430a4d6dc168c4a4f20}\label{class_s_p_i_chip_af43ab3e1cb49c430a4d6dc168c4a4f20} 
void {\bfseries set\+CSControl\+Callback} (std\+::function$<$ void(bool)$>$ callback)
\item 
\Hypertarget{class_s_p_i_chip_abc8896042806c4f04596b4cac8d24f8c}\label{class_s_p_i_chip_abc8896042806c4f04596b4cac8d24f8c} 
void {\bfseries set\+CSPin} (int cs\+Pin)
\end{DoxyCompactItemize}
\doxysubsubsection*{Protected Member Functions}
\begin{DoxyCompactItemize}
\item 
\Hypertarget{class_s_p_i_chip_a1070900c831fd57c6c568220da4c0f2e}\label{class_s_p_i_chip_a1070900c831fd57c6c568220da4c0f2e} 
{\bfseries SPIChip} (uint8\+\_\+t cs\+Pin)
\item 
\Hypertarget{class_s_p_i_chip_ad3586454553f42bdd25870455032fb08}\label{class_s_p_i_chip_ad3586454553f42bdd25870455032fb08} 
void {\bfseries select\+Chip} ()
\item 
\Hypertarget{class_s_p_i_chip_abb426bd1b3b619daefd80229019bae4c}\label{class_s_p_i_chip_abb426bd1b3b619daefd80229019bae4c} 
void {\bfseries deselect\+Chip} ()
\end{DoxyCompactItemize}
\doxysubsubsection*{Protected Attributes}
\begin{DoxyCompactItemize}
\item 
\Hypertarget{class_s_p_i_chip_abed67574d519cce55367042dc7dec047}\label{class_s_p_i_chip_abed67574d519cce55367042dc7dec047} 
int {\bfseries \+\_\+cs\+Pin}
\item 
\Hypertarget{class_s_p_i_chip_a55762566dac17024f06f8c5ce366df48}\label{class_s_p_i_chip_a55762566dac17024f06f8c5ce366df48} 
bool {\bfseries use\+External\+Chip\+Select} = false
\item 
\Hypertarget{class_s_p_i_chip_ae253c8b0af362aa3345721b9276576e6}\label{class_s_p_i_chip_ae253c8b0af362aa3345721b9276576e6} 
std\+::function$<$ void(bool)$>$ {\bfseries cs\+Control} = nullptr
\end{DoxyCompactItemize}

The documentation for this class was generated from the following file\+:\begin{DoxyCompactItemize}
\item 
C\+:/\+Users/leowa/\+Documents/\+Platform\+IO/\+Projects/\+CANTram\+Framework\+Usage/lib/\+CANTram\+Framework/include/SPIChip.\+h\end{DoxyCompactItemize}
