LeoWatti99/CANTram-Framework/Doxygen/latex/d6/d59/_m_a_x22531_8h.tex

\doxysection{C\+:/\+Users/leowa/\+Documents/\+Platform\+IO/\+Projects/\+CANTram\+Framework\+Usage/lib/\+CANTram\+Framework/include/\+MAX22531.h File Reference}
\hypertarget{_m_a_x22531_8h}{}\label{_m_a_x22531_8h}\index{C:/Users/leowa/Documents/PlatformIO/Projects/CANTramFrameworkUsage/lib/CANTramFramework/include/MAX22531.h@{C:/Users/leowa/Documents/PlatformIO/Projects/CANTramFrameworkUsage/lib/CANTramFramework/include/MAX22531.h}}
{\ttfamily \#include $<$Arduino.\+h$>$}\newline
{\ttfamily \#include $<$SPI.\+h$>$}\newline
{\ttfamily \#include "{}MAX22531\+\_\+registers.\+h"{}}\newline
{\ttfamily \#include "{}SPIChip.\+h"{}}\newline
{\ttfamily \#include "{}Debug.\+h"{}}\newline
Include dependency graph for MAX22531.\+h\+:
\nopagebreak
\begin{figure}[H]
\begin{center}
\leavevmode
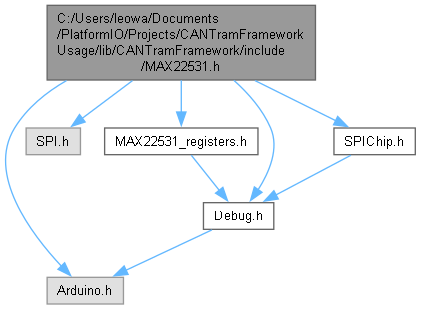
[picture p67: Doxygen/html/d6/d1c/_m_a_x22531_8h__incl.png]

\end{center}
\end{figure}
This graph shows which files directly or indirectly include this file\+:
\nopagebreak
\begin{figure}[H]
\begin{center}
\leavevmode
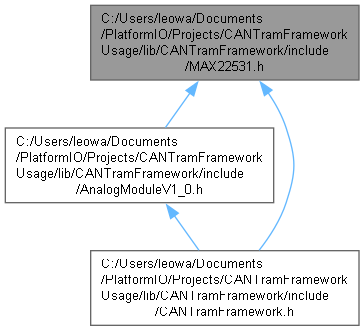
[picture p68: Doxygen/html/d5/d17/_m_a_x22531_8h__dep__incl.png]

\end{center}
\end{figure}
\doxysubsubsection*{Classes}
\begin{DoxyCompactItemize}
\item 
class \mbox{\hyperlink{class_m_a_x22531}{MAX22531}}
\item 
struct \mbox{\hyperlink{struct_m_a_x22531_1_1_burst_response}{MAX22531\+::\+Burst\+Response}}
\end{DoxyCompactItemize}

\doxysubsection{Detailed Description}
\begin{DoxyAuthor}{Author}
your name (\href{mailto:you@domain.com}{\texttt{you@domain.\+com}}) 
\end{DoxyAuthor}
\begin{DoxyVersion}{Version}
0.\+1 
\end{DoxyVersion}
\begin{DoxyDate}{Date}
2025-\/10-\/09
\end{DoxyDate}
\begin{DoxyCopyright}{Copyright}
Copyright (c) 2025 
\end{DoxyCopyright}
