LeoWatti99/CANTram-Framework/Doxygen/latex/d6/d86/_e_s_p32___c_a_n_core_8h_source.tex

\doxysection{ESP32\+\_\+\+CANCore.\+h}
\hypertarget{_e_s_p32___c_a_n_core_8h_source}{}\label{_e_s_p32___c_a_n_core_8h_source}\index{C:/Users/leowa/Documents/PlatformIO/Projects/CANTramFrameworkUsage/lib/CANTramFramework/include/ESP32\_CANCore.h@{C:/Users/leowa/Documents/PlatformIO/Projects/CANTramFrameworkUsage/lib/CANTramFramework/include/ESP32\_CANCore.h}}
\mbox{\hyperlink{_e_s_p32___c_a_n_core_8h}{Go to the documentation of this file.}}
\begin{DoxyCode}{0}
\DoxyCodeLine{00001\ \textcolor{preprocessor}{\#ifndef\ ESP32\_CANCORE\_H}}
\DoxyCodeLine{00002\ \textcolor{preprocessor}{\#define\ ESP32\_CANCORE\_H}}
\DoxyCodeLine{00003\ }
\DoxyCodeLine{00004\ \textcolor{preprocessor}{\#include\ "{}\mbox{\hyperlink{_c_a_n_core_8h}{CANCore.h}}"{}}}
\DoxyCodeLine{00010\ \textcolor{keyword}{class\ }ESP32\_CANCore\ :\ \textcolor{keyword}{public}\ CANCore\ \{}
\DoxyCodeLine{00011\ \textcolor{keyword}{public}:}
\DoxyCodeLine{00012\ \ \ \ \ ESP32\_CANCore()=\textcolor{keywordflow}{default};}
\DoxyCodeLine{00013\ \ \ \ \ \string~ESP32\_CANCore()=\textcolor{keywordflow}{default};}
\DoxyCodeLine{00014\ }
\DoxyCodeLine{00015\ \ \ \ \ \mbox{\hyperlink{class_hardware_resource_adead6978be3d7b86c18e3d3e051381e6}{HardwareResource::Type}}\ \mbox{\hyperlink{class_e_s_p32___c_a_n_core_ac6c187e2a8158cfcc770b568e96706ec}{getType}}()\textcolor{keyword}{\ override\ }\{\ \textcolor{keywordflow}{return}\ \mbox{\hyperlink{class_hardware_resource_adead6978be3d7b86c18e3d3e051381e6a0ae946256af51077cacc3c0a11575635}{HardwareResource::CAN}};\ \}}
\DoxyCodeLine{00016\ \ \ \ \ \textcolor{keywordtype}{bool}\ \mbox{\hyperlink{class_e_s_p32___c_a_n_core_acf383daa8d43b01883d8008dbbb8fc06}{begin}}()\ \textcolor{keyword}{override};}
\DoxyCodeLine{00017\ \ \ \ \ \textcolor{keywordtype}{bool}\ \mbox{\hyperlink{class_e_s_p32___c_a_n_core_ad668c0ff123ec46700546e952dad39d5}{setBaudrate}}(Baudrate\ baudrate)\ \textcolor{keyword}{override};}
\DoxyCodeLine{00018\ \ \ \ \ \textcolor{keywordtype}{bool}\ \mbox{\hyperlink{class_e_s_p32___c_a_n_core_ac11700a4723c67a486fe48ac6d6d66a1}{setPins}}(int8\_t\ txPin,\ int8\_t\ rxPin)\ \textcolor{keyword}{override};}
\DoxyCodeLine{00019\ \ \ \ \ \textcolor{keywordtype}{bool}\ end()\ \textcolor{keyword}{override};}
\DoxyCodeLine{00020\ \ \ \ \ \textcolor{keywordtype}{bool}\ sendMessage(\textcolor{keyword}{const}\ CANMessage\&\ message)\ \textcolor{keyword}{override};}
\DoxyCodeLine{00021\ \ \ \ \ \textcolor{keywordtype}{bool}\ \mbox{\hyperlink{class_e_s_p32___c_a_n_core_adbab7ae89e53ad752bc06e789381c4d5}{readMessage}}(CANMessage\&\ message)\ \textcolor{keyword}{override};}
\DoxyCodeLine{00022\ \ \ \ \ uint8\_t\ \mbox{\hyperlink{class_e_s_p32___c_a_n_core_a82b0d9ba535b47648ac951338794509e}{available}}()\ \textcolor{keyword}{override};}
\DoxyCodeLine{00023\ \ \ \ \ \textcolor{keywordtype}{bool}\ setupFilter(uint32\_t\ \textcolor{keywordtype}{id},\ uint32\_t\ mask)\ \textcolor{keyword}{override};}
\DoxyCodeLine{00024\ \ \ \ \ \textcolor{keywordtype}{bool}\ \mbox{\hyperlink{class_e_s_p32___c_a_n_core_a85a0e3c4965503c96d865bbcc200cd2a}{reset}}()\ \textcolor{keyword}{override};}
\DoxyCodeLine{00025\ }
\DoxyCodeLine{00026\ \textcolor{keyword}{private}:}
\DoxyCodeLine{00027\ \ \ \ \ }
\DoxyCodeLine{00028\ \};}
\DoxyCodeLine{00029\ }
\DoxyCodeLine{00030\ \textcolor{preprocessor}{\#endif}}

\end{DoxyCode}
