LeoWatti99/CANTram-Framework/Doxygen/latex/da/dd4/struct_i_s_o1_i813_t_1_1_diag.tex

\doxysection{ISO1\+I813T\+::Diag Struct Reference}
\hypertarget{struct_i_s_o1_i813_t_1_1_diag}{}\label{struct_i_s_o1_i813_t_1_1_diag}\index{ISO1I813T::Diag@{ISO1I813T::Diag}}
\doxysubsubsection*{Public Attributes}
\begin{DoxyCompactItemize}
\item 
\Hypertarget{struct_i_s_o1_i813_t_1_1_diag_a059f3b2ab0da0afefe33f128f6fe7aef}\label{struct_i_s_o1_i813_t_1_1_diag_a059f3b2ab0da0afefe33f128f6fe7aef} 
uint8\+\_\+t {\bfseries gl\+Err}\+: 8
\item 
\Hypertarget{struct_i_s_o1_i813_t_1_1_diag_a177dfe67ebd20092178c68e44c7aca44}\label{struct_i_s_o1_i813_t_1_1_diag_a177dfe67ebd20092178c68e44c7aca44} 
uint8\+\_\+t {\bfseries int\+Err}\+: 8
\end{DoxyCompactItemize}

The documentation for this struct was generated from the following file\+:\begin{DoxyCompactItemize}
\item 
C\+:/\+Users/leowa/\+Documents/\+Platform\+IO/\+Projects/\+CANTram\+Framework\+Usage/lib/\+CANTram\+Framework/include/ISO1\+I813\+T.\+h\end{DoxyCompactItemize}
