LeoWatti99/CANTram-Framework/Doxygen/latex/da/dfa/_c_a_n_tram_core_8h.tex

\doxysection{C\+:/\+Users/leowa/\+Documents/\+Platform\+IO/\+Projects/\+CANTram\+Framework\+Usage/lib/\+CANTram\+Framework/include/\+CANTram\+Core.h File Reference}
\hypertarget{_c_a_n_tram_core_8h}{}\label{_c_a_n_tram_core_8h}\index{C:/Users/leowa/Documents/PlatformIO/Projects/CANTramFrameworkUsage/lib/CANTramFramework/include/CANTramCore.h@{C:/Users/leowa/Documents/PlatformIO/Projects/CANTramFrameworkUsage/lib/CANTramFramework/include/CANTramCore.h}}

This class serves as the core manager for the CANTram modular system. It handles module attachment, GPIO management, hardware resource allocation and cyclic updates of the modules.  

{\ttfamily \#include $<$Arduino.\+h$>$}\newline
{\ttfamily \#include $<$CANTram\+Module.\+h$>$}\newline
{\ttfamily \#include "{}Output\+Definition.\+h"{}}\newline
{\ttfamily \#include "{}Debug.\+h"{}}\newline
{\ttfamily \#include "{}Hardware\+Resource.\+h"{}}\newline
{\ttfamily \#include "{}CANCore.\+h"{}}\newline
Include dependency graph for CANTram\+Core.\+h\+:
\nopagebreak
\begin{figure}[H]
\begin{center}
\leavevmode
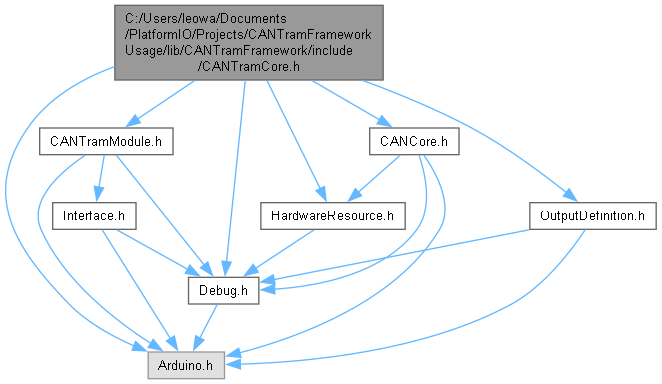
[picture p70: Doxygen/html/df/df6/_c_a_n_tram_core_8h__incl.png]

\end{center}
\end{figure}
This graph shows which files directly or indirectly include this file\+:
\nopagebreak
\begin{figure}[H]
\begin{center}
\leavevmode
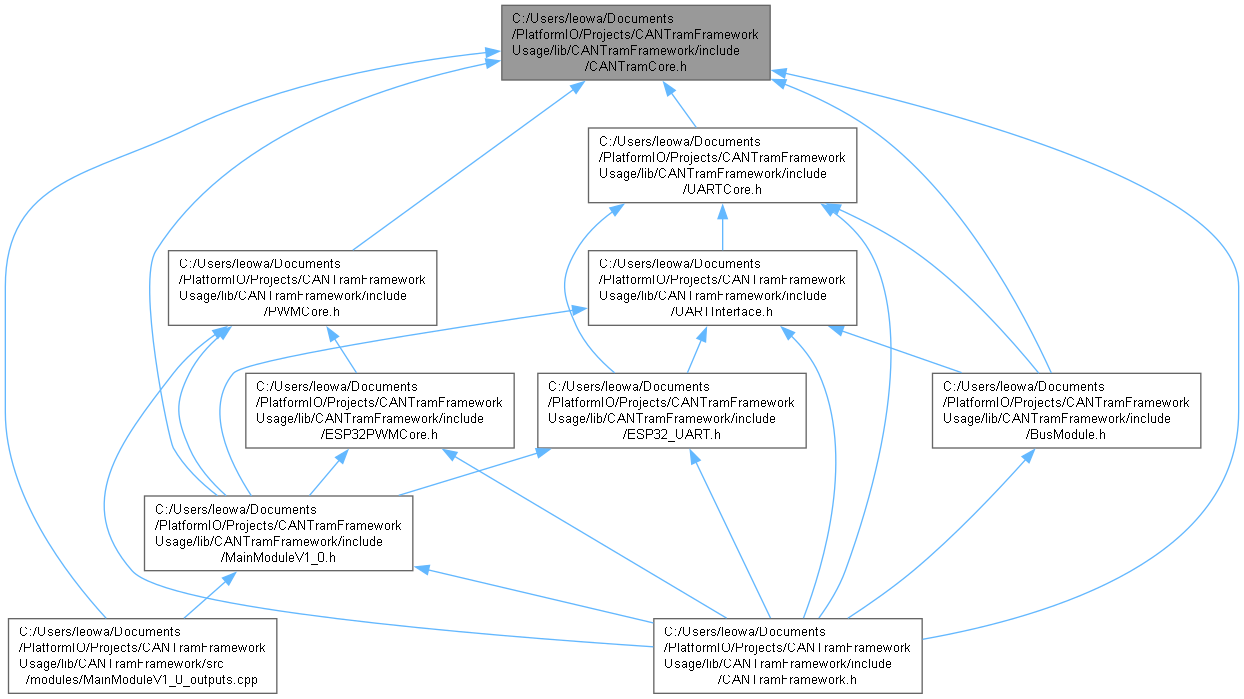
[picture p71: Doxygen/html/d6/db5/_c_a_n_tram_core_8h__dep__incl.png]

\end{center}
\end{figure}
\doxysubsubsection*{Classes}
\begin{DoxyCompactItemize}
\item 
class \mbox{\hyperlink{class_c_a_n_tram_core}{CANTram\+Core}}
\begin{DoxyCompactList}\small\item\em This static class serves as the core manager for the CANTram modular system. It handles module attachment, GPIO management, hardware resource allocation and cyclic updates of the modules. \end{DoxyCompactList}\end{DoxyCompactItemize}
\doxysubsubsection*{Macros}
\begin{DoxyCompactItemize}
\item 
\Hypertarget{_c_a_n_tram_core_8h_a52609a54301c2e1a2521930f8d5079d4}\label{_c_a_n_tram_core_8h_a52609a54301c2e1a2521930f8d5079d4} 
\#define {\bfseries DEFAULT\+\_\+\+REF}~-\/1
\end{DoxyCompactItemize}
\doxysubsubsection*{Typedefs}
\begin{DoxyCompactItemize}
\item 
\Hypertarget{_c_a_n_tram_core_8h_a29bd204b2c9b0a5f8b13e5016e249be3}\label{_c_a_n_tram_core_8h_a29bd204b2c9b0a5f8b13e5016e249be3} 
typedef enum CANTram\+Core\+Error {\bfseries CANTram\+Core\+Error}
\end{DoxyCompactItemize}
\doxysubsubsection*{Enumerations}
\begin{DoxyCompactItemize}
\item 
\Hypertarget{_c_a_n_tram_core_8h_ad958453030fdfa65033b08ccf67ff99d}\label{_c_a_n_tram_core_8h_ad958453030fdfa65033b08ccf67ff99d} 
enum {\bfseries CANTram\+Core\+Error} \{ {\bfseries CAN\+\_\+\+TRAM\+\_\+\+OK}
, {\bfseries MAX\+\_\+\+GPIOS\+\_\+\+EXCEEDED}
, {\bfseries GPIO\+\_\+\+OVERWRITE}
 \}
\end{DoxyCompactItemize}

\doxysubsection{Detailed Description}
This class serves as the core manager for the CANTram modular system. It handles module attachment, GPIO management, hardware resource allocation and cyclic updates of the modules. 

\begin{DoxyAuthor}{Author}
your name (\href{mailto:you@domain.com}{\texttt{you@domain.\+com}}) 
\end{DoxyAuthor}
\begin{DoxyVersion}{Version}
0.\+1 
\end{DoxyVersion}
\begin{DoxyDate}{Date}
2025-\/10-\/09
\end{DoxyDate}
\begin{DoxyCopyright}{Copyright}
Copyright (c) 2025 
\end{DoxyCopyright}
