LeoWatti99/CANTram-Framework/Doxygen/latex/de/d85/class_analog_input.tex

\doxysection{Analog\+Input Class Reference}
\hypertarget{class_analog_input}{}\label{class_analog_input}\index{AnalogInput@{AnalogInput}}

Inheritance diagram for Analog\+Input\+:
\nopagebreak
\begin{figure}[H]
\begin{center}
\leavevmode

\end{center}
\end{figure}

Collaboration diagram for Analog\+Input\+:
\nopagebreak
\begin{figure}[H]
\begin{center}
\leavevmode

\end{center}
\end{figure}
\doxysubsubsection*{Public Member Functions}
\begin{DoxyCompactItemize}
\item 
Interface\+::\+Type \mbox{\hyperlink{class_analog_input_a08148a989fd9dfb1262cd66aa8c09b48}{get\+Type}} () const override
\item 
\Hypertarget{class_analog_input_a75692e98fc7fca0515bc35489ba10052}\label{class_analog_input_a75692e98fc7fca0515bc35489ba10052} 
{\bfseries Analog\+Input} (Interface\+::\+Resolution res=Interface\+::\+RES\+\_\+12\+BIT)
\item 
\Hypertarget{class_analog_input_a9a824b5daea5fec2ce294d5adad1fd12}\label{class_analog_input_a9a824b5daea5fec2ce294d5adad1fd12} 
Interface\+::\+Resolution {\bfseries get\+Resolution} () const
\item 
void \mbox{\hyperlink{class_analog_input_abe29cdd511d17f21f402ecfc71ce1937}{setQ}} (uint16\+\_\+t q) override
\end{DoxyCompactItemize}
\doxysubsection*{Public Member Functions inherited from \mbox{\hyperlink{class_interface}{Interface}}}
\begin{DoxyCompactItemize}
\item 
virtual uint16\+\_\+t {\bfseries getQ} () const
\item 
void {\bfseries rename} (const String \&new\+Name)
\item 
{\footnotesize template$<$typename T$>$ }\\T {\bfseries as} ()
\item 
void {\bfseries validate} ()
\item 
void {\bfseries validate} (bool state)
\item 
void {\bfseries invalidate} ()
\item 
bool {\bfseries is\+Valid} ()
\item 
bool {\bfseries is\+Invalid} ()
\item 
String {\bfseries get\+Name} () const
\end{DoxyCompactItemize}
\doxysubsubsection*{Additional Inherited Members}
\doxysubsection*{Public Types inherited from \mbox{\hyperlink{class_interface}{Interface}}}
\begin{DoxyCompactItemize}
\item 
\Hypertarget{class_interface_a765c7b30069d200e461995c602b98e90}\label{class_interface_a765c7b30069d200e461995c602b98e90} 
enum {\bfseries Resolution} \{ {\bfseries RES\+\_\+8\+BIT} = 8
, {\bfseries RES\+\_\+10\+BIT} = 10
, {\bfseries RES\+\_\+12\+BIT} = 12
, {\bfseries RES\+\_\+16\+BIT} = 16
 \}
\item 
\Hypertarget{class_interface_a01562cbfcb9c8793a7117b67ee0ce079}\label{class_interface_a01562cbfcb9c8793a7117b67ee0ce079} 
enum {\bfseries Type} \{ \newline
{\bfseries DIGITAL\+\_\+\+INPUT}
, {\bfseries DIGITAL\+\_\+\+OUTPUT}
, {\bfseries ANALOG\+\_\+\+INPUT}
, {\bfseries ANALOG\+\_\+\+OUTPUT}
, \newline
{\bfseries RELAIS}
, {\bfseries BUS}
 \}
\end{DoxyCompactItemize}
\doxysubsection*{Protected Attributes inherited from \mbox{\hyperlink{class_interface}{Interface}}}
\begin{DoxyCompactItemize}
\item 
String {\bfseries name}
\item 
uint16\+\_\+t {\bfseries Q} = 0
\item 
bool {\bfseries \+\_\+valid} = false
\item 
bool {\bfseries \+\_\+invalid} = false
\end{DoxyCompactItemize}

\label{doc-func-members}
\Hypertarget{class_analog_input_doc-func-members}
\doxysubsection{Member Function Documentation}
\Hypertarget{class_analog_input_a08148a989fd9dfb1262cd66aa8c09b48}\index{AnalogInput@{AnalogInput}!getType@{getType}}
\index{getType@{getType}!AnalogInput@{AnalogInput}}
\doxysubsubsection{\texorpdfstring{getType()}{getType()}}
{\footnotesize\ttfamily \label{class_analog_input_a08148a989fd9dfb1262cd66aa8c09b48} 
Interface\+::\+Type Analog\+Input\+::get\+Type (\begin{DoxyParamCaption}{}{}\end{DoxyParamCaption}) const\hspace{0.3cm}{\ttfamily [inline]}, {\ttfamily [override]}, {\ttfamily [virtual]}}

Implements \mbox{\hyperlink{class_interface}{Interface}}.

\Hypertarget{class_analog_input_abe29cdd511d17f21f402ecfc71ce1937}\index{AnalogInput@{AnalogInput}!setQ@{setQ}}
\index{setQ@{setQ}!AnalogInput@{AnalogInput}}
\doxysubsubsection{\texorpdfstring{setQ()}{setQ()}}
{\footnotesize\ttfamily \label{class_analog_input_abe29cdd511d17f21f402ecfc71ce1937} 
void Analog\+Input\+::setQ (\begin{DoxyParamCaption}\item[{uint16\+\_\+t}]{q}{}\end{DoxyParamCaption})\hspace{0.3cm}{\ttfamily [inline]}, {\ttfamily [override]}, {\ttfamily [virtual]}}

Reimplemented from \mbox{\hyperlink{class_interface}{Interface}}.

The documentation for this class was generated from the following file\+:\begin{DoxyCompactItemize}
\item 
C\+:/\+Users/leowa/\+Documents/\+Platform\+IO/\+Projects/\+CANTram\+Framework\+Usage/lib/\+CANTram\+Framework/include/Analog\+Input.\+h\end{DoxyCompactItemize}
