LeoWatti99/CANTram-Framework/Doxygen/html/d6/de8/class_interface__inherit__graph.png

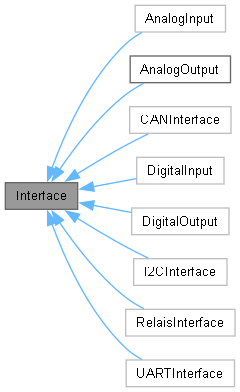
Doxygen/html/d6/de8/class_interface__inherit__graph.png
