LeoWatti99/CANTram-Framework/Doxygen/html/dir_1dc3a360bf8ff24b56ad551b9646cfab_dep.png

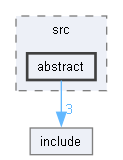
Doxygen/html/dir_1dc3a360bf8ff24b56ad551b9646cfab_dep.png
