LeoWatti99/CANTram-Framework/Doxygen/html/dir_2d0db17db0a6f9057ce0cf6d8f9de176_dep.png

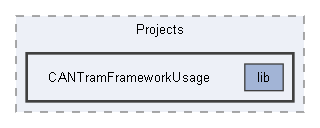
Doxygen/html/dir_2d0db17db0a6f9057ce0cf6d8f9de176_dep.png
