LeoWatti99/CANTram-Framework/Doxygen/html/dir_3a77c7b9c003c01907afb7a998b1291a_dep.png

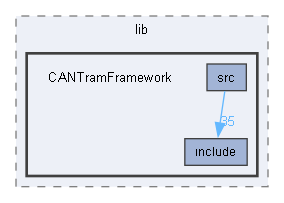
Doxygen/html/dir_3a77c7b9c003c01907afb7a998b1291a_dep.png
