LeoWatti99/CANTram-Framework/Doxygen/html/dir_7d12d5f7a9955c6a59fc801c366f40b1_dep.png

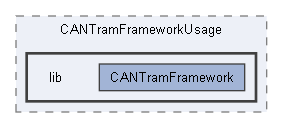
Doxygen/html/dir_7d12d5f7a9955c6a59fc801c366f40b1_dep.png
