LeoWatti99/CANTram-Framework/Doxygen/html/dir_8b48734224263429bd0d6b0d355c2336_dep.png

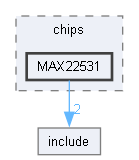
Doxygen/html/dir_8b48734224263429bd0d6b0d355c2336_dep.png
