LeoWatti99/CANTram-Framework/Doxygen/html/dir_55f47262bee62bb311e796def9f889db_dep.png

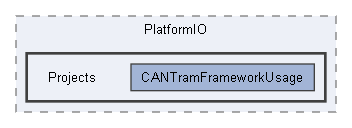
Doxygen/html/dir_55f47262bee62bb311e796def9f889db_dep.png
