LeoWatti99/CANTram-Framework/Doxygen/html/dir_819fe840eebfce18e24459706ba68ca1_dep.png

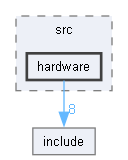
Doxygen/html/dir_819fe840eebfce18e24459706ba68ca1_dep.png
