LeoWatti99/CANTram-Framework/Doxygen/html/dir_912c2da2dd1284570bbe81b0089607c5_dep.png

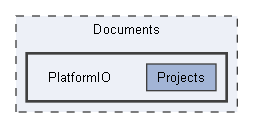
Doxygen/html/dir_912c2da2dd1284570bbe81b0089607c5_dep.png
