LeoWatti99/CANTram-Framework/Doxygen/html/dir_1195d29507b2dd21ee2dbd22a5030bfa_dep.png

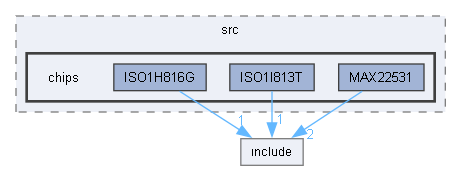
Doxygen/html/dir_1195d29507b2dd21ee2dbd22a5030bfa_dep.png
