LeoWatti99/CANTram-Framework/Doxygen/html/dir_e85346bbe02bd534ab3150c7adcff439_dep.png

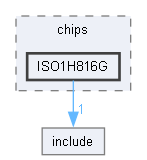
Doxygen/html/dir_e85346bbe02bd534ab3150c7adcff439_dep.png
