LeoWatti99/CANTram-Framework/Doxygen/html/dir_f696ed459fdc8990bd9e98041fbd2fdc_dep.png

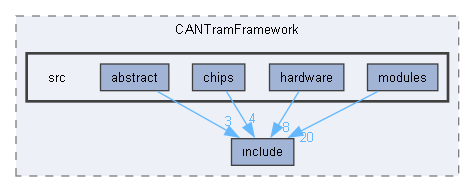
Doxygen/html/dir_f696ed459fdc8990bd9e98041fbd2fdc_dep.png
