LeoWatti99/CANTram-Framework/Doxygen/html/inherit_graph_2.png

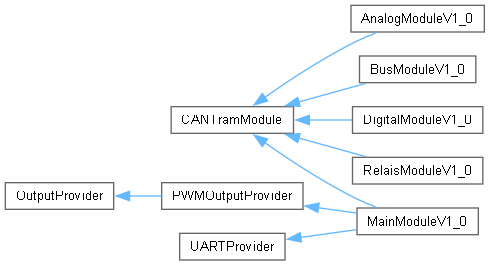
Doxygen/html/inherit_graph_2.png
