LeoWatti99/CANTram-Framework/Doxygen/html/inherit_graph_3.png

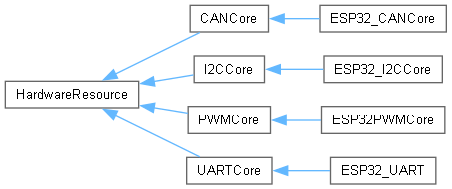
Doxygen/html/inherit_graph_3.png
