LeoWatti99/CANTram-Framework/Doxygen/html/inherit_graph_9.png

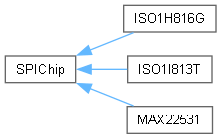
Doxygen/html/inherit_graph_9.png
