LeoWatti99/CANTram-Framework/Doxygen/latex/d0/ddd/_c_a_n_core_8h__dep__incl.pdf

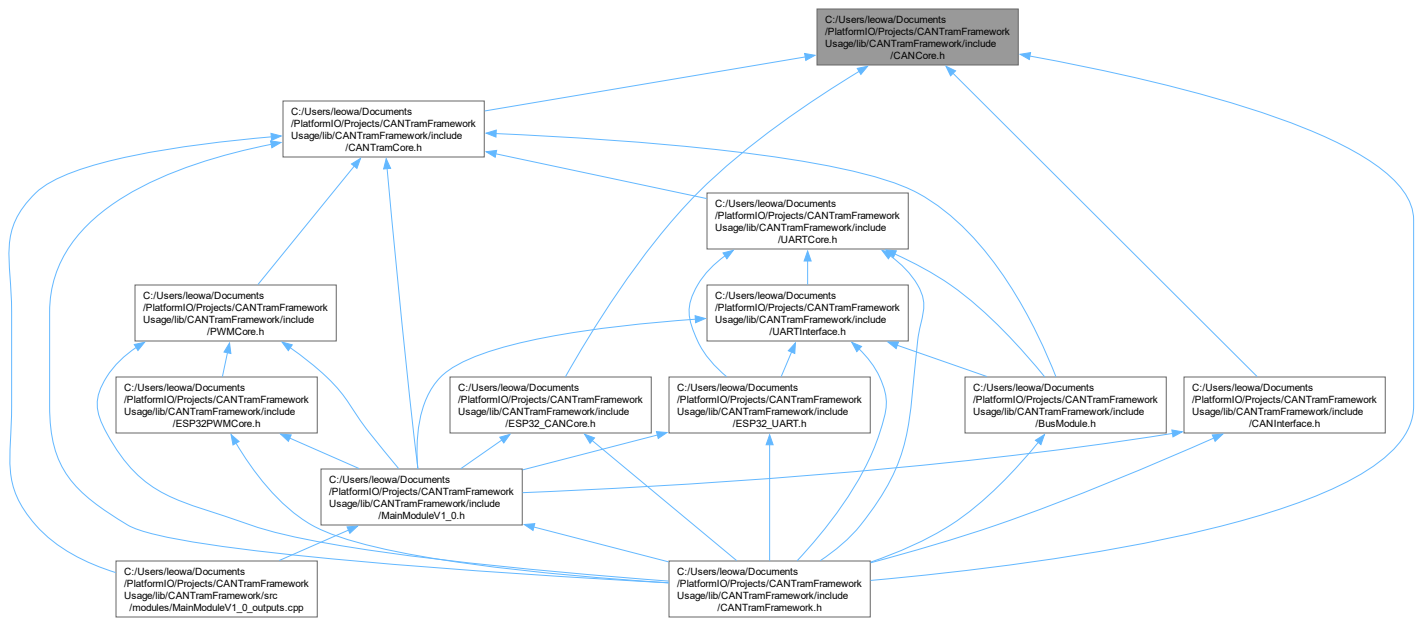
[picture p93: page 1]
/CANCore.h; /CANInterface.h; /CANTramFramework.h; /CANTramCore.h; /ESP32_CANCore.h; /MainModuleV1_0.h; /BusModule.h; /PWMCore.h; /UARTCore.h; /ESP32PWMCore.h; /ESP32_UART.h; /UARTInterface.h

C:/Users/leowa/Documents
/PlatformIO/Projects/CANTramFramework
Usage/lib/CANTramFramework/include

Usage/lib/CANTramFramework/src
/modules/MainModuleV1_0_outputs.cpp
