LeoWatti99/CANTram-Framework/Doxygen/latex/d1/db5/_u_a_r_t_core_8h__incl.pdf

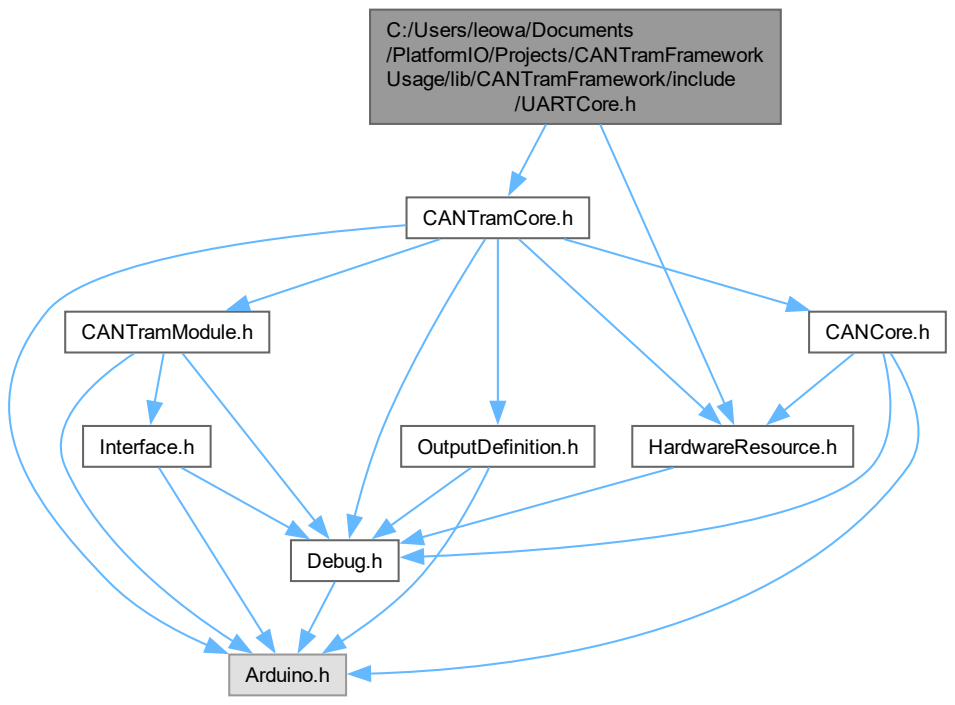
[picture p94: page 1]
/UARTCore.h; CANTramCore.h; HardwareResource.h; Arduino.h; CANTramModule.h; Debug.h; OutputDefinition.h; CANCore.h; Interface.h

C:/Users/leowa/Documents
/PlatformIO/Projects/CANTramFramework
Usage/lib/CANTramFramework/include
