LeoWatti99/CANTram-Framework/Doxygen/latex/d3/dc5/_main_module_v1__0__outputs_8cpp__incl.pdf

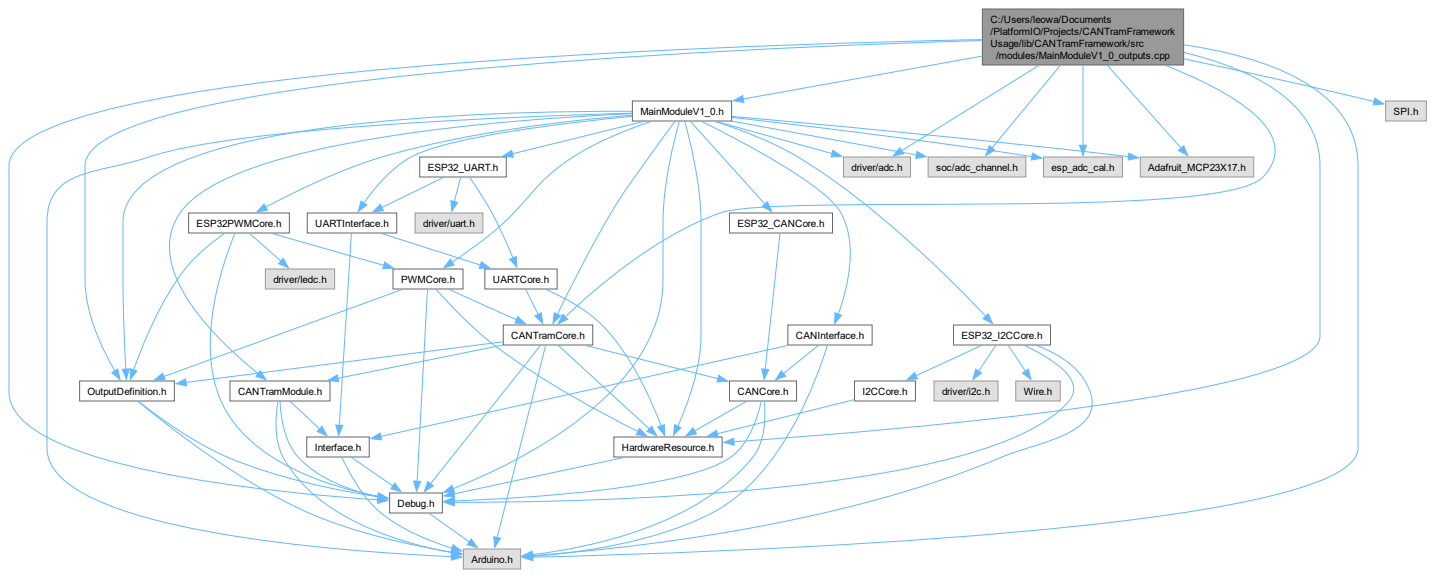
[picture p95: page 1]
MainModuleV1_0.h; Arduino.h; Debug.h; CANTramCore.h; OutputDefinition.h; HardwareResource.h; driver/adc.h; soc/adc_channel.h; esp_adc_cal.h; Adafruit_MCP23X17.h; SPI.h; CANTramModule.h; PWMCore.h; ESP32PWMCore.h; ESP32_UART.h; UARTInterface.h; ESP32_CANCore.h; CANInterface.h; ESP32_I2CCore.h; Interface.h; CANCore.h; driver/ledc.h; driver/uart.h; UARTCore.h; I2CCore.h; driver/i2c.h; Wire.h

C:/Users/leowa/Documents
/PlatformIO/Projects/CANTramFramework
Usage/lib/CANTramFramework/src
/modules/MainModuleV1_0_outputs.cpp
