LeoWatti99/CANTram-Framework/Doxygen/latex/d4/d8c/_output_definition_8h__dep__incl.pdf

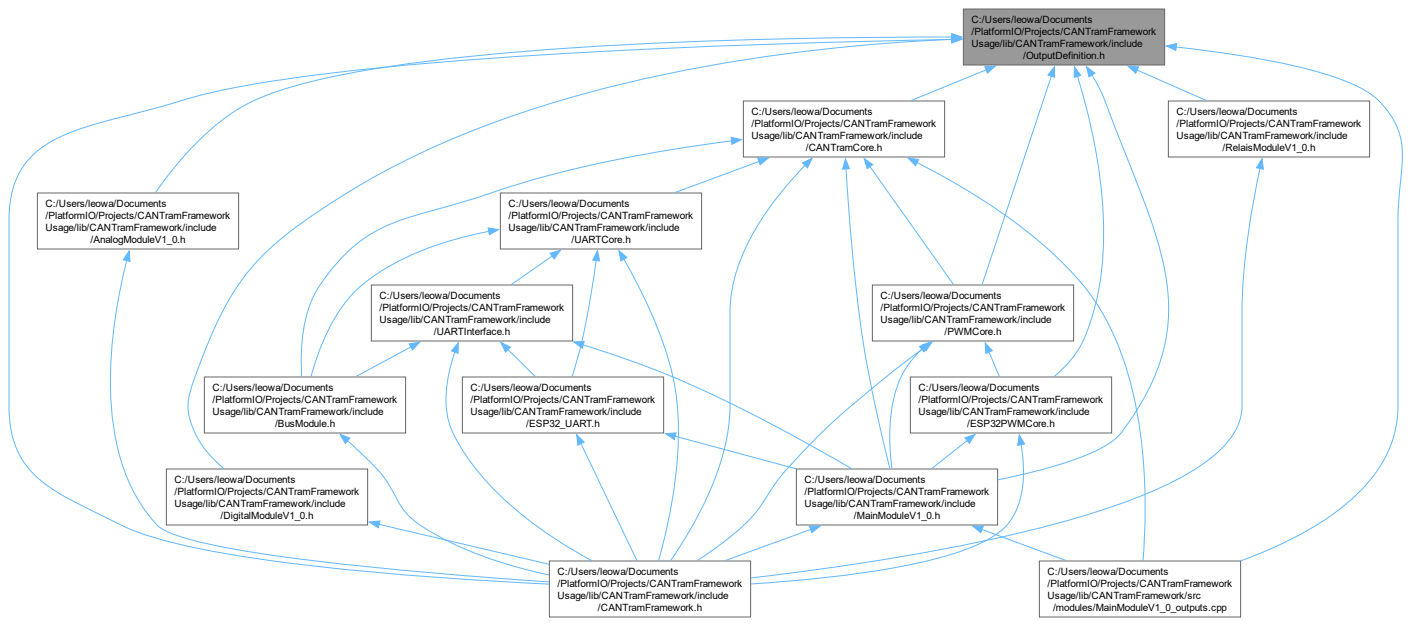
[picture p96: page 1]
/OutputDefinition.h; /AnalogModuleV1_0.h; /CANTramFramework.h; /CANTramCore.h; /MainModuleV1_0.h; /PWMCore.h; /ESP32PWMCore.h; /DigitalModuleV1_0.h; /RelaisModuleV1_0.h; /BusModule.h; /UARTCore.h; /ESP32_UART.h; /UARTInterface.h

C:/Users/leowa/Documents
/PlatformIO/Projects/CANTramFramework
Usage/lib/CANTramFramework/include

Usage/lib/CANTramFramework/src
/modules/MainModuleV1_0_outputs.cpp
