LeoWatti99/CANTram-Framework/KiCad Schaltungen/Digital Output Prototyp V2/Layout_Proto_DQ.pdf

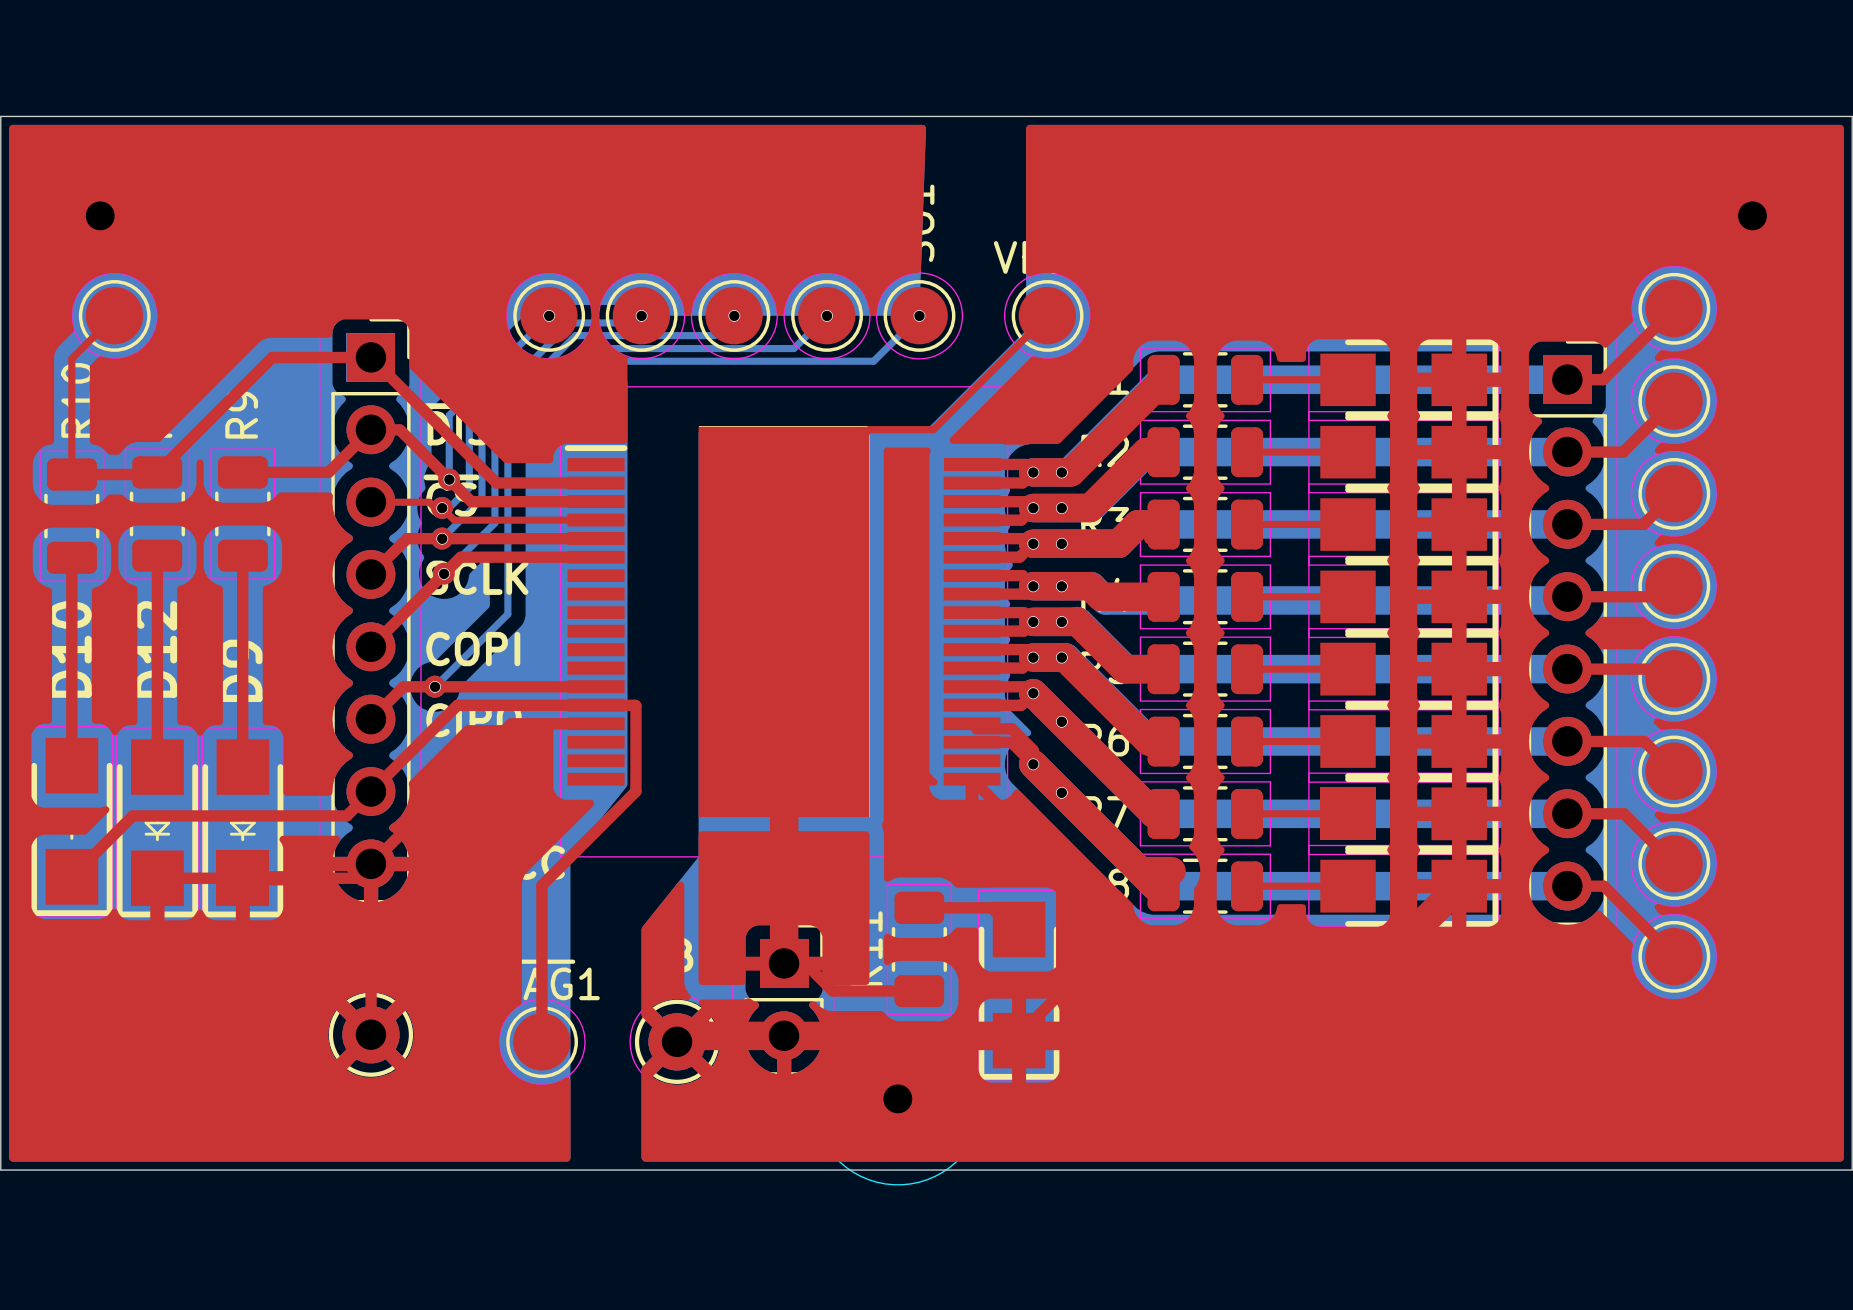
[picture p97: page 1]
