LeoWatti99/CANTram-Framework/KiCad Schaltungen/Analog Output Prototyp/Analog Output Prototyp/Analog Output Prototyp.kicad_pcb

## KiCad design KiCad Schaltungen/Analog Output Prototyp/Analog Output Prototyp/Analog Output Prototyp.kicad_pcb (2026-01-24)

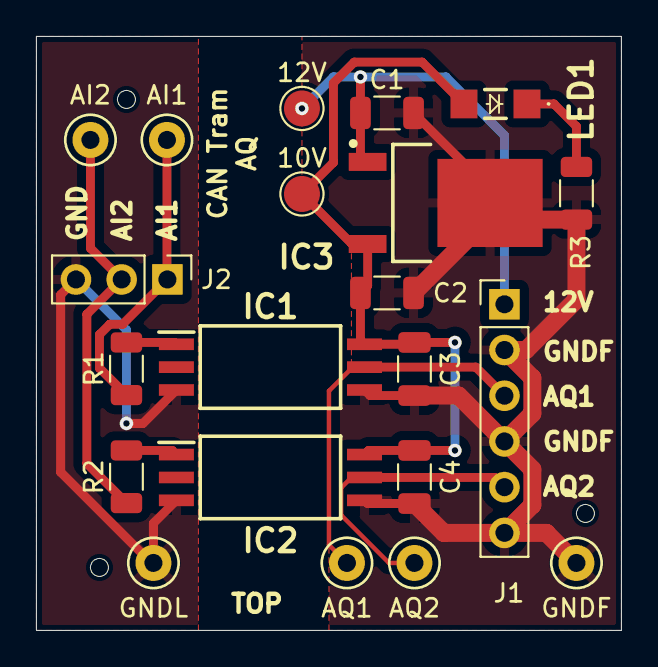
[picture p121: board Analog Output Prototyp.kicad_pcb from above]

Board: 2 copper layers, 32.5 x 33.0 mm, 21 parts (0 on the bottom side), 11 nets.

Parts:
10V, 12V: TestPoint; TestPoint_Pad_D2.0mm
AI1, AI2: TestPoint_Probe; TestPoint_Keystone_5000-5004_Miniature
AQ1, AQ2: TestPoint_Probe; TestPoint_Keystone_5000-5004_Miniature
C1: 330n; C_1206_3216Metric
C2, C3, C4: 100n; C_1206_3216Metric
GNDF: TestPoint_Probe; TestPoint_Keystone_5000-5004_Miniature
GNDL: TestPoint_Probe; TestPoint_Keystone_5000-5004_Miniature
IC1, IC2: SI8261BAD-C-ISR; SOIC127P1150X265-6N
IC3: L78M10ABDT-TR; TO228P972X240-3N
J1: Conn_01x06; PinHeader_1x06_P2.54mm_Vertical
J2: Conn_01x03; PinHeader_1x03_P2.54mm_Vertical
LED1: 156120GS75000
R1, R2: 100; R_1206_3216Metric
R3: 6,2k; R_1206_3216Metric

Connections:
+10V: 10V.1, C2.1, C3.2, C4.2, IC1.6 (VDD), IC2.6 (VDD), IC3.3 (OUTPUT), LED1.2 (A)
+12V: 12V.1, C1.1, IC3.1 (INPUT), J1.1
GNDF: C1.2, C2.2, C3.1, C4.1, GNDF.1, IC1.4 (GND), IC2.4 (GND), IC3.4 (GND_(TAB)), J1.2, J1.4, J1.6, R3.2
GNDL: GNDL.1, IC1.3 (CATHODE), IC2.3 (CATHODE), J2.3
unnamed: IC1.1 (ANODE), R1.2
unnamed: AQ1.1, IC1.5 (VO), J1.3
unnamed: IC2.1 (ANODE), R2.2
unnamed: AQ2.1, IC2.5 (VO), J1.5
unnamed: AI1.1, J2.1, R1.1
unnamed: AI2.1, J2.2, R2.1
unnamed: LED1.1 (K), R3.1
