LeoWatti99/CANTram-Framework/KiCad Schaltungen/Hauptmodul/Hauptmodul.kicad_pcb

## KiCad design KiCad Schaltungen/Hauptmodul/Hauptmodul.kicad_pcb (2026-01-24)

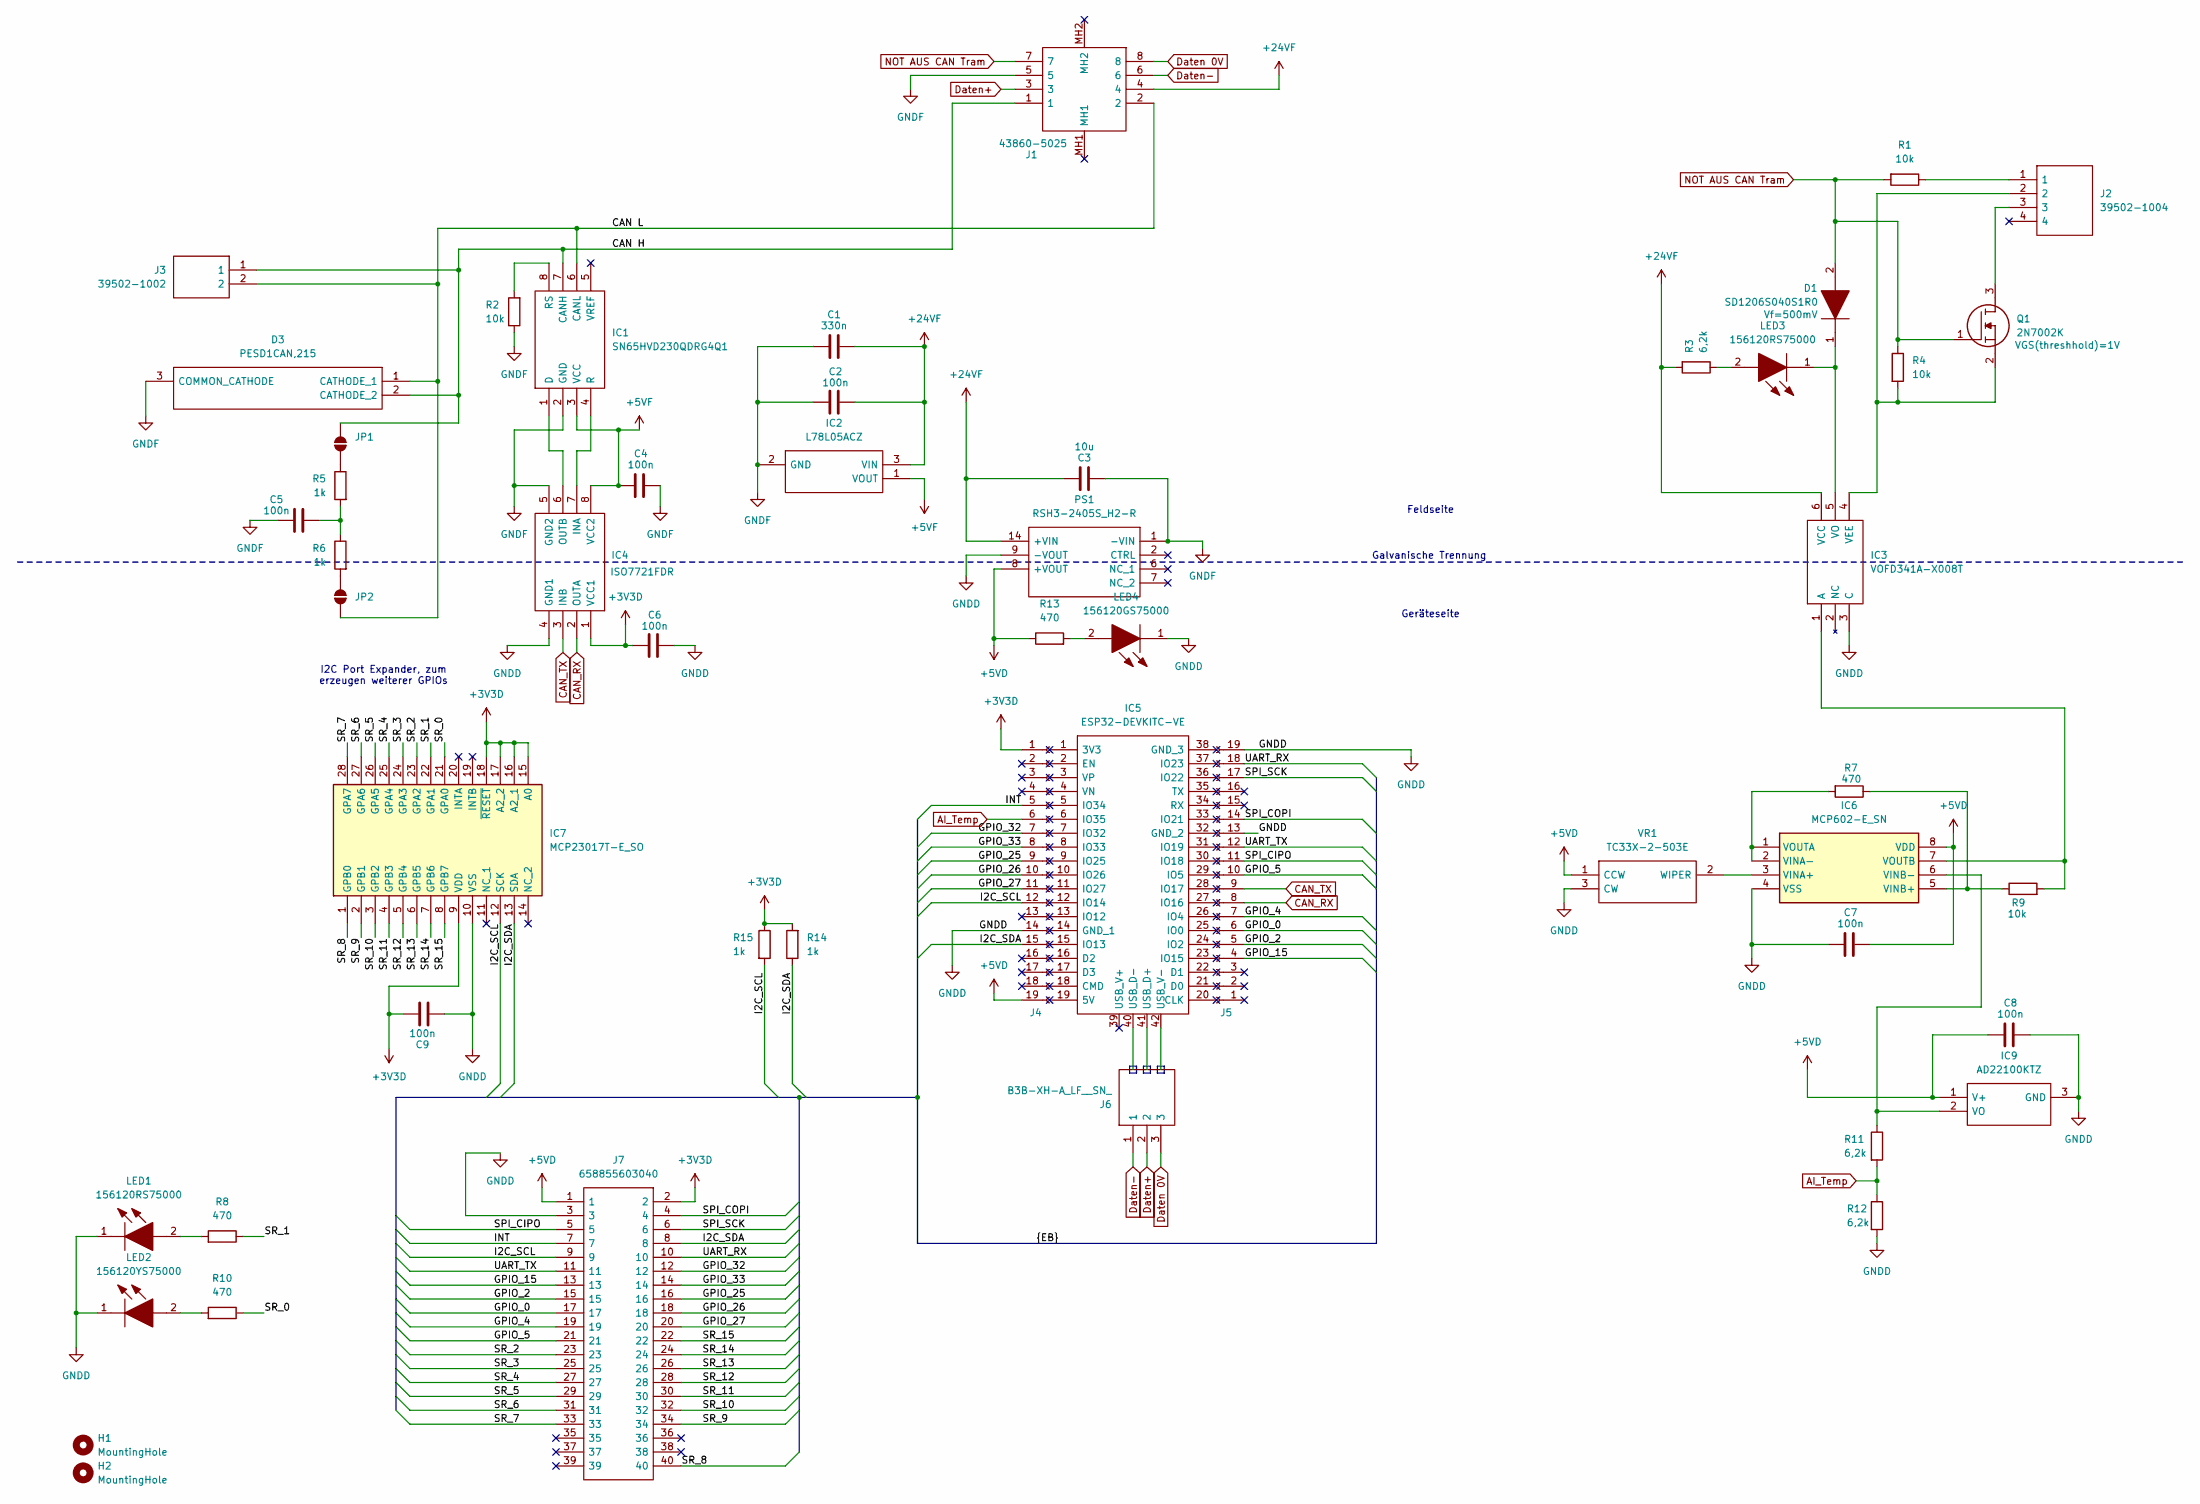
[picture p122: schematic Hauptmodul.kicad_sch, CAN Tram Controller Hauptmodul]

Parts:
C1: 330n; C_1206_3216Metric; Manufacturer_Part_Number CL31A106KBHNNNE; Mouser Part Number 187-CL31A106KBHNNNE
C2, C4, C5, C6, C7, C8, C9: 100n; C_1206_3216Metric; Manufacturer_Part_Number CL31A106KBHNNNE; Mouser Part Number 187-CL31A106KBHNNNE
C3: 10u; C_1206_3216Metric; Manufacturer_Part_Number CL31A106KBHNNNE; Mouser Part Number 187-CL31A106KBHNNNE
D1: SD1206S040S1R0; DIOC3419X116N; Mouser Part Number 581-SD1206S040S1R0
D3: PESD1CAN,215; SOT95P230X110-3N; Mouser Part Number 771-PESD1CAN-T/R
H1, H2: MountingHole; MountingHole_3.2mm_M3
IC1: SN65HVD230QDRG4Q1; SOIC127P600X175-8N; Mouser Part Number 595-S65HVD230QDRG4Q1
IC2: L78L05ACZ; Mouser Part Number 511-L78L05ACZ
IC3: VOFD341A-X008T; SOIC127P1150X378-6N; Mouser Part Number 625-VOFD341A-X008T
IC4: ISO7721FDR; SOIC127P600X175-8N; Mouser Part Number 595-ISO7721FDR
IC5: ESP32-DEVKITC-VE; ESP32DEVKITCVE; Manufacturer_Part_Number ESP32-DEVKITC-VE; Mouser Part Number 356-ESP32-DEVKTC32VE
IC6: MCP602-E_SN; SOIC127P600X175-8N; Mouser Part Number 579-MCP602-E/SN
IC7: MCP23017T-E_SO; SOIC127P1030X265-28N; Mouser Part Number 579-MCP23017T-E/SO
IC9: AD22100KTZ; TO128P419X483X533-3P; Mouser Part Number 584-AD22100KTZ
J1: 43860-5025; 438605025; Mouser Part Number 538-43860-5025
J2: 39502-1004; SHDRRA4W80P0X350_1X4_1540X920X730P; Mouser Part Number 538-39502-1004
J3: 39502-1002; SHDR2W80P0X350_1X2_840X920X690P; Mouser Part Number 538-39502-1002
J4, J5: Conn_01x19_Socket; PinSocket_1x19_P2.54mm_Vertical
J6: B3B-XH-A_LF__SN_; B3BXHALFSN; Mouser Part Number 306-B3BXHALFSNP
J7: 658855603040; Mouser Part Number 710-658855603040
JP1, JP2: SolderJumper_2_Open; SolderJumper-2_P1.3mm_Open_Pad1.0x1.5mm
LED1, LED3: 156120RS75000; LEDM3216X130N; Mouser Part Number 710-156120RS75000
LED2: 156120YS75000; LEDC5017X140N; Mouser Part Number 710-156120YS75000
LED4: 156120GS75000; Mouser Part Number 710-156120GS75000
PS1: RSH3-2405S_H2-R; RSH32405SH2R; Mouser Part Number 919-RSH3-2405S/H2-R
Q1: 2N7002K; SOT95P240X120-3N; Mouser Part Number 512-2N7002K
R1, R4: 10k; R_1206_3216Metric; Manufacturer_Part_Number AC1206FR-076K2L; Mouser Part Number 603-AC1206FR-076K2L
R2: 10k; R_1206_3216Metric; Manufacturer_Part_Number RC1206FR-1310KL; Mouser Part Number 603-RC1206FR-1310KL
R3, R11: 6,2k; R_1206_3216Metric; Manufacturer_Part_Number AC1206FR-076K2L; Mouser Part Number 603-AC1206FR-076K2L
R5, R6: 1k; R_1206_3216Metric
R7: 470; R_1206_3216Metric; Manufacturer_Part_Number RC1206FR-0712KL; Mouser Part Number 603-RC1206FR-0712KL
R8, R10: 470; R_1206_3216Metric
R9: 10k; R_1206_3216Metric; Manufacturer_Part_Number RC1206FR-0712KL; Mouser Part Number 603-RC1206FR-0712KL
R12: 6,2k; R_1206_3216Metric; Manufacturer_Part_Number RC1206FR-0712KL; Mouser Part Number 603-RC1206FR-0712KL
R13: 470; R_1206_3216Metric; Manufacturer_Part_Number AC1206FR-076K2L; Mouser Part Number 603-AC1206FR-076K2L
R14, R15: 1k; R_1206_3216Metric; Manufacturer_Part_Number AC1206FR-076K2L; Mouser Part Number 603-AC1206FR-076K2L
VR1: TC33X-2-503E; TC33X2503E; Mouser Part Number 652-TC33X-2-503E

Connections:
+3V3D: C6.2, C9.2, IC4.1 (VCC1), IC7.9 (VDD), IC7.15 (A0), IC7.16 (A2_1), IC7.17 (A2_2), IC7.18 (~RESET), J4.1, J7.2, R14.2, R15.1
+5VD: C7.1, C8.2, IC6.8 (VDD), IC9.1 (V+), J4.19, J7.1, PS1.8 (+VOUT), R13.1, VR1.1 (CCW)
+5VF: C4.2, IC1.3 (VCC), IC2.1 (VOUT), IC4.8 (VCC2)
+24VF: C1.2, C2.2, C3.1, IC2.3 (VIN), IC3.6 (VCC), J1.4, PS1.14 (+VIN), R3.2
/CAN H: D3.2 (CATHODE_2), IC1.7 (CANH), J1.1, J3.1, JP1.2 (B)
/CAN L: D3.1 (CATHODE_1), IC1.6 (CANL), J1.2, J3.2, JP2.2 (B)
/GPIO_0: J5.6, J7.17
/GPIO_2: J5.5, J7.15
/GPIO_4: J5.7, J7.19
/GPIO_5: J5.10, J7.21
/GPIO_15: J5.4, J7.13
/GPIO_25: J4.9, J7.16
/GPIO_26: J4.10, J7.18
/GPIO_27: J4.11, J7.20
/GPIO_32: J4.7, J7.12
/GPIO_33: J4.8, J7.14
/I2C_SCL: IC7.12 (SCK), J4.12, J7.9, R15.2
/I2C_SDA: IC7.13 (SDA), J4.15, J7.8, R14.1
/INT: J4.5, J7.7
/SPI_CIPO: J5.11, J7.5
/SPI_COPI: J5.14, J7.4
/SPI_SCK: J5.17, J7.6
/SR_0: IC7.21 (GPA0), R10.1
/SR_1: IC7.22 (GPA1), R8.1
/SR_2: IC7.23 (GPA2), J7.23
/SR_3: IC7.24 (GPA3), J7.25
/SR_4: IC7.25 (GPA4), J7.27
/SR_5: IC7.26 (GPA5), J7.29
/SR_6: IC7.27 (GPA6), J7.31
/SR_7: IC7.28 (GPA7), J7.33
/SR_8: IC7.1 (GPB0), J7.40
/SR_9: IC7.2 (GPB1), J7.34
/SR_10: IC7.3 (GPB2), J7.32
/SR_11: IC7.4 (GPB3), J7.30
/SR_12: IC7.5 (GPB4), J7.28
/SR_13: IC7.6 (GPB5), J7.26
/SR_14: IC7.7 (GPB6), J7.24
/SR_15: IC7.8 (GPB7), J7.22
/UART_RX: J5.18, J7.10
/UART_TX: J5.12, J7.11
AI_Temp: J4.6, R11.2, R12.1
CAN_RX: IC4.2 (OUTA), J5.8
CAN_TX: IC4.3 (INB), J5.9
Daten 0V: J1.8, J6.3
Daten+: J1.3, J6.2
Daten-: J1.6, J6.1
GNDD: C6.1, C7.2, C8.1, C9.1, IC3.3 (C), IC4.4 (GND1), IC6.4 (VSS), IC7.10 (VSS), IC9.3 (GND), J4.14, J5.13, J5.19, J7.3, LED1.1, LED2.1, LED4.1, PS1.9 (-VOUT), R12.2, VR1.3 (CW)
GNDF: C1.1, C2.1, C3.2, C4.1, C5.2, D3.3 (COMMON_CATHODE), IC1.2 (GND), IC2.2 (GND), IC4.5 (GND2), J1.5, PS1.1 (-VIN), R2.1
NOT AUS CAN Tram: D1.2, J1.7, Q1.1, R1.2, R4.1
unnamed: C5.1, R5.2, R6.1
unnamed: IC1.1 (D), IC4.6 (OUTB)
unnamed: IC1.4 (R), IC4.7 (INA)
unnamed: IC1.8 (RS), R2.2
unnamed: IC3.1 (A), IC6.7 (VOUTB), R9.2
unnamed: IC3.4 (VEE), J2.2, Q1.2, R4.2
unnamed: D1.1, IC3.5 (VO), LED3.1
unnamed: IC6.3 (VINA+), VR1.2 (WIPER)
unnamed: IC6.1 (VOUTA), IC6.2 (VINA-), R7.2
unnamed: IC6.5 (VINB+), R7.1, R9.1
unnamed: IC6.6 (VINB-), IC9.2 (VO), R11.1
unnamed: J2.1, R1.1
unnamed: J2.3, Q1.3
unnamed: JP1.1 (A), R5.1
unnamed: JP2.1 (A), R6.2
unnamed: LED1.2, R8.2
unnamed: LED2.2, R10.2
unnamed: LED3.2, R3.1
unnamed: LED4.2, R13.2

Notes on the sheet:
Galvanische Trennung
Geräteseite
Feldseite
I2C Port Expander, zum erzeugen weiterer GPIOs

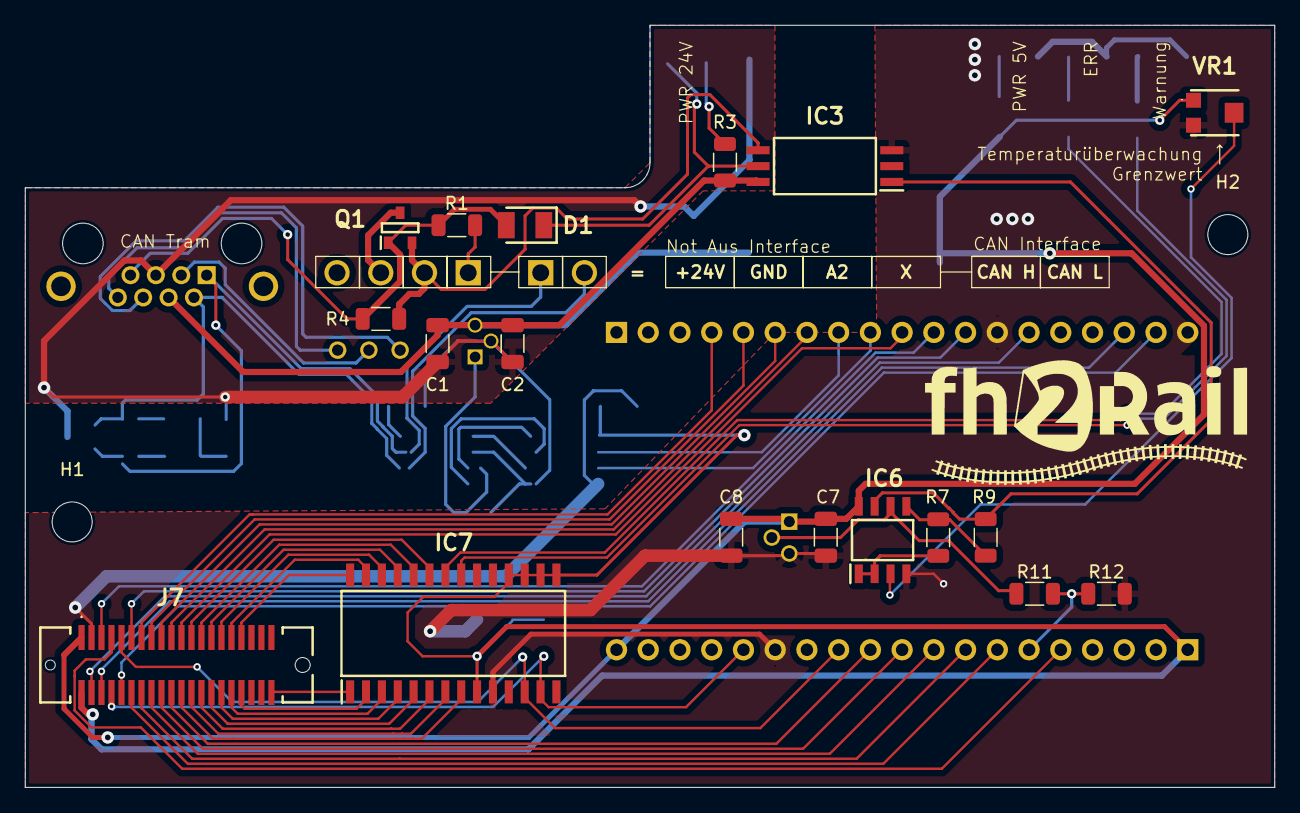
[picture p123: board Hauptmodul.kicad_pcb from above]

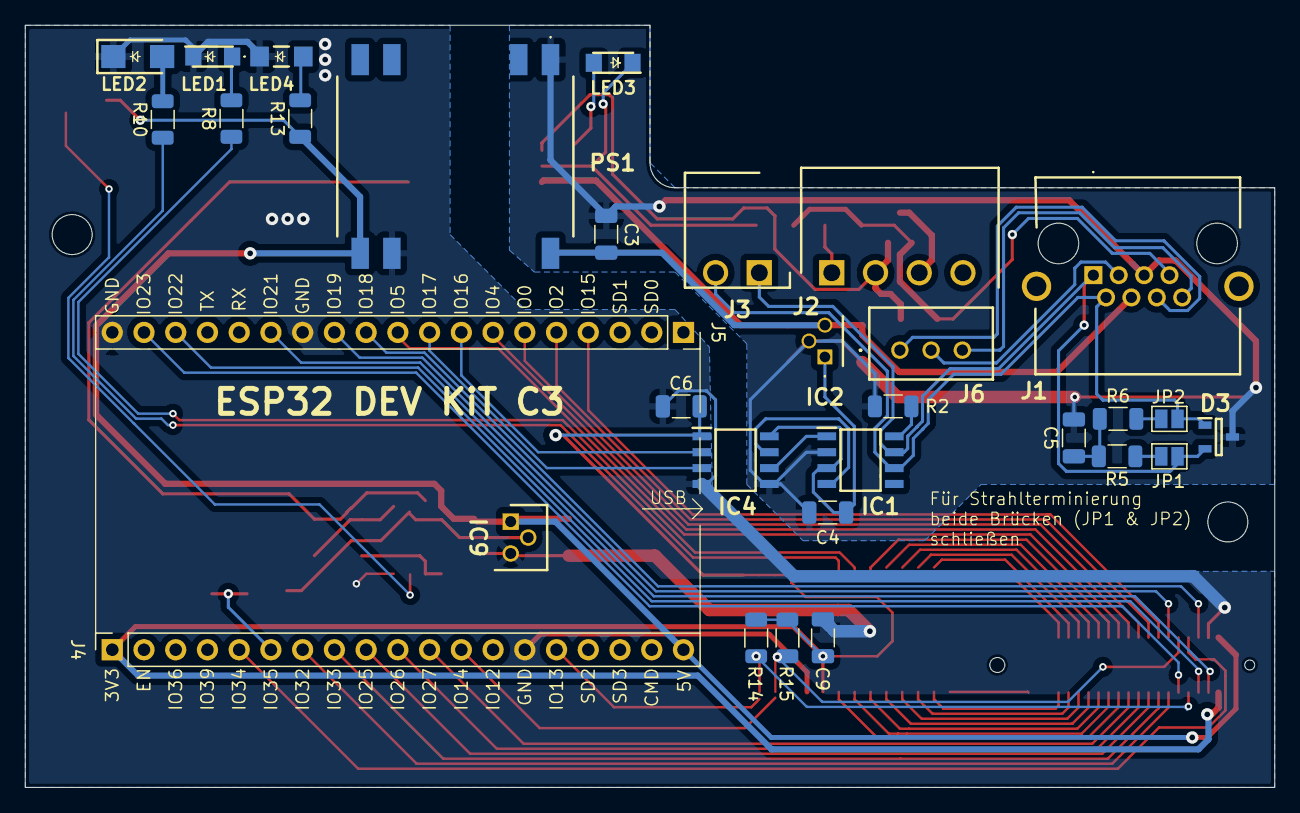
[picture p124: board Hauptmodul.kicad_pcb from below]

Board: 2 copper layers, 100.0 x 61.0 mm, 51 parts (31 on the bottom side), 68 nets.
