LeoWatti99/CANTram-Framework/KiCad Schaltungen/Relais Ausgang Prototyp/Relais Ausgang Prototyp/Relais Ausgang Prototyp.kicad_pcb

## KiCad design KiCad Schaltungen/Relais Ausgang Prototyp/Relais Ausgang Prototyp/Relais Ausgang Prototyp.kicad_pcb (2026-01-24)

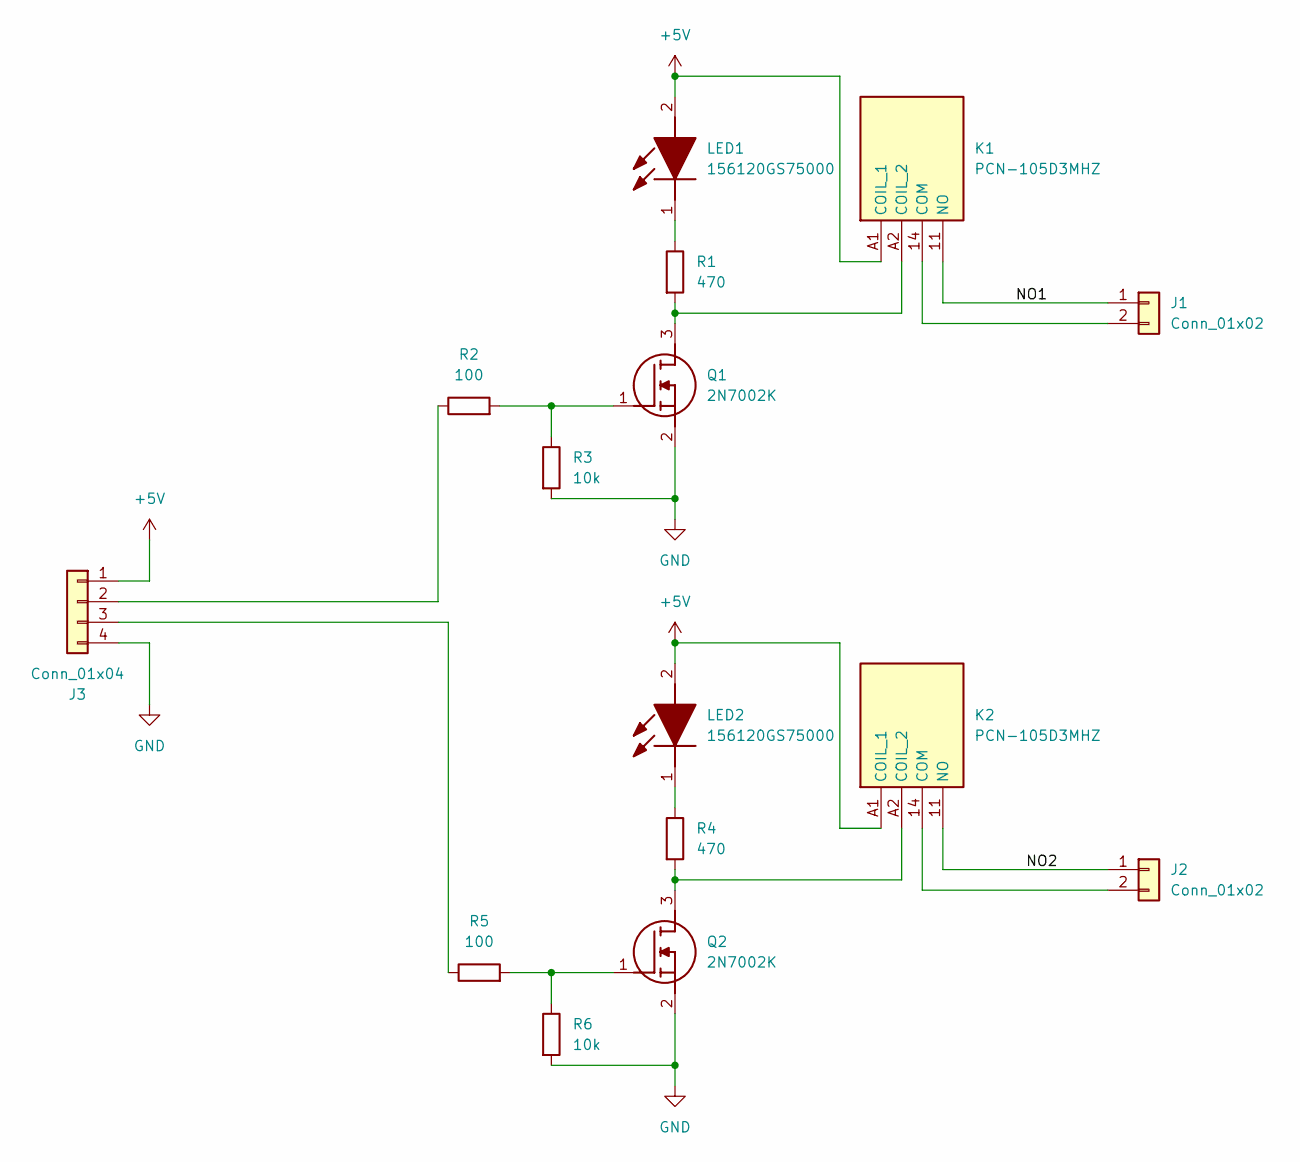
[picture p125: schematic Relais Ausgang Prototyp.kicad_sch]

Parts:
J1, J2: Conn_01x02; PinHeader_1x02_P2.54mm_Vertical
J3: Conn_01x04; PinHeader_1x04_P2.54mm_Vertical
K1, K2: PCN-105D3MHZ; PCN105D3MHZ; Mouser Part Number 677-PCN-105D3MHZ
LED1, LED2: 156120GS75000; Mouser Part Number 710-156120GS75000
Q1, Q2: 2N7002K; SOT95P240X120-3N; Manufacturer_Part_Number 2N7002K; Mouser Part Number 512-2N7002K
R1, R4: 470; R_1206_3216Metric; Manufacturer_Part_Number AC1206FR-07470RL; Mouser Part Number 603-AC1206FR-07470RL
R2, R5: 100; R_1206_3216Metric; Manufacturer_Part_Number AC1206FR-07100RL; Mouser Part Number 603-AC1206FR-07100RL
R3, R6: 10k; R_1206_3216Metric; Manufacturer_Part_Number RC1206FR-1310KL; Mouser Part Number 603-RC1206FR-1310KL

Connections:
+5V: J3.1, K1.A1 (COIL_1), K2.A1 (COIL_1), LED1.2 (A), LED2.2 (A)
/NO1: J1.1, K1.11 (NO)
/NO2: J2.1, K2.11 (NO)
GND: J3.4, Q1.2 (S), Q2.2 (S), R3.2, R6.2
unnamed: J1.2, K1.14 (COM)
unnamed: J2.2, K2.14 (COM)
unnamed: J3.2, R2.1
unnamed: J3.3, R5.1
unnamed: K1.A2 (COIL_2), Q1.3 (D), R1.2
unnamed: K2.A2 (COIL_2), Q2.3 (D), R4.2
unnamed: LED1.1 (K), R1.1
unnamed: LED2.1 (K), R4.1
unnamed: Q1.1 (G), R2.2, R3.1
unnamed: Q2.1 (G), R5.2, R6.1

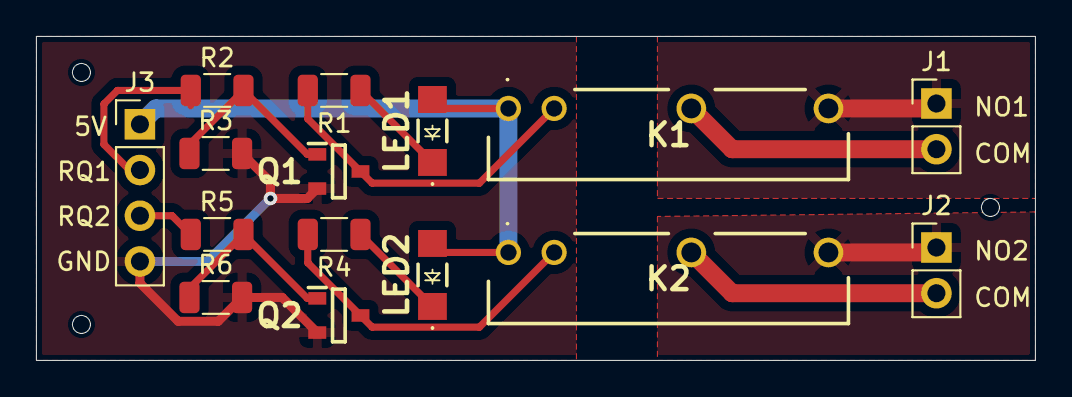
[picture p126: board Relais Ausgang Prototyp.kicad_pcb from above]

Board: 2 copper layers, 55.5 x 18.0 mm, 15 parts (0 on the bottom side), 14 nets.
