LeoWatti99/CANTram-Framework/KiCad Schaltungen/Relaismodul/Relaismodul.kicad_pcb

## KiCad design KiCad Schaltungen/Relaismodul/Relaismodul.kicad_pcb (2026-01-24)

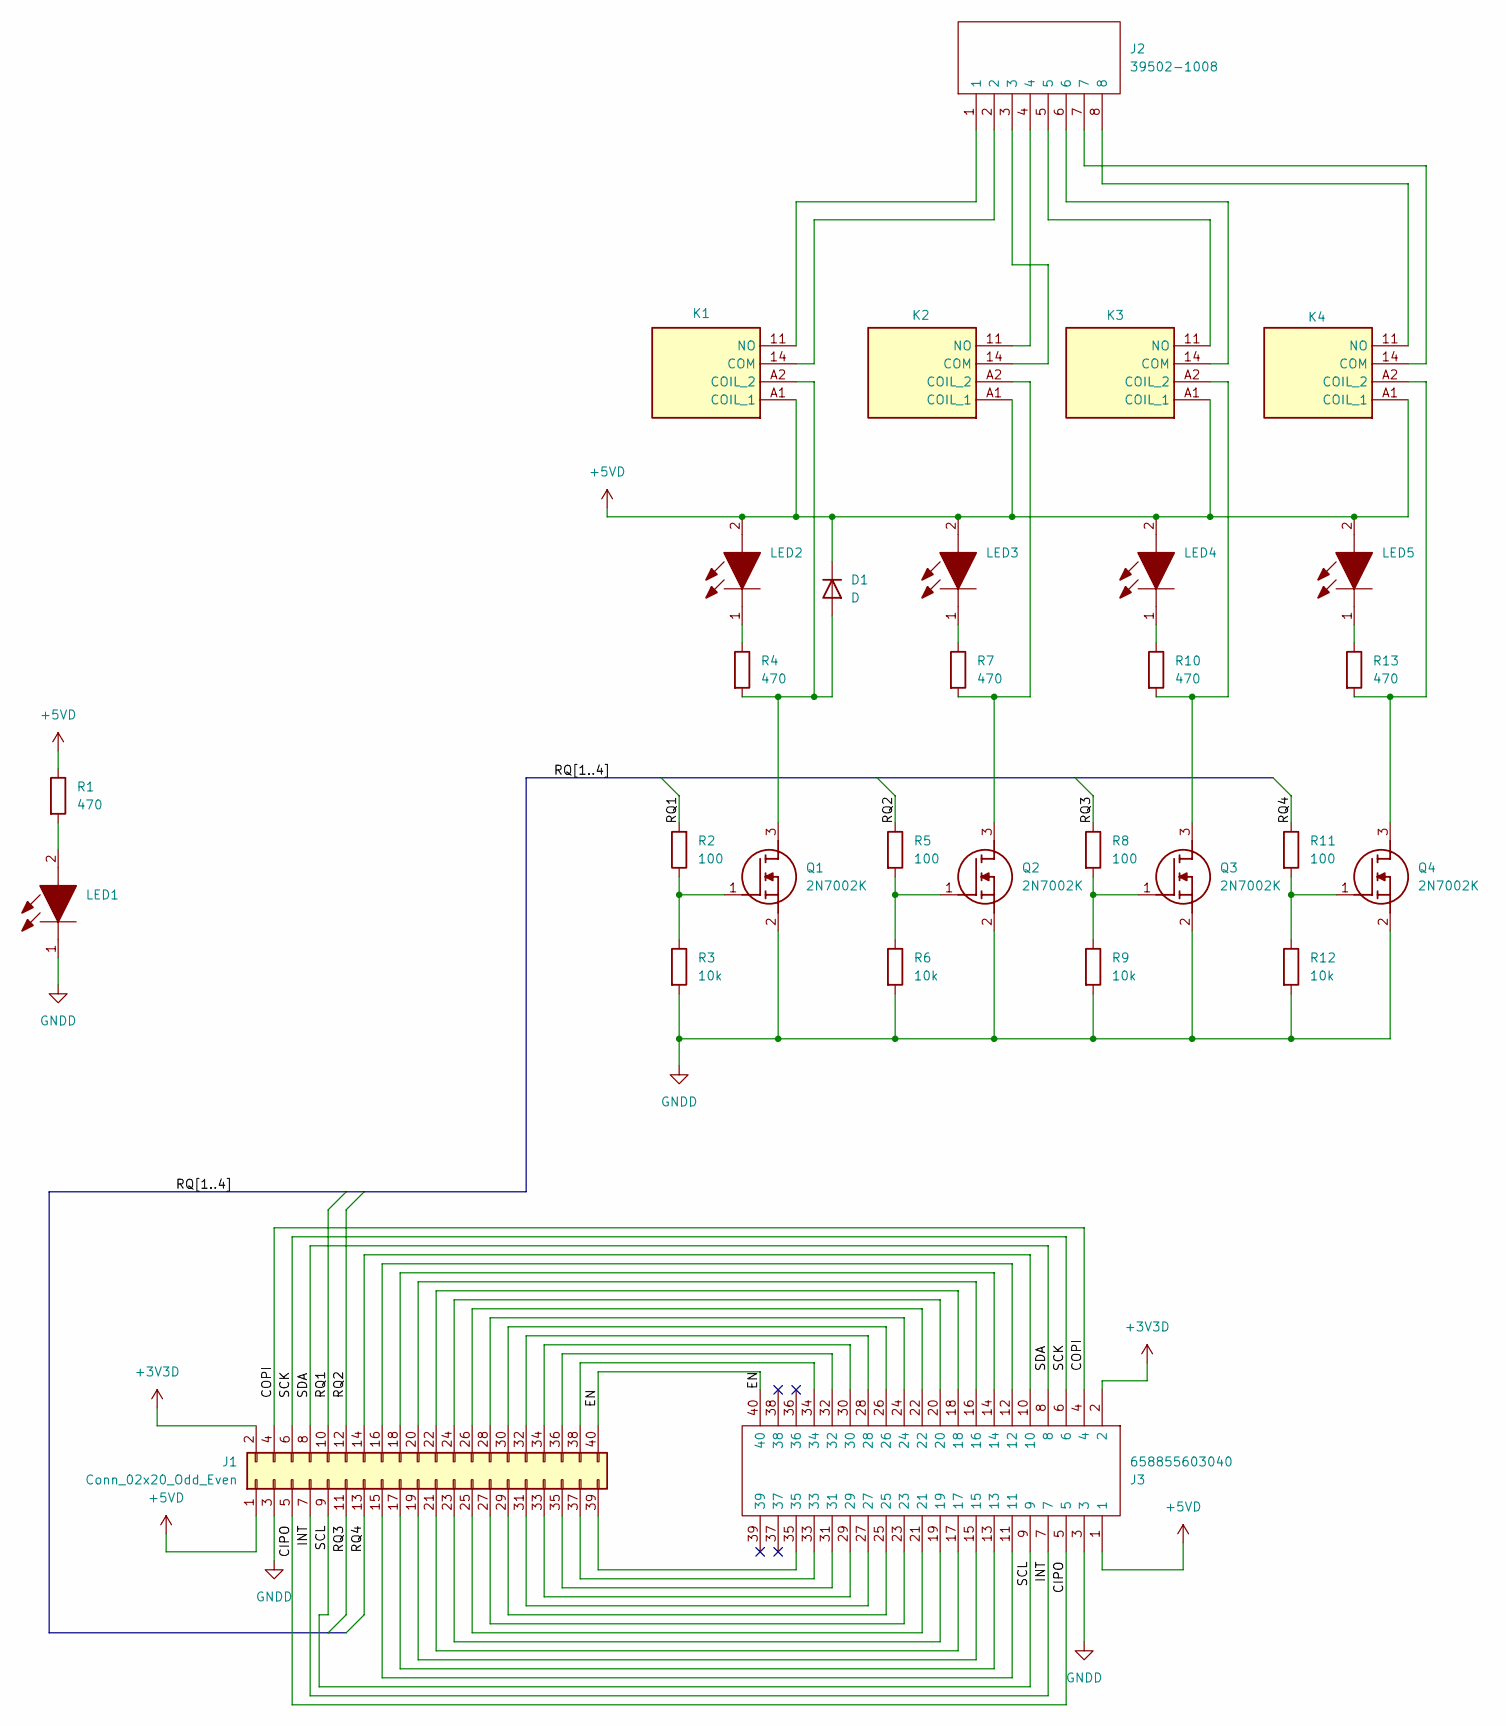
[picture p127: schematic Relaismodul.kicad_sch, CAN Tram Controller Relaismodul]

Parts:
D1: D
J1: Conn_02x20_Odd_Even; PinSocket_2x20_P2.54mm_Vertical
J2: 39502-1008; SHDRRA8W80P0X350_1X8_2940X920X690P; Mouser Part Number 538-39502-1008
J3: 658855603040; Mouser Part Number 710-658855603040
K1, K2, K3, K4: PCN-105D3MHZ; PCN105D3MHZ; Mouser Part Number 677-PCN-105D3MHZ
LED1: 156120GS75000; Mouser Part Number 710-156120GS75000
LED2, LED3, LED4, LED5: 156120YS75000; LEDC5017X140N; Mouser Part Number 710-156120YS75000
Q1, Q2, Q3, Q4: 2N7002K; SOT95P240X120-3N; Manufacturer_Part_Number 2N7002K; Mouser Part Number 512-2N7002K
R1, R4, R7, R10, R13: 470; R_1206_3216Metric; Manufacturer_Part_Number AC1206FR-07470RL; Mouser Part Number 603-AC1206FR-07470RL
R2, R5, R8, R11: 100; R_1206_3216Metric; Manufacturer_Part_Number AC1206FR-07100RL; Mouser Part Number 603-AC1206FR-07100RL
R3, R6, R9, R12: 10k; R_1206_3216Metric; Manufacturer_Part_Number RC1206FR-1310KL; Mouser Part Number 603-RC1206FR-1310KL

Connections:
+3V3D: J1.2, J3.2
+5VD: D1.1 (K), J1.1, J3.1, K1.A1 (COIL_1), K2.A1 (COIL_1), K3.A1 (COIL_1), K4.A1 (COIL_1), LED2.2, LED3.2, LED4.2, LED5.2, R1.1
/CIPO: J1.5, J3.5
/COPI: J1.4, J3.4
/EN: J1.40, J3.40
/INT: J1.7, J3.7
/RQ1: J1.10, R2.2
/RQ2: J1.12, R5.1
/RQ3: J1.11, R8.1
/RQ4: J1.13, R11.1
/SCK: J1.6, J3.6
/SCL: J1.9, J3.9
/SDA: J1.8, J3.8
GNDD: J1.3, J3.3, LED1.1, Q1.2 (S), Q2.2 (S), Q3.2 (S), Q4.2 (S), R3.2, R6.2, R9.2, R12.2
unnamed: J1.14, J3.10
unnamed: J1.15, J3.11
unnamed: J1.16, J3.12
unnamed: J1.17, J3.13
unnamed: J1.18, J3.14
unnamed: J1.19, J3.15
unnamed: J1.20, J3.16
unnamed: J1.21, J3.17
unnamed: J1.22, J3.18
unnamed: J1.23, J3.19
unnamed: J1.24, J3.20
unnamed: J1.25, J3.21
unnamed: J1.26, J3.22
unnamed: J1.27, J3.23
unnamed: J1.28, J3.24
unnamed: J1.29, J3.25
unnamed: J1.30, J3.26
unnamed: J1.31, J3.27
unnamed: J1.32, J3.28
unnamed: J1.33, J3.29
unnamed: J1.34, J3.30
unnamed: J1.35, J3.31
unnamed: J1.36, J3.32
unnamed: J1.37, J3.33
unnamed: J1.38, J3.34
unnamed: J1.39, J3.35
unnamed: D1.2 (A), K1.A2 (COIL_2), Q1.3 (D), R4.2
unnamed: J2.2, K1.14 (COM)
unnamed: J2.1, K1.11 (NO)
unnamed: K2.A2 (COIL_2), Q2.3 (D), R7.2
unnamed: J2.3, K2.14 (COM)
unnamed: J2.4, K2.11 (NO)
unnamed: K3.A2 (COIL_2), Q3.3 (D), R10.2
unnamed: J2.6, K3.14 (COM)
unnamed: J2.5, K3.11 (NO)
unnamed: K4.A2 (COIL_2), Q4.3 (D), R13.2
unnamed: J2.7, K4.14 (COM)
unnamed: J2.8, K4.11 (NO)
unnamed: LED1.2, R1.2
unnamed: LED2.1, R4.1
unnamed: LED3.1, R7.1
unnamed: LED4.1, R10.1
unnamed: LED5.1, R13.1
unnamed: Q1.1 (G), R2.1, R3.1
unnamed: Q2.1 (G), R5.2, R6.1
unnamed: Q3.1 (G), R8.2, R9.1
unnamed: Q4.1 (G), R11.2, R12.1

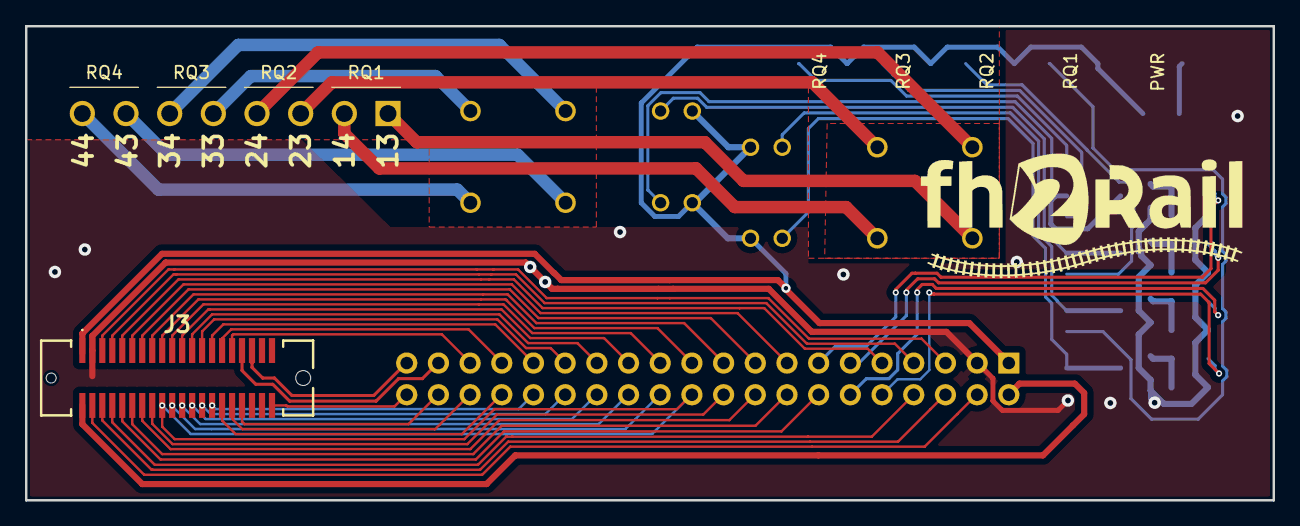
[picture p128: board Relaismodul.kicad_pcb from above]

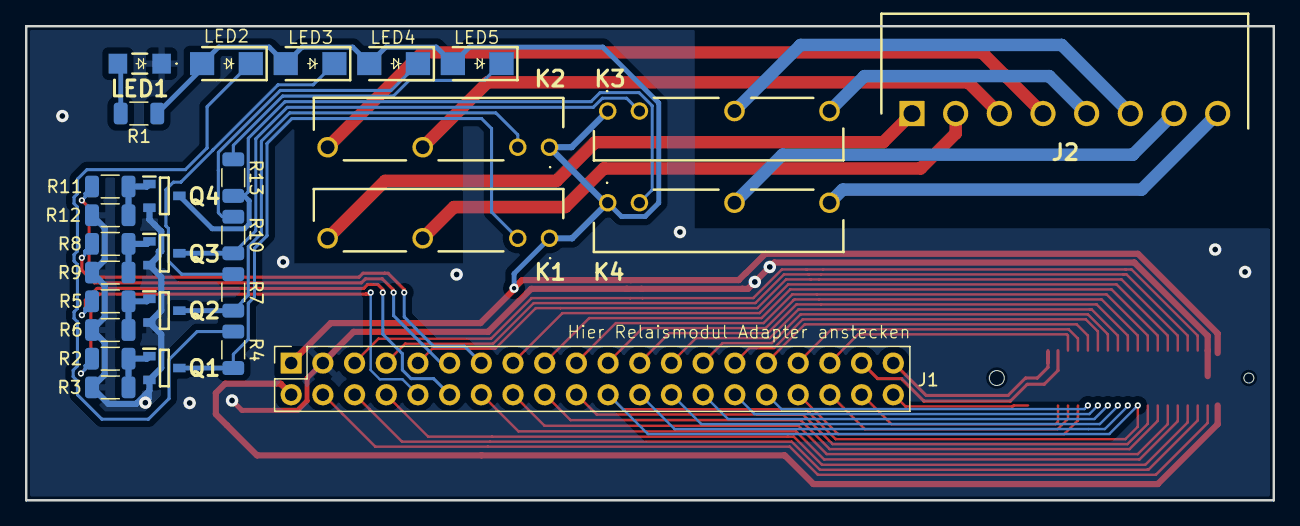
[picture p129: board Relaismodul.kicad_pcb from below]

Board: 2 copper layers, 100.0 x 38.0 mm, 29 parts (28 on the bottom side), 61 nets.
