LeoWatti99/CANTram-Framework/Framework/include/ISO1I813T_registers.h

#ifndef ISO1I813T_REGISTERS_H
#define ISO1I813T_REGISTERS_H

#include "Debug.h"

#define ISO1I813T_REG_DIAG 0x00
#define ISO1I813T_REG_INPDATA 0x02
#define ISO1I813T_REG_GLERR 0x04

#define ISO1I813T_REG_COEFIL0_READ 0x06
#define ISO1I813T_REG_COEFIL1_READ 0x08
#define ISO1I813T_REG_COEFIL2_READ 0x0A
#define ISO1I813T_REG_COEFIL3_READ 0x0C
#define ISO1I813T_REG_COEFIL4_READ 0x0E
#define ISO1I813T_REG_COEFIL5_READ 0x10
#define ISO1I813T_REG_COEFIL6_READ 0x12
#define ISO1I813T_REG_COEFIL7_READ 0x14

#define ISO1I813T_REG_COEFIL0_WRITE 0x86
#define ISO1I813T_REG_COEFIL1_WRITE 0x88
#define ISO1I813T_REG_COEFIL2_WRITE 0x8A
#define ISO1I813T_REG_COEFIL3_WRITE 0x8C
#define ISO1I813T_REG_COEFIL4_WRITE 0x8E
#define ISO1I813T_REG_COEFIL5_WRITE 0x90
#define ISO1I813T_REG_COEFIL6_WRITE 0x92
#define ISO1I813T_REG_COEFIL7_WRITE 0x94

#define ISO1I813T_WB_BIT 4

#define ISO1I813T_REG_INTERR 0x16
#define ISO1I813T_REG_GLCFG_READ 0x18
#define ISO1I813T_REG_GLCFG_WRITE 0x98

#define ISO1I813T_WRITE_BIT 8

#endif
