LeoWatti99/CANTram-Framework/Framework/include/MAX22531_registers.h

#ifndef MAX22531_REGISTERS_H
#define MAX22531_REGISTERS_H

#include "Debug.h"

#define MAX22531_REG_ID 0x00
#define MAX22531_REG_ADC_1_STATUS  0x01
#define MAX22531_REG_ADC_2_STATUS  0x02
#define MAX22531_REG_ADC_3_STATUS  0x03 
#define MAX22531_REG_ADC_4_STATUS  0x04
#define MAX22531_REG_FADC_1_STATUS  0x05
#define MAX22531_REG_FADC_2_STATUS  0x06
#define MAX22531_REG_FADC_3_STATUS  0x07
#define MAX22531_REG_FADC_4_STATUS  0x08

#define MAX22531_REG_COUTHI_1  0x09
#define MAX22531_REG_COUTHI_2  0x0A
#define MAX22531_REG_COUTHI_3  0x0B
#define MAX22531_REG_COUTHI_4  0x0C
#define MAX22531_REG_COUTLO_1  0x0D
#define MAX22531_REG_COUTLO_2  0x0E
#define MAX22531_REG_COUTLO_3  0x0F
#define MAX22531_REG_COUTLO_4  0x10

#define MAX22531_REG_COUT_STATUS  0x11
#define MAX22531_REG_INTERRUPT_STATUS  0x12
#define MAX22531_REG_INTERRUPT_ENABLE  0x13
#define MAX22531_REG_CONTROL  0x14

#define MAX22531_WRITE_BIT 1
#define MAX22531_BURST_BIT 0
#define MAX22531_ADDRESS_OFFSET 2

#define MAX22531_BIT_POR_FLAG 7

#define MAX22531_BIT_HW_RESET 0
#define MAX22531_BIT_SW_RESET 1
#define MAX22531_BIT_CLEAR_POR_FLAG 2   

#define MAX22531_MASK_12_BIT 0b0000111111111111

#define MAX22531_UNFILTERED MAX22531_REG_ADC_1_STATUS
#define MAX22531_FILTERED MAX22531_REG_FADC_1_STATUS

#endif
