LeoWatti99/CANTram-Framework/Framework/test/.test_template.cpp

#include <Arduino.h>
#include <unity.h>

//Runs before tests
void setUp(){

}

//Runs after tests
void tearDown(){

}

/* Write a function for each test*/


//Run tests
void setup(){
    delay(2000);
    UNITY_BEGIN();
    //RUN_TEST(test_function);
    UNITY_END();
}

void loop(){

}
